wrog0003/ECE4191/CAD/Self_designed_parts/Wheels_Main.SLDPRT

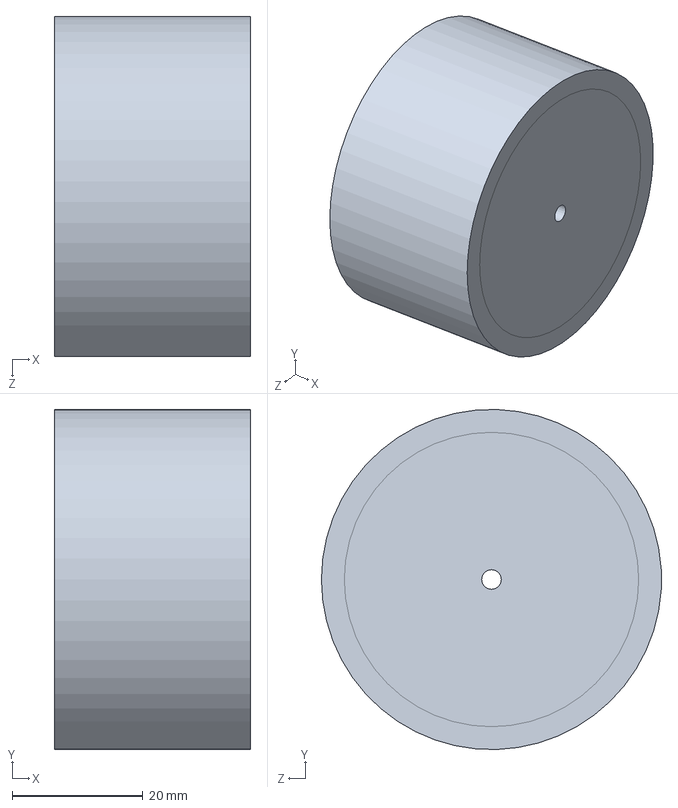
[picture p8: CAD file, 2024-09-03]
CAD/Self_designed_parts/Wheels_Main.SLDPRT
30.0 x 52.0 x 52.0 mm
