wrog0003/ECE4191/CAD/Self_designed_parts/Wheels_Secondary.SLDASM

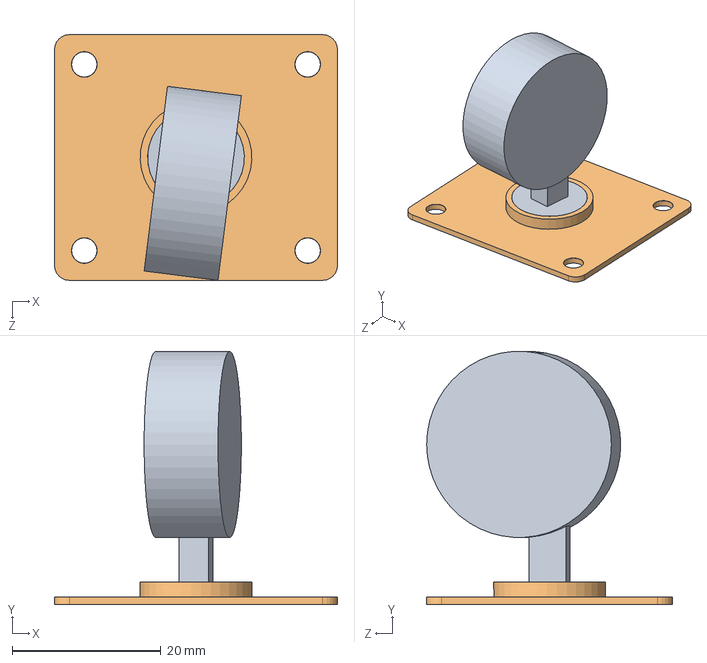
[picture p9: CAD file, 2024-09-03]
CAD/Self_designed_parts/Wheels_Secondary.SLDASM
38.0 x 34.0 x 33.0 mm
Wheels_Secondary_Bottom
Wheels_Secondary_Top
