wrog0003/ECE4191/CAD/Self_designed_parts/TestingAssembly.SLDASM

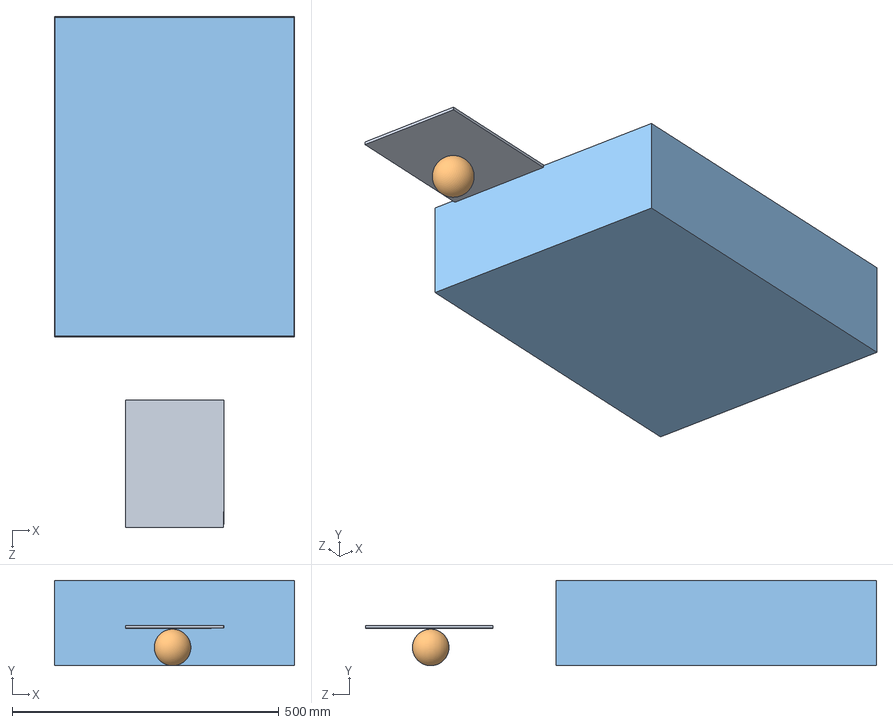
[picture p10: CAD file, 2024-08-25]
CAD/Self_designed_parts/TestingAssembly.SLDASM
450.0 x 160.0 x 957.0 mm
Baseplate
TennisBall(Max)
CollectionBox
