wrog0003/ECE4191/CAD/Self_designed_parts/BumperAssembly.SLDASM

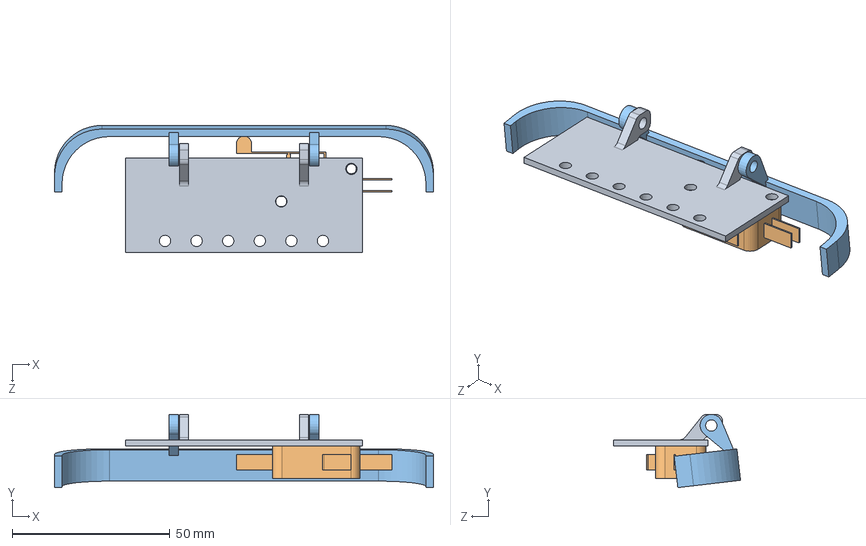
[picture p11: CAD file, 2024-08-25]
CAD/Self_designed_parts/BumperAssembly.SLDASM
120.0 x 23.2 x 40.3 mm
BumperBase
V-156-125 Switch
Bumper
