wrog0003/ECE4191/CAD/Self_designed_parts/CameraAndMount.SLDASM

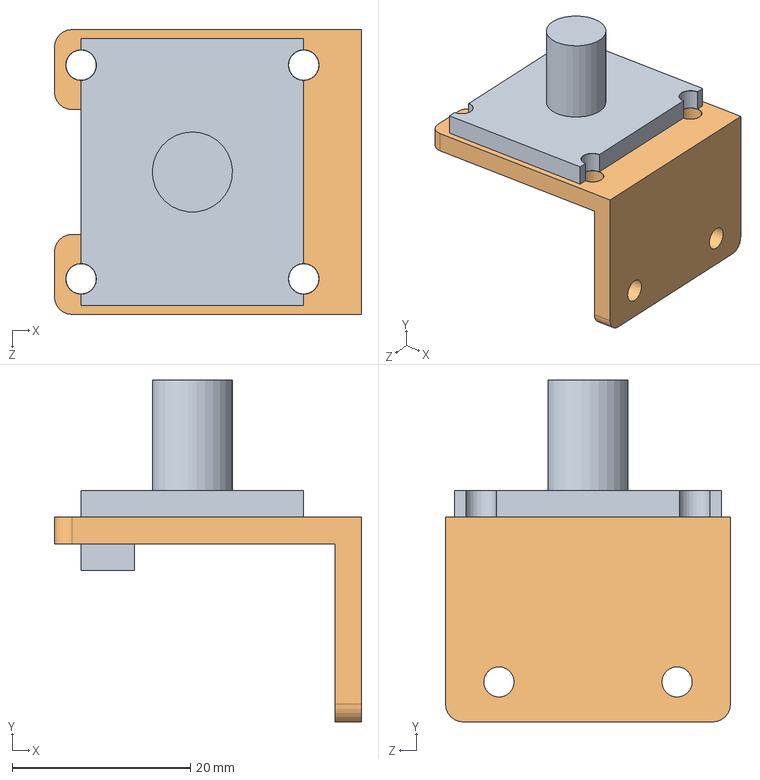
[picture p12: CAD file, 2024-08-25]
CAD/Self_designed_parts/CameraAndMount.SLDASM
34.5 x 38.4 x 32.0 mm
CameraBase
CameraMount
