wrog0003/ECE4191/CAD/Self_designed_parts/ClawAssembly.SLDASM

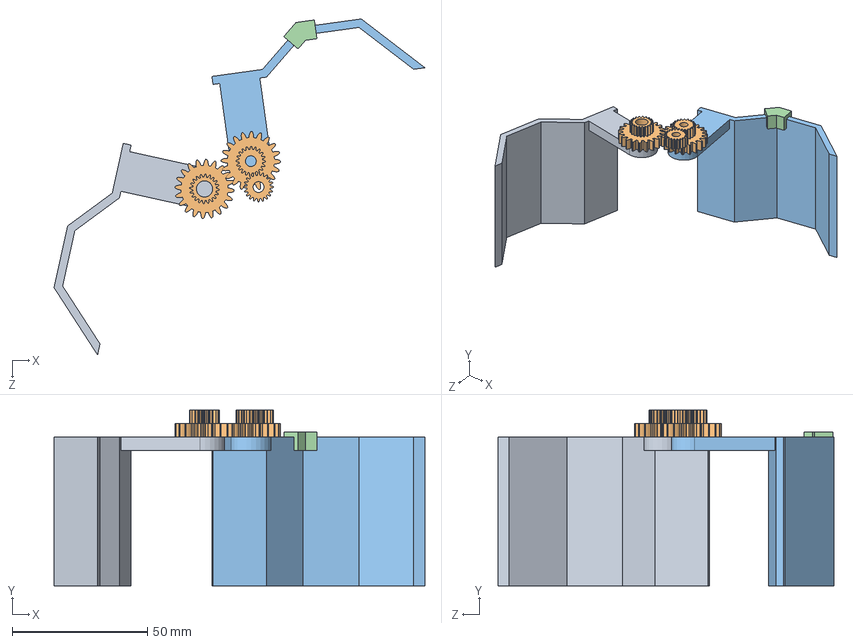
[picture p13: CAD file, 2024-08-25]
CAD/Self_designed_parts/ClawAssembly.SLDASM
137.2 x 65.0 x 124.3 mm
ClawRight
spur gear_am x 6
ClawLeft
Part1^ClawLeftAssembly
