wrog0003/ECE4191/CAD/CameraMount/CameraMountClamp.SLDPRT

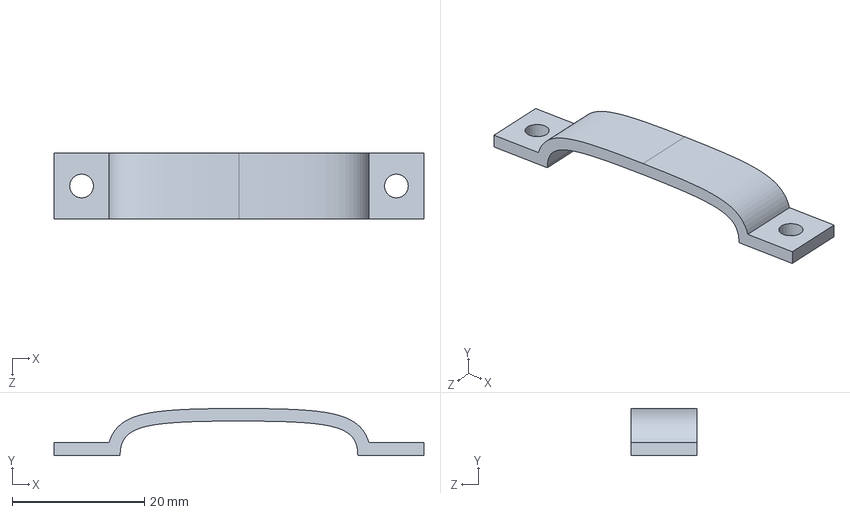
[picture p14: CAD file, 2024-10-14]
CAD/CameraMount/CameraMountClamp.SLDPRT
55.9 x 7.10 x 10.0 mm
