wrog0003/ECE4191/CAD/Ready to Make/3D Printing/Track_Gear.STL

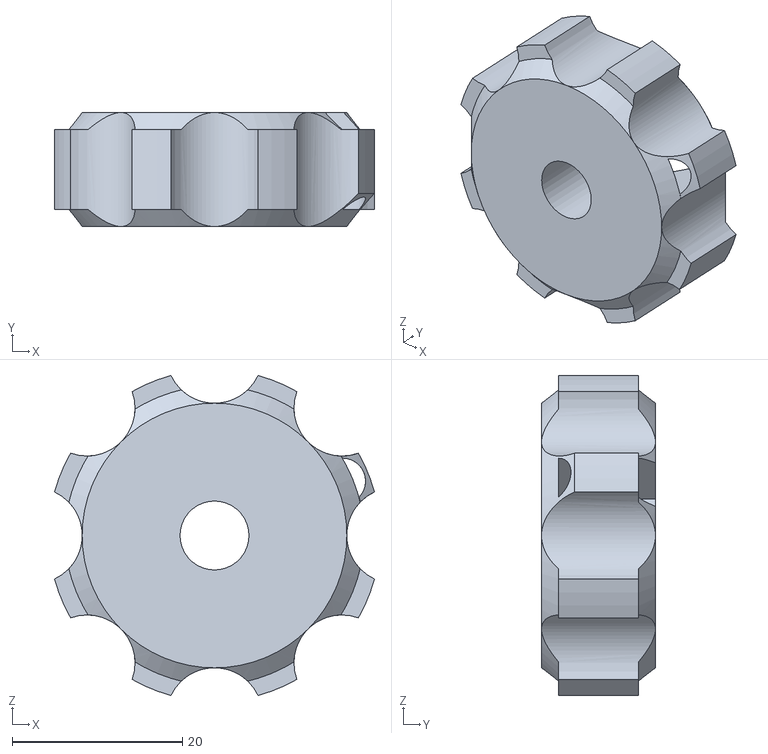
[picture p15: CAD file, 2024-09-18]
CAD/Ready to Make/3D Printing/Track_Gear.STL
37.6 x 13.4 x 37.6
