wrog0003/ECE4191/CAD/Ready to Make/Laser Cutting/PusherFlap.DXF

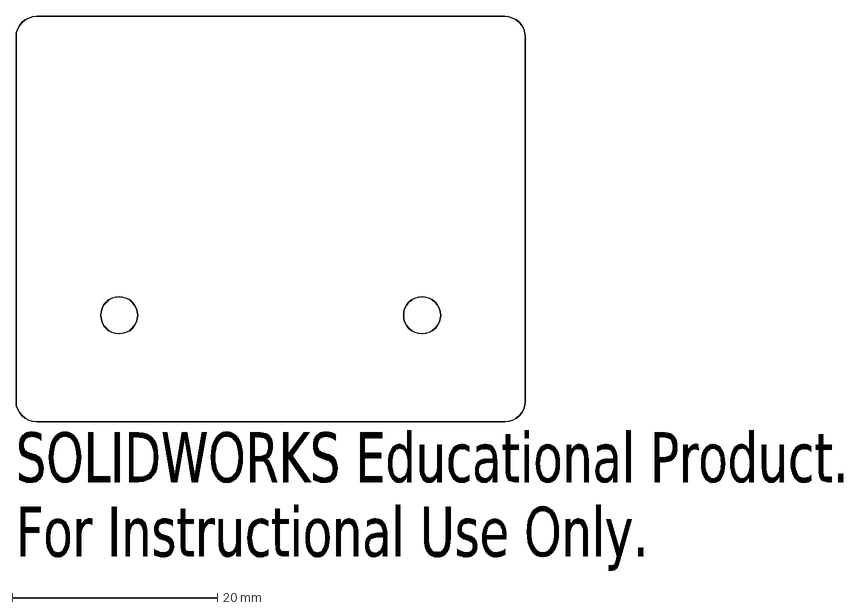
[picture p16: CAD file, 2024-09-16]
CAD/Ready to Make/Laser Cutting/PusherFlap.DXF
SOLIDWORKS Educational Product.
For Instructional Use Only.
