wrog0003/ECE4191/CAD/Self_designed_parts/Adaptors/GearMount_new.SLDPRT

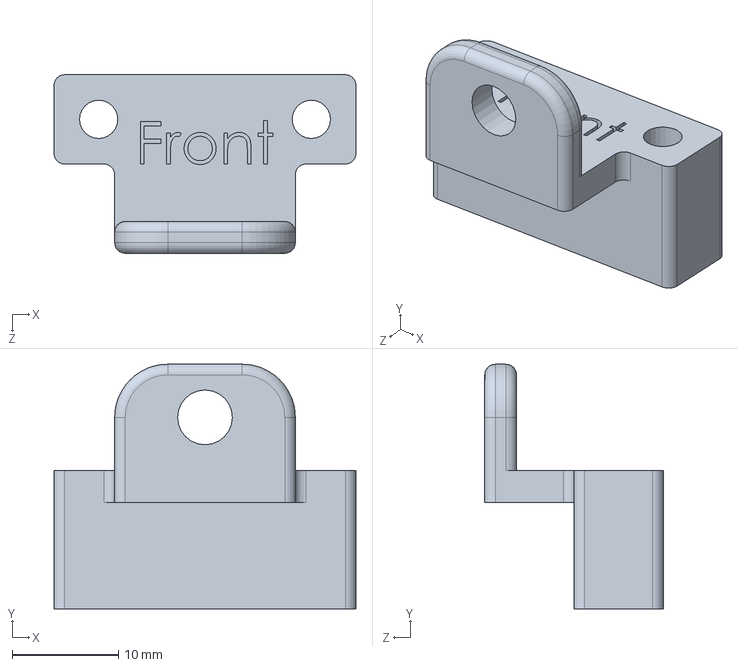
[picture p17: CAD file, 2024-10-04]
CAD/Self_designed_parts/Adaptors/GearMount_new.SLDPRT
28.4 x 23.0 x 16.8 mm
