wrog0003/ECE4191/CAD/Self_designed_parts/CameraMountSection/Battery.SLDPRT

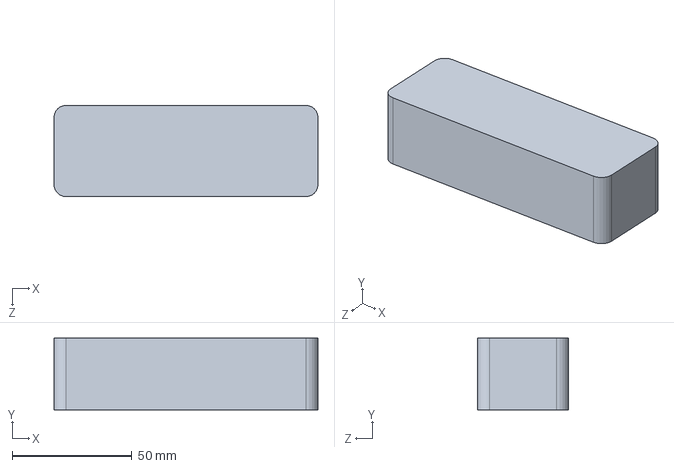
[picture p18: CAD file, 2024-10-14]
CAD/Self_designed_parts/CameraMountSection/Battery.SLDPRT
110.0 x 30.0 x 38.0 mm
