wrog0003/ECE4191/CAD/Self_designed_parts/FunnelMount/FunnelAdaptor.SLDPRT

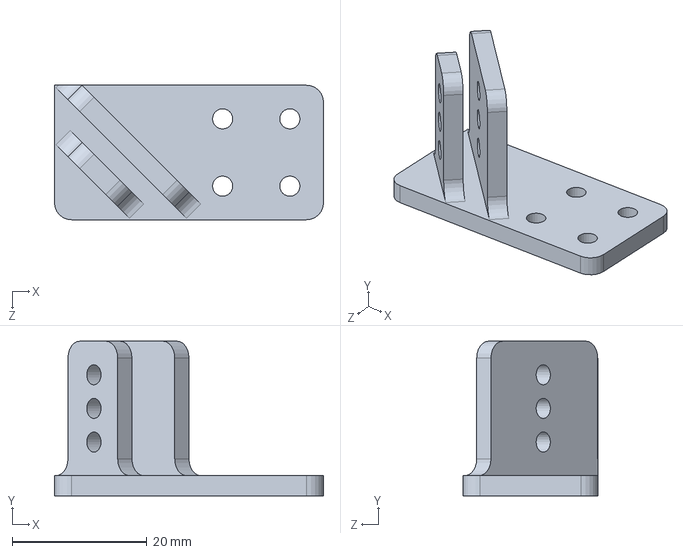
[picture p19: CAD file, 2024-10-14]
CAD/Self_designed_parts/FunnelMount/FunnelAdaptor.SLDPRT
40.0 x 23.0 x 20.0 mm
