wrog0003/ECE4191/CAD/Self_designed_parts/HailMary/HM_HUBCAP.SLDPRT

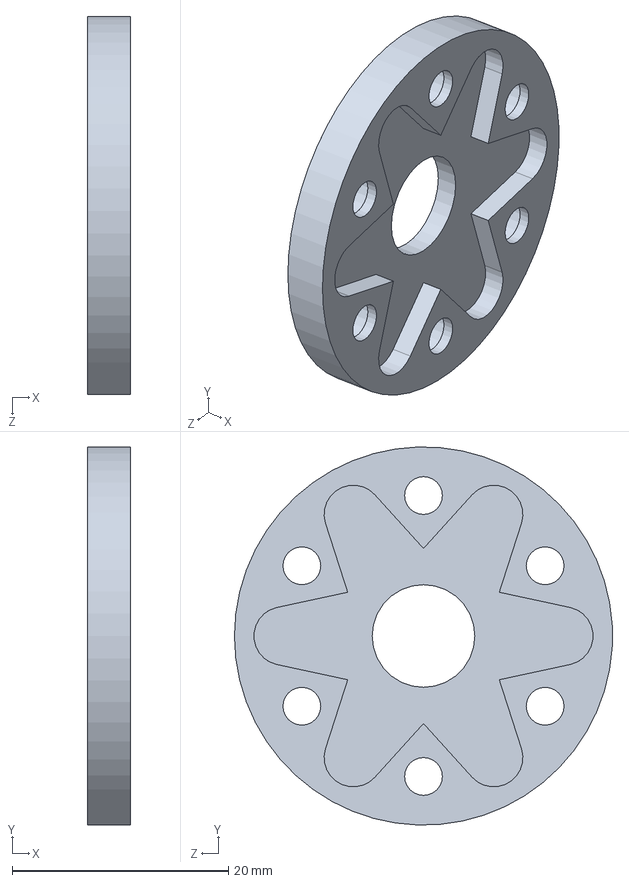
[picture p20: CAD file, 2024-10-16]
CAD/Self_designed_parts/HailMary/HM_HUBCAP.SLDPRT
4.00 x 35.0 x 35.0 mm
