wrog0003/ECE4191/CAD/Self_designed_parts/SupportBracket.SLDPRT

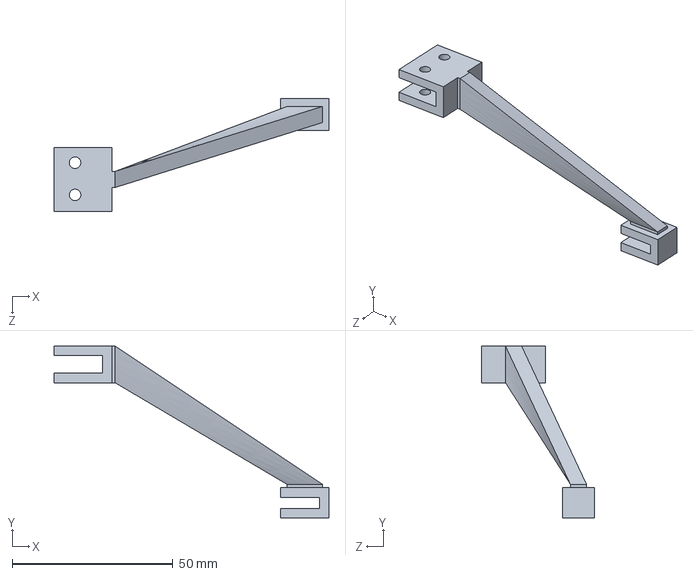
[picture p21: CAD file, 2024-10-14]
CAD/Self_designed_parts/SupportBracket.SLDPRT
85.5 x 53.4 x 35.2 mm
