wrog0003/ECE4191/CAD/CameraMount/CameraMountBase.SLDPRT

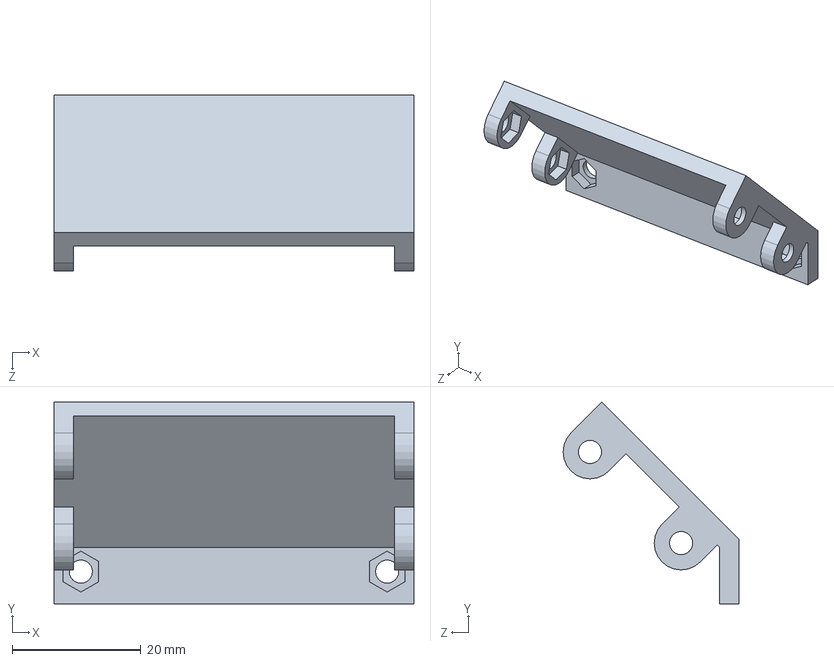
[picture p22: CAD file, 2024-10-14]
CAD/CameraMount/CameraMountBase.SLDPRT
55.9 x 31.3 x 27.3 mm
