wrog0003/ECE4191/CAD/Given_parts/MG995/MG995.SLDPRT

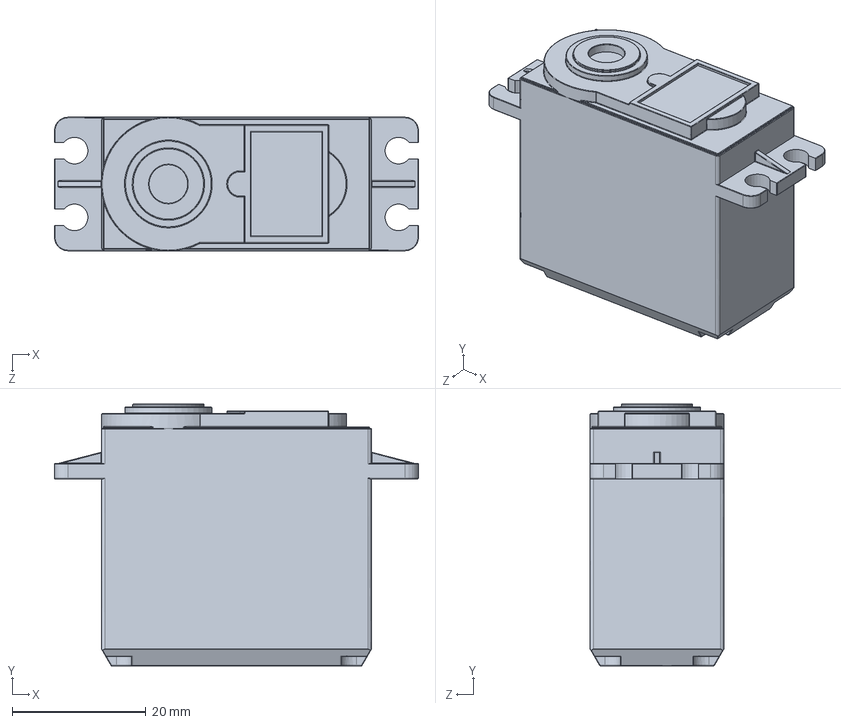
[picture p23: CAD file, 2024-10-05]
CAD/Given_parts/MG995/MG995.SLDPRT
54.5 x 39.2 x 20.0 mm
