wrog0003/ECE4191/CAD/Given_parts/Microswitch.SLDPRT

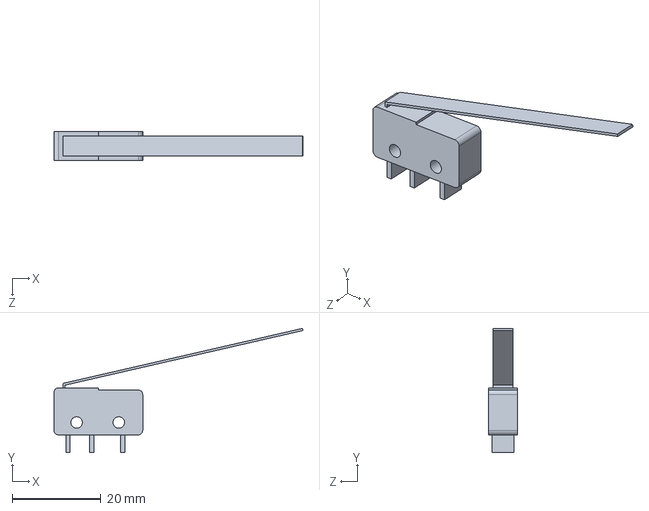
[picture p24: CAD file, 2024-10-04]
CAD/Given_parts/Microswitch.SLDPRT
56.1 x 28.0 x 6.50 mm
