wrog0003/ECE4191/CAD/Ready to Make/3D Printing/SG90C Gear Cap.STL

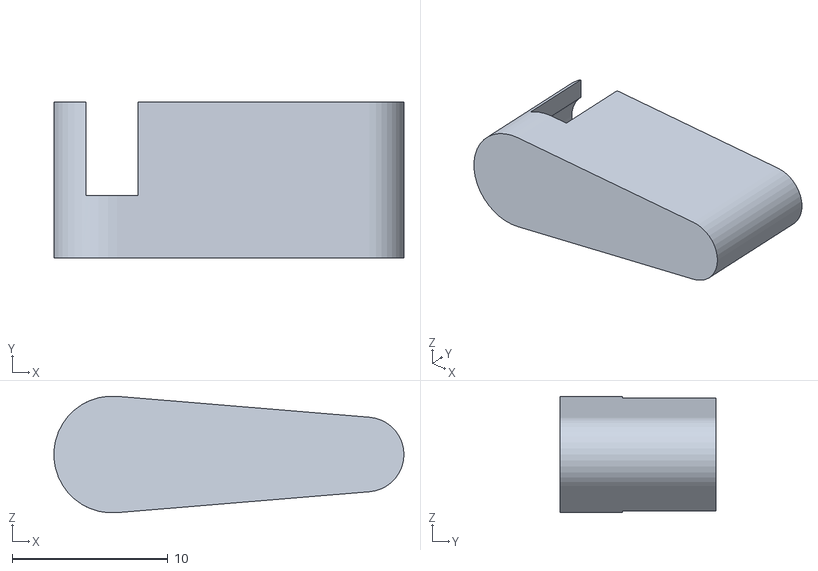
[picture p25: CAD file, 2024-09-18]
CAD/Ready to Make/3D Printing/SG90C Gear Cap.STL
22.5 x 10.0 x 7.48
