wrog0003/ECE4191/CAD/Ready to Make/Laser Cutting/RampChute.DXF

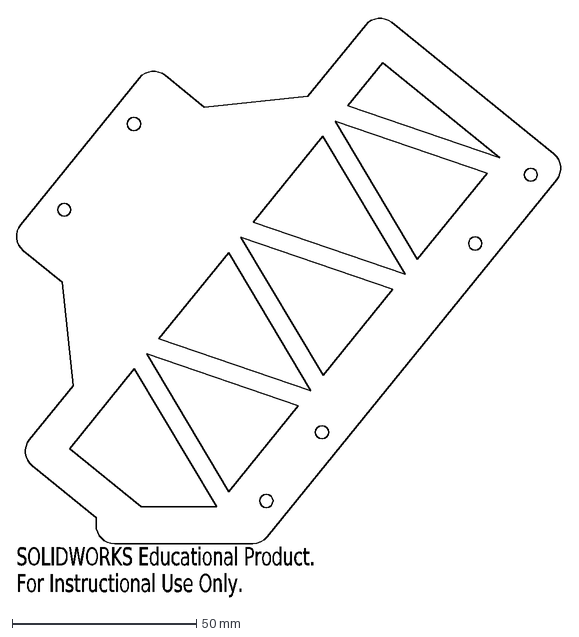
[picture p26: CAD file, 2024-09-16]
CAD/Ready to Make/Laser Cutting/RampChute.DXF
SOLIDWORKS Educational Product.
For Instructional Use Only.
