wrog0003/ECE4191/CAD/Self_designed_parts/Adaptors/GearMountRaiser.SLDPRT

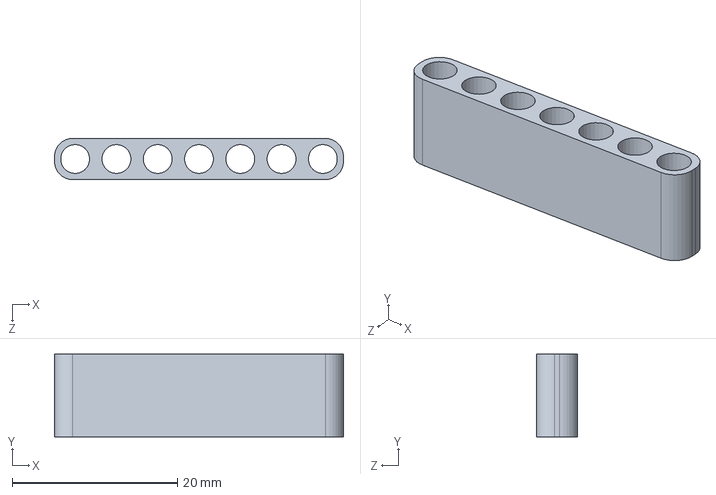
[picture p27: CAD file, 2024-10-02]
CAD/Self_designed_parts/Adaptors/GearMountRaiser.SLDPRT
35.0 x 10.0 x 5.00 mm
