wrog0003/ECE4191/CAD/Self_designed_parts/CameraMountSection/NewServoMountSpacer.SLDPRT

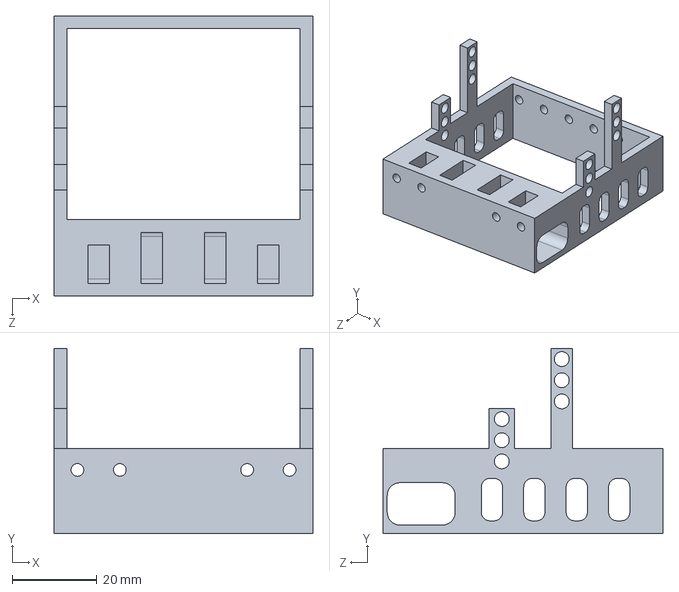
[picture p28: CAD file, 2024-10-14]
CAD/Self_designed_parts/CameraMountSection/NewServoMountSpacer.SLDPRT
61.0 x 43.6 x 66.0 mm
