wrog0003/ECE4191/CAD/Self_designed_parts/FunnelMount/FunnelPlate.SLDPRT

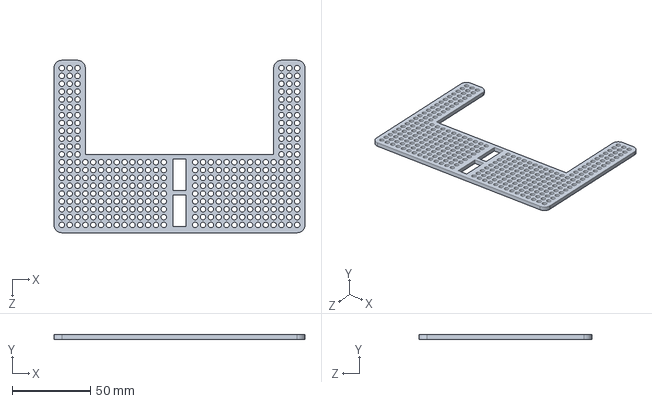
[picture p29: CAD file, 2024-10-14]
CAD/Self_designed_parts/FunnelMount/FunnelPlate.SLDPRT
160.0 x 3.00 x 110.0 mm
