wrog0003/ECE4191/CAD/Self_designed_parts/MotorMount_Helper.SLDPRT

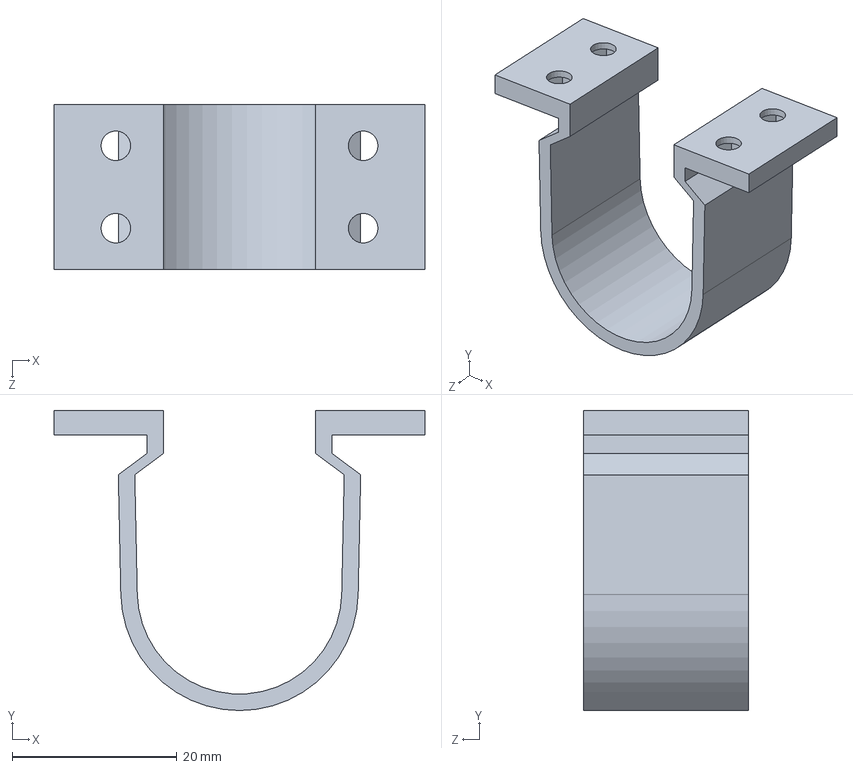
[picture p30: CAD file, 2024-10-14]
CAD/Self_designed_parts/MotorMount_Helper.SLDPRT
45.0 x 36.4 x 20.0 mm
