wrog0003/ECE4191/CAD/CameraMount/CameraLifter.SLDPRT

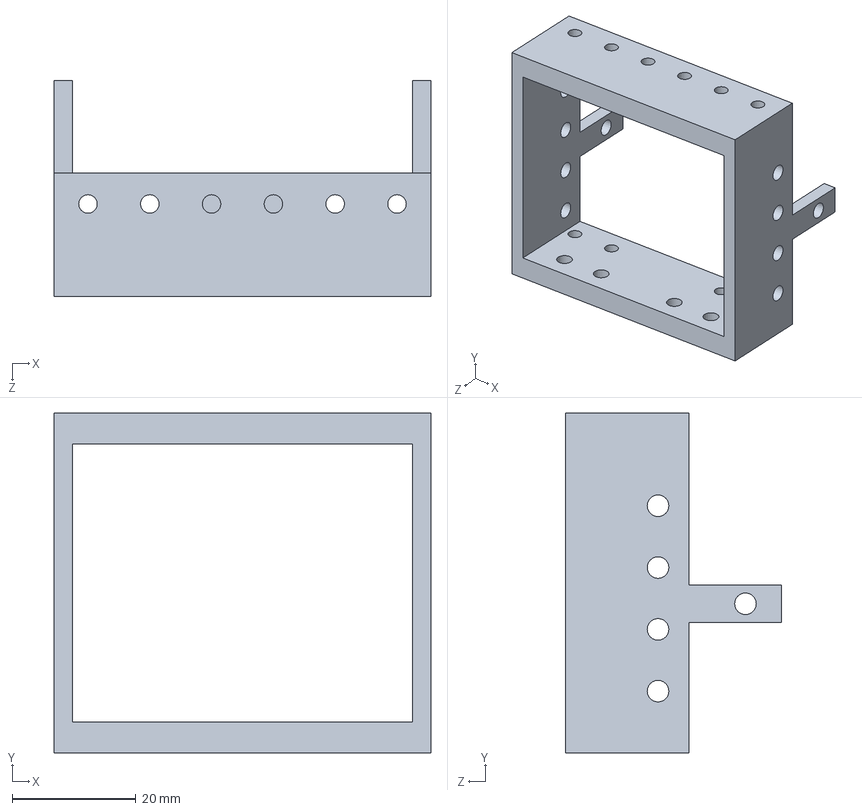
[picture p31: CAD file, 2024-09-30]
CAD/CameraMount/CameraLifter.SLDPRT
61.0 x 55.0 x 35.0 mm
