wrog0003/ECE4191/CAD/Given_parts/Servo_MG995_Star_horn.SLDPRT

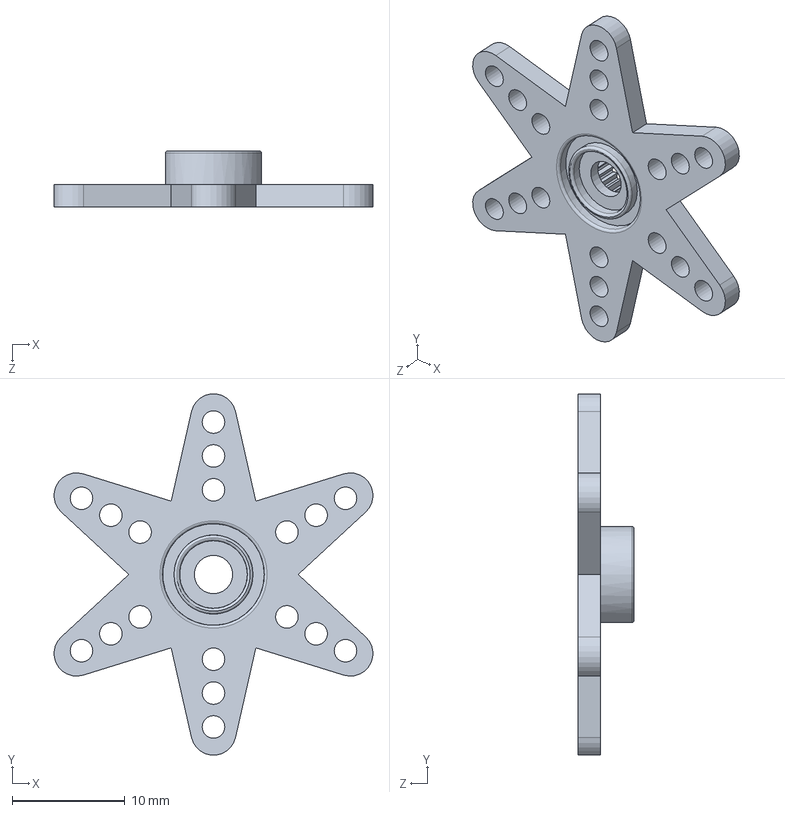
[picture p32: CAD file, 2024-09-30]
CAD/Given_parts/Servo_MG995_Star_horn.SLDPRT
28.2 x 32.0 x 5.00 mm
