wrog0003/ECE4191/CAD/Ready to Make/Laser Cutting/Baseplate.DXF

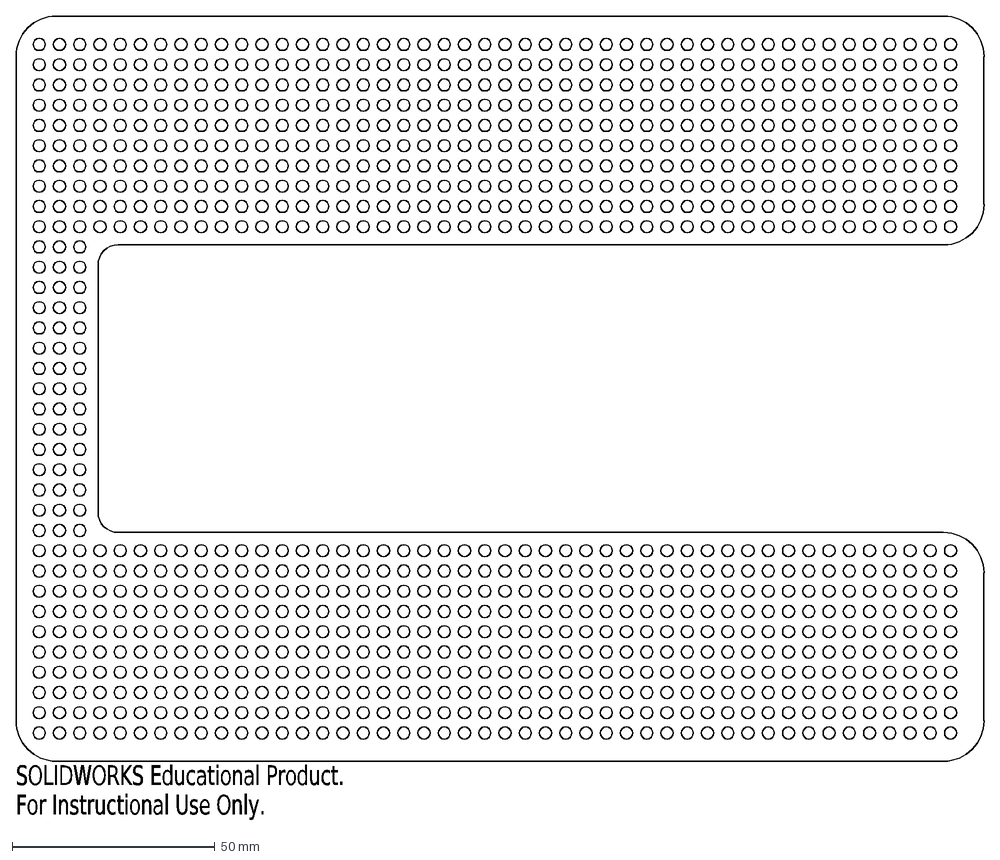
[picture p33: CAD file, 2024-09-16]
CAD/Ready to Make/Laser Cutting/Baseplate.DXF
SOLIDWORKS Educational Product.
For Instructional Use Only.
