wrog0003/ECE4191/CAD/Self_designed_parts/Adaptors/PCBHolder.SLDPRT

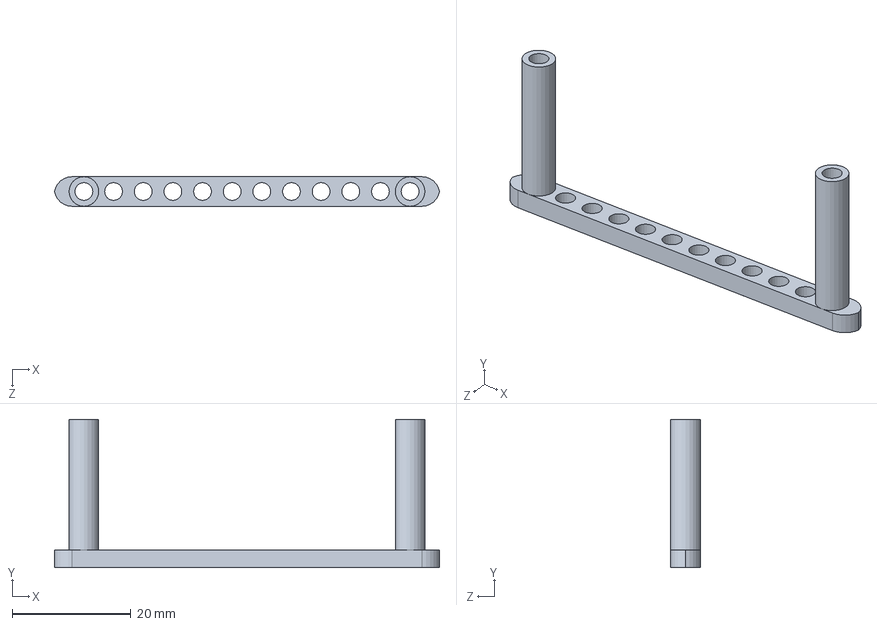
[picture p34: CAD file, 2024-09-27]
CAD/Self_designed_parts/Adaptors/PCBHolder.SLDPRT
64.9 x 25.0 x 5.00 mm
