wrog0003/ECE4191/CAD/Self_designed_parts/BallChute.SLDPRT

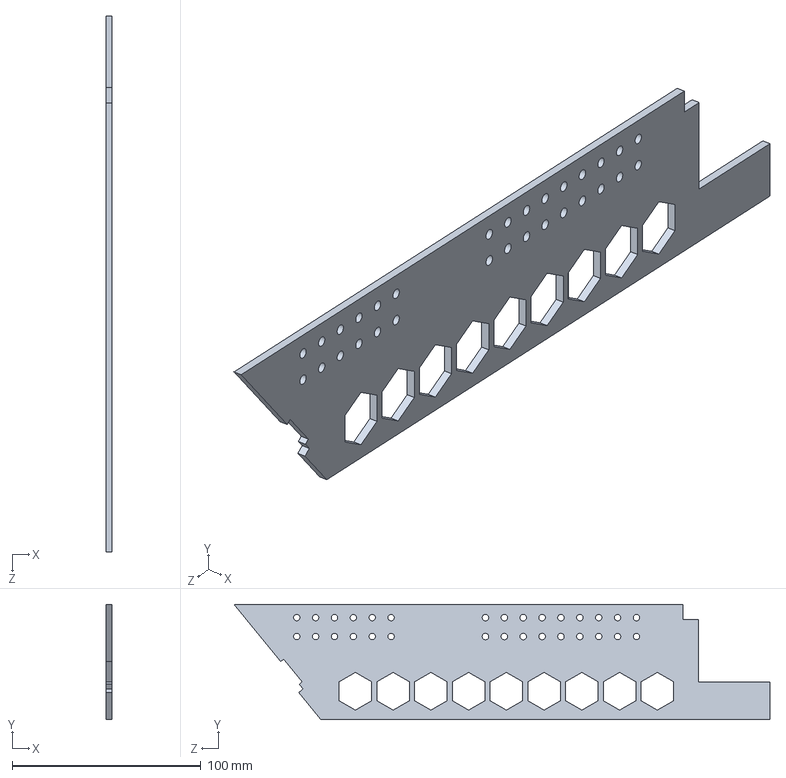
[picture p35: CAD file, 2024-10-14]
CAD/Self_designed_parts/BallChute.SLDPRT
3.00 x 61.0 x 284.0 mm
