wrog0003/ECE4191/CAD/Self_designed_parts/HailMary/HM_LOWERRAMP.SLDPRT

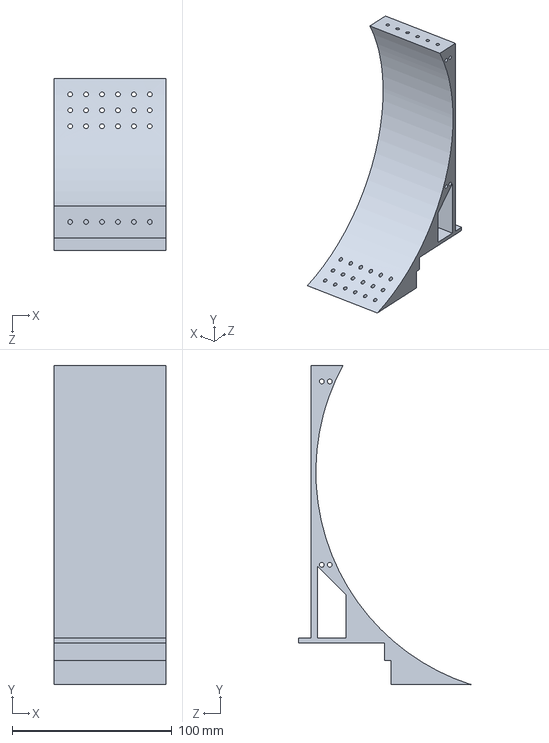
[picture p36: CAD file, 2024-10-16]
CAD/Self_designed_parts/HailMary/HM_LOWERRAMP.SLDPRT
70.0 x 200.0 x 108.0 mm
