wrog0003/ECE4191/CAD/CameraMount/CM_Vertical.SLDPRT

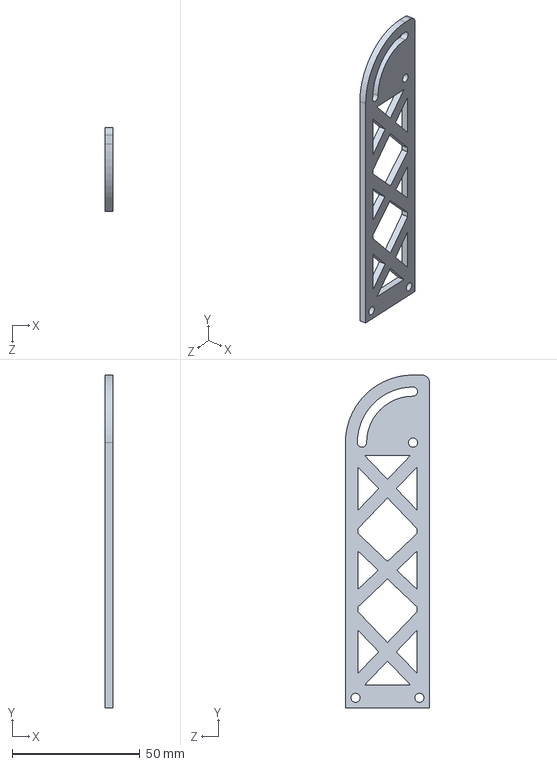
[picture p37: CAD file, 2024-09-16]
CAD/CameraMount/CM_Vertical.SLDPRT
3.00 x 130.5 x 33.0 mm
