wrog0003/ECE4191/CAD/Given_parts/MG995/Shaft.SLDPRT

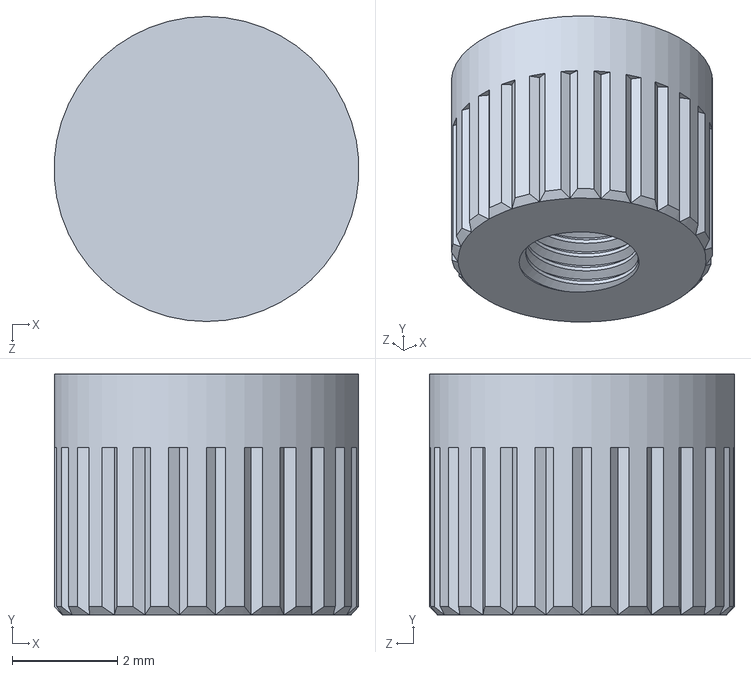
[picture p38: CAD file, 2024-09-30]
CAD/Given_parts/MG995/Shaft.SLDPRT
5.79 x 4.58 x 5.80 mm
