wrog0003/ECE4191/CAD/Given_parts/Raspberry_Pi_4_B.SLDPRT

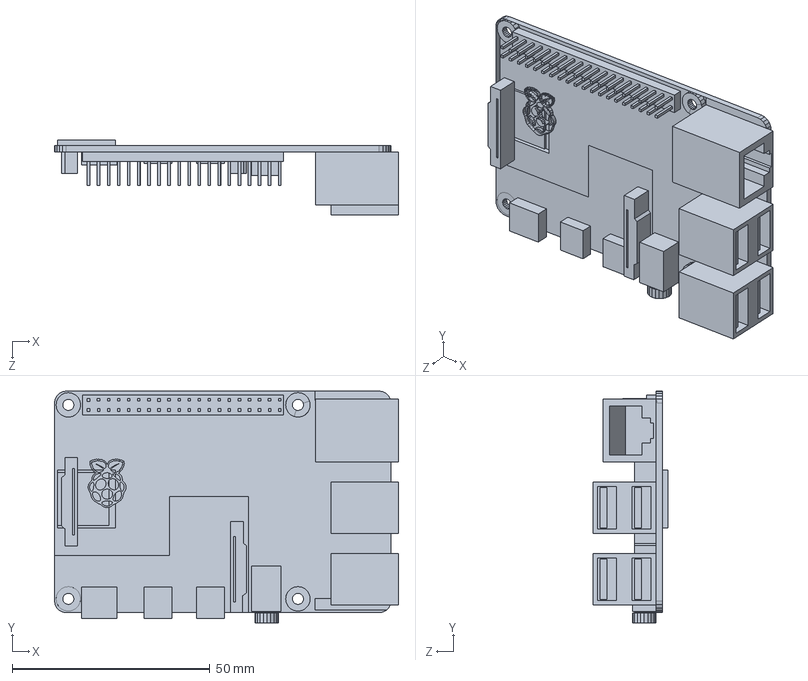
[picture p39: CAD file, 2024-09-18]
CAD/Given_parts/Raspberry_Pi_4_B.SLDPRT
86.9 x 58.6 x 19.0 mm
