wrog0003/ECE4191/CAD/Ready to Make/Laser Cutting/FrontReinforcement.DXF

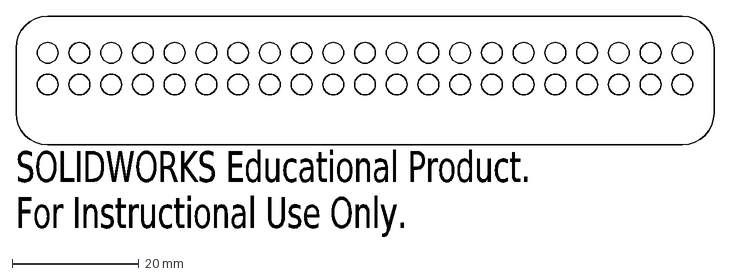
[picture p40: CAD file, 2024-09-16]
CAD/Ready to Make/Laser Cutting/FrontReinforcement.DXF
SOLIDWORKS Educational Product.
For Instructional Use Only.
