wrog0003/ECE4191/CAD/Self_designed_parts/Adaptors/MotorDriverRaiser.SLDPRT

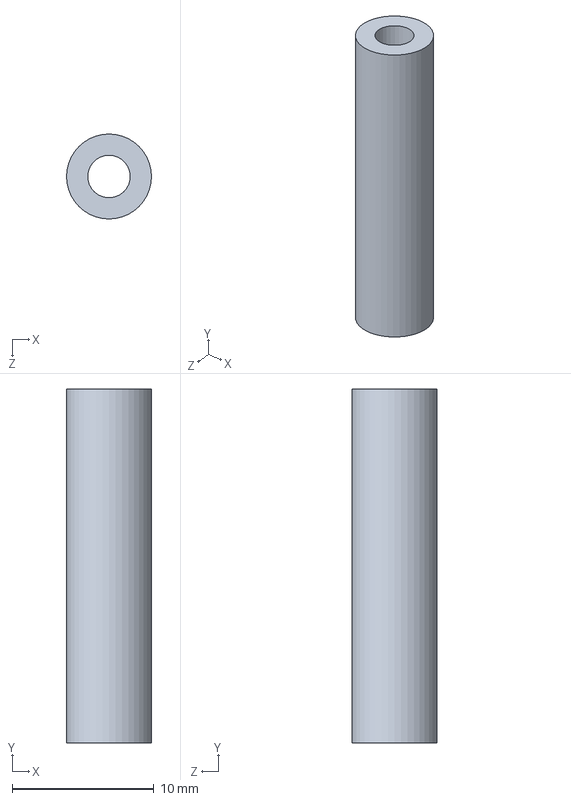
[picture p41: CAD file, 2024-09-26]
CAD/Self_designed_parts/Adaptors/MotorDriverRaiser.SLDPRT
6.00 x 25.0 x 6.00 mm
