wrog0003/ECE4191/CAD/Self_designed_parts/CameraMountSection/WireHousing.SLDPRT

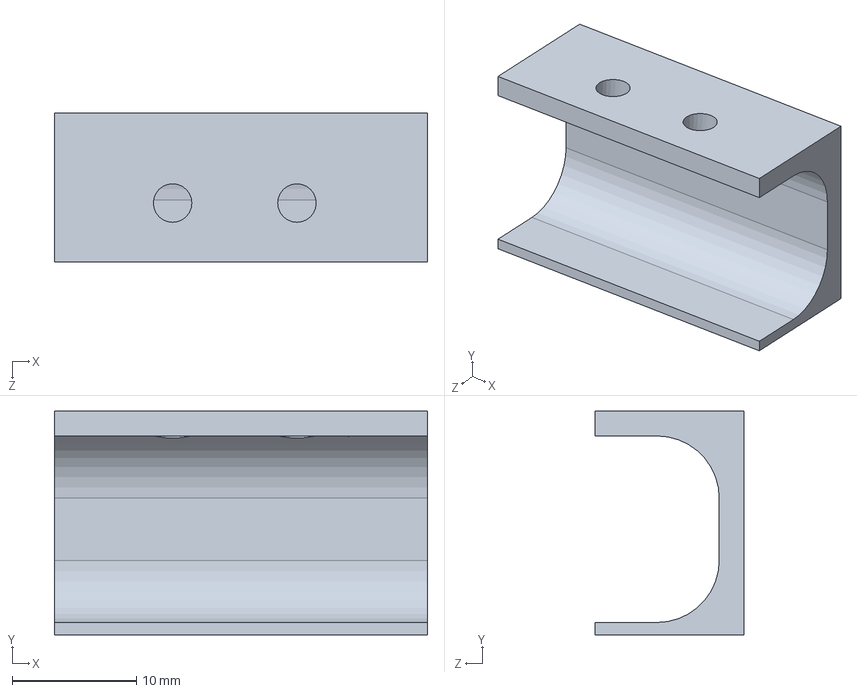
[picture p42: CAD file, 2024-09-19]
CAD/Self_designed_parts/CameraMountSection/WireHousing.SLDPRT
30.0 x 18.0 x 12.0 mm
