wrog0003/ECE4191/CAD/Self_designed_parts/FunnelMount/ButtonHolder.SLDPRT

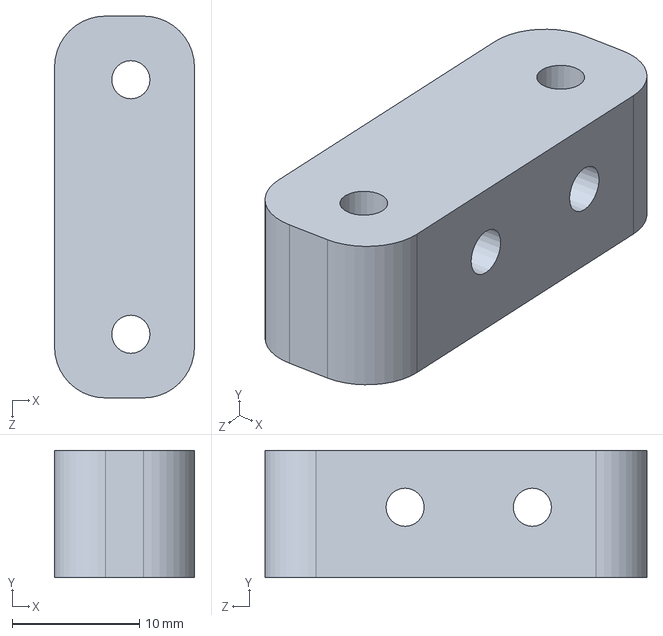
[picture p43: CAD file, 2024-10-14]
CAD/Self_designed_parts/FunnelMount/ButtonHolder.SLDPRT
11.0 x 10.0 x 30.0 mm
