wrog0003/ECE4191/CAD/Self_designed_parts/RearMountBracket_Right.SLDPRT

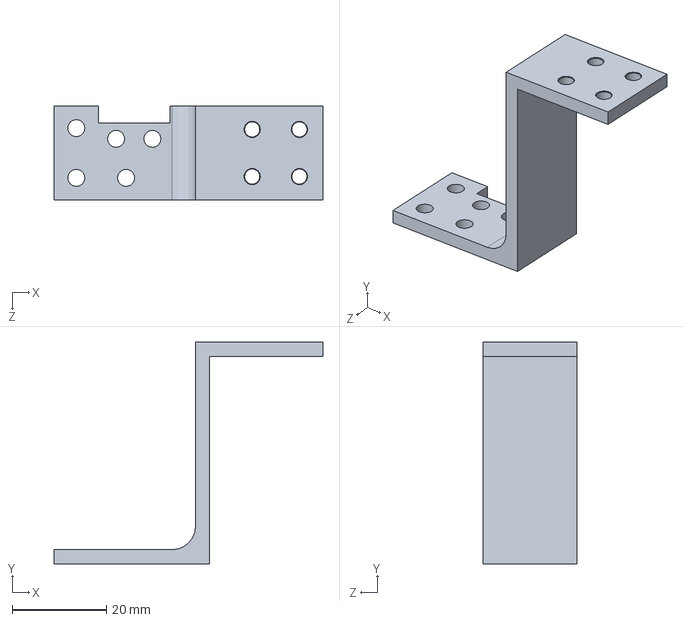
[picture p44: CAD file, 2024-10-14]
CAD/Self_designed_parts/RearMountBracket_Right.SLDPRT
57.0 x 47.0 x 20.0 mm
