wrog0003/ECE4191/CAD/CameraMount/CM_Mount.SLDPRT

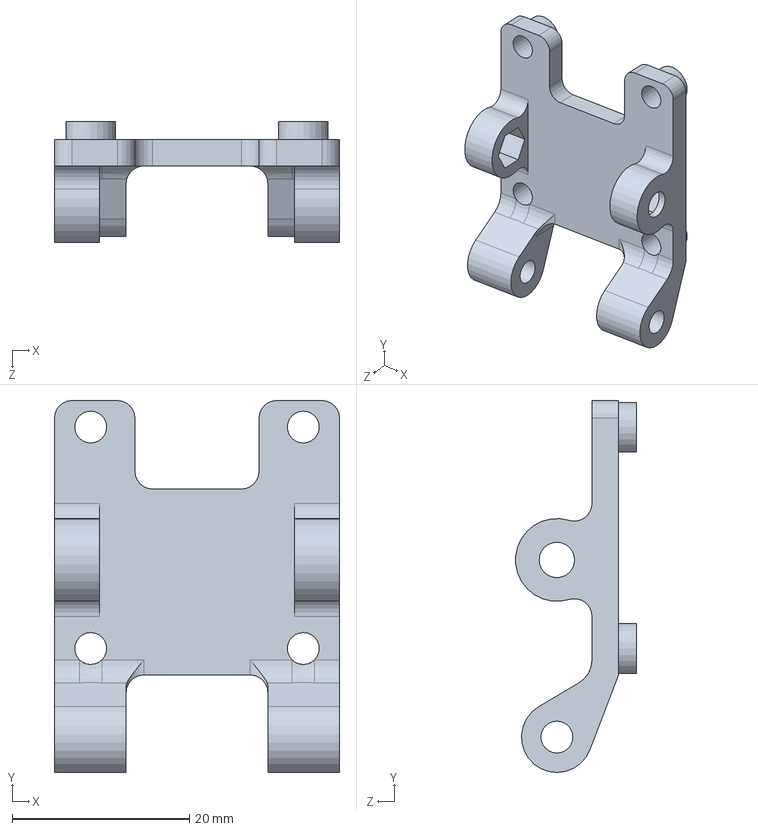
[picture p45: CAD file, 2024-09-16]
CAD/CameraMount/CM_Mount.SLDPRT
32.2 x 42.0 x 13.6 mm
