wrog0003/ECE4191/CAD/Given_parts/MG90S horn.STEP

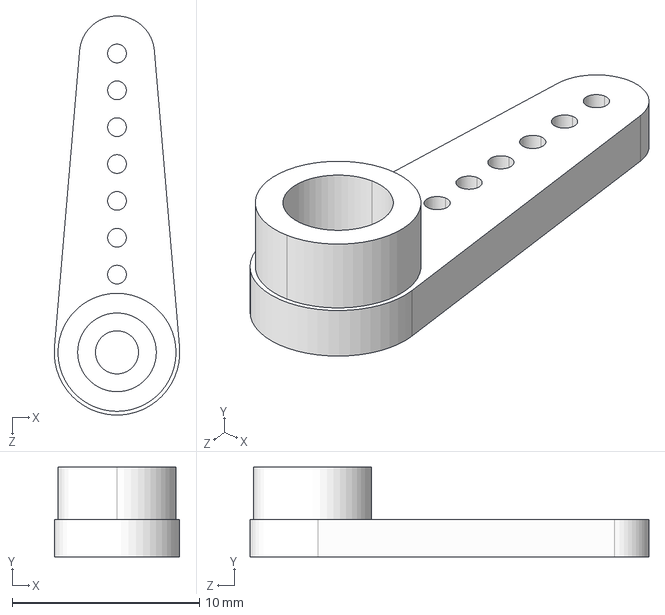
[picture p46: CAD file, 2024-09-16]
CAD/Given_parts/MG90S horn.STEP
6.70 x 4.80 x 21.3 mm
