wrog0003/ECE4191/CAD/Ready to Make/Laser Cutting/ServoMount.DXF

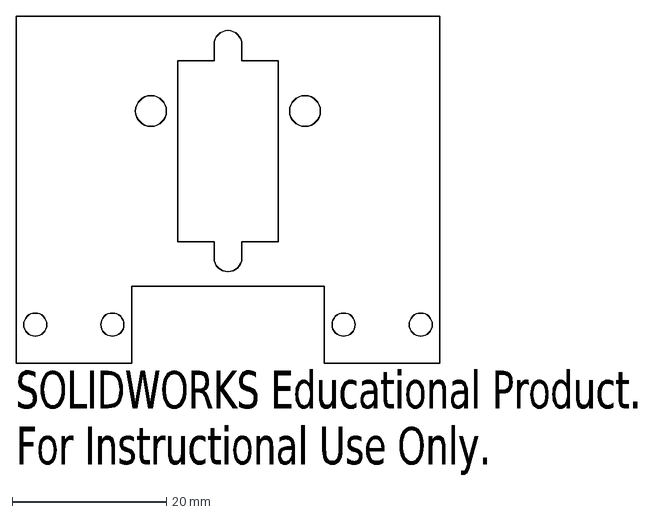
[picture p47: CAD file, 2024-09-03]
CAD/Ready to Make/Laser Cutting/ServoMount.DXF
SOLIDWORKS Educational Product.
For Instructional Use Only.
