wrog0003/ECE4191/CAD/Self_designed_parts/Adaptors/RampChuteBracket.STL

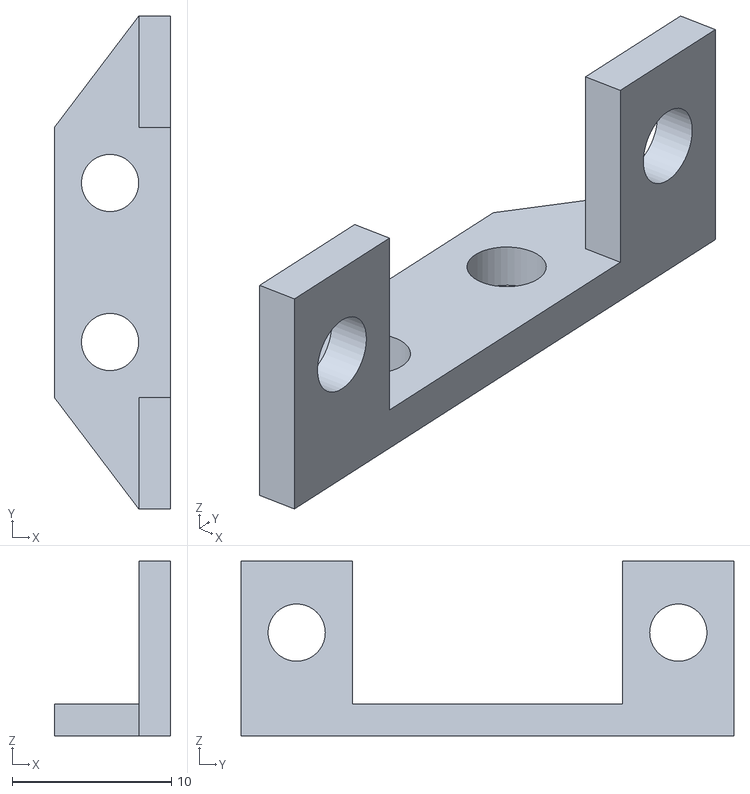
[picture p48: CAD file, 2024-09-18]
CAD/Self_designed_parts/Adaptors/RampChuteBracket.STL
7.30 x 31.0 x 11.0
