wrog0003/ECE4191/CAD/Self_designed_parts/Baseplate.SLDPRT

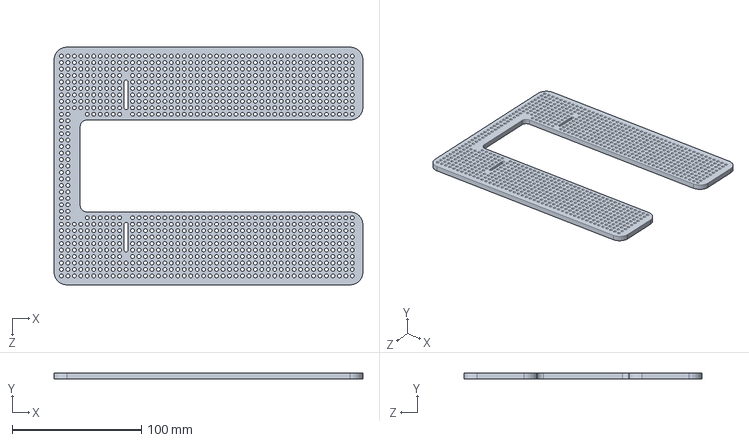
[picture p49: CAD file, 2024-10-14]
CAD/Self_designed_parts/Baseplate.SLDPRT
239.0 x 5.00 x 184.0 mm
