wrog0003/ECE4191/CAD/Self_designed_parts/FunnelMount/Funnel.SLDPRT

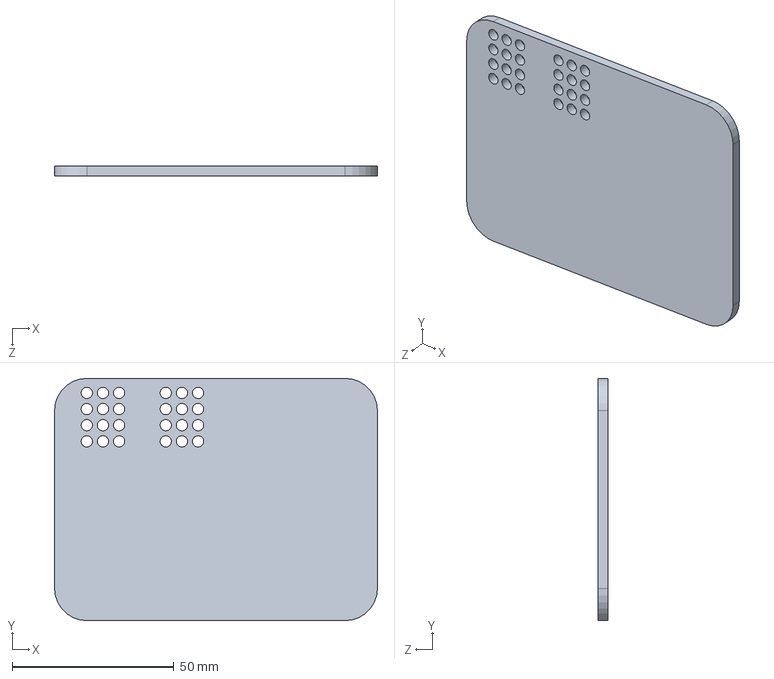
[picture p50: CAD file, 2024-10-14]
CAD/Self_designed_parts/FunnelMount/Funnel.SLDPRT
100.0 x 75.0 x 3.00 mm
