wrog0003/ECE4191/CAD/Self_designed_parts/HailMary/HM_SidePateRIGHT.SLDPRT

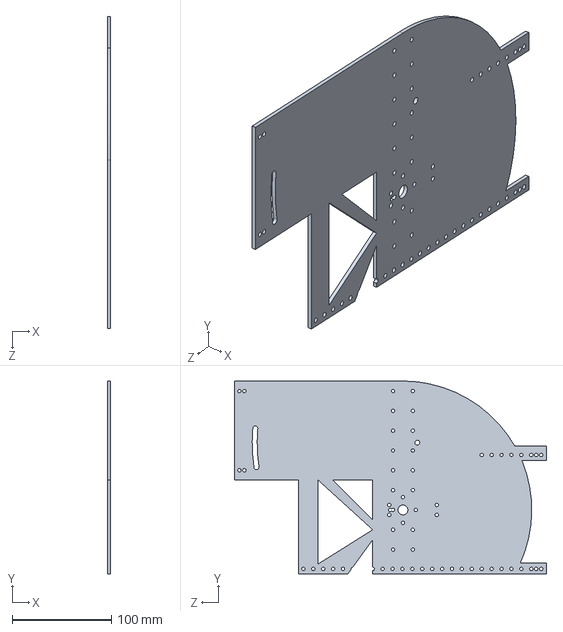
[picture p51: CAD file, 2024-10-14]
CAD/Self_designed_parts/HailMary/HM_SidePateRIGHT.SLDPRT
3.00 x 194.5 x 314.9 mm
