wrog0003/ECE4191/CAD/CameraMount/CM_Base.SLDPRT

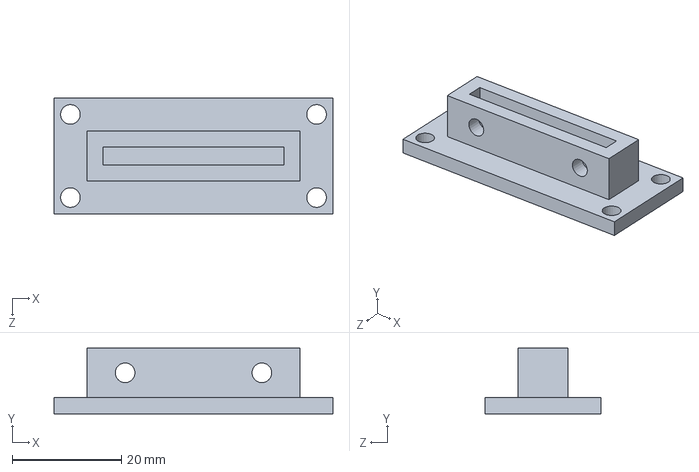
[picture p52: CAD file, 2024-09-16]
CAD/CameraMount/CM_Base.SLDPRT
51.0 x 12.0 x 21.2 mm
