wrog0003/ECE4191/CAD/Given_parts/Logitech c270.SLDPRT

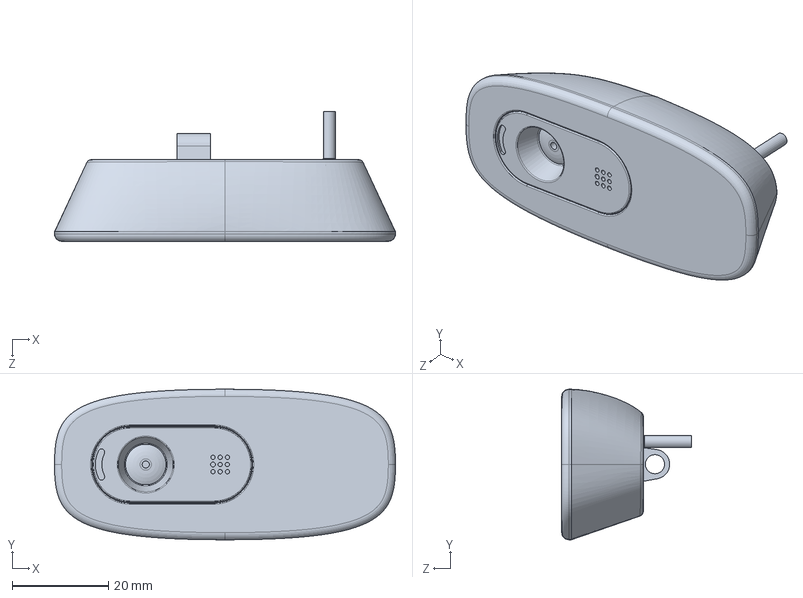
[picture p53: CAD file, 2024-09-16]
CAD/Given_parts/Logitech c270.SLDPRT
71.0 x 31.4 x 27.0 mm
