wrog0003/ECE4191/CAD/Ready to Make/Laser Cutting/RampWheelBracket.DXF

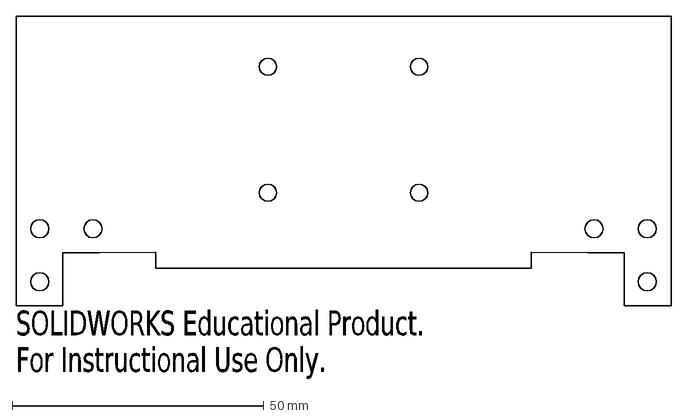
[picture p54: CAD file, 2024-09-03]
CAD/Ready to Make/Laser Cutting/RampWheelBracket.DXF
SOLIDWORKS Educational Product.
For Instructional Use Only.
