wrog0003/ECE4191/CAD/Self_designed_parts/Adaptors/100mm2shaftCap.SLDPRT

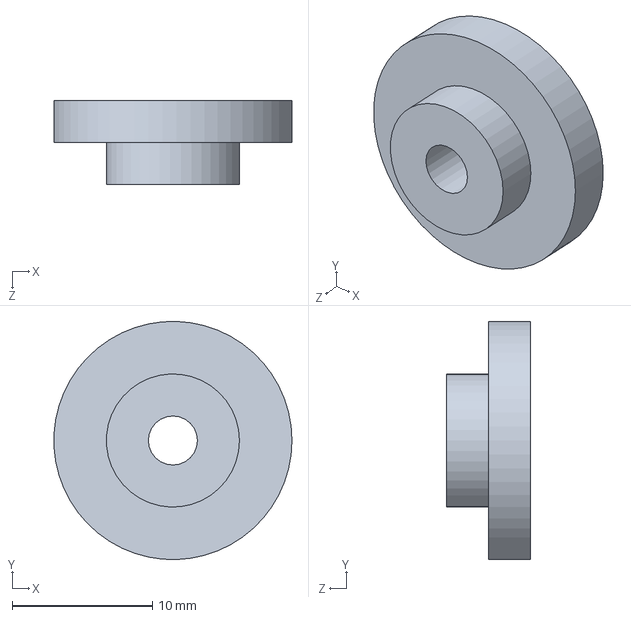
[picture p55: CAD file, 2024-09-16]
CAD/Self_designed_parts/Adaptors/100mm2shaftCap.SLDPRT
17.0 x 17.0 x 6.00 mm
