wrog0003/ECE4191/CAD/Self_designed_parts/CameraMountSection/LipoHolder.SLDPRT

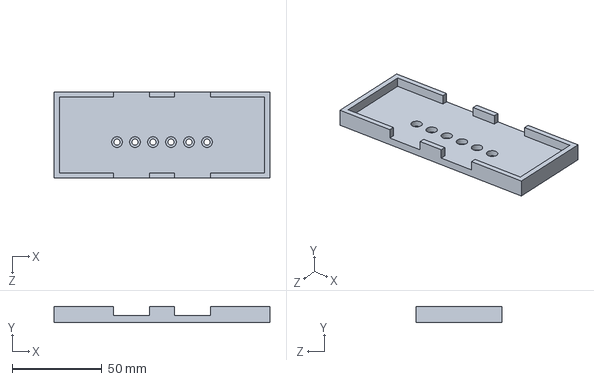
[picture p56: CAD file, 2024-09-18]
CAD/Self_designed_parts/CameraMountSection/LipoHolder.SLDPRT
120.0 x 9.00 x 48.0 mm
