wrog0003/ECE4191/CAD/Self_designed_parts/FunnelMount/FunnelAdaptorFlip.SLDPRT

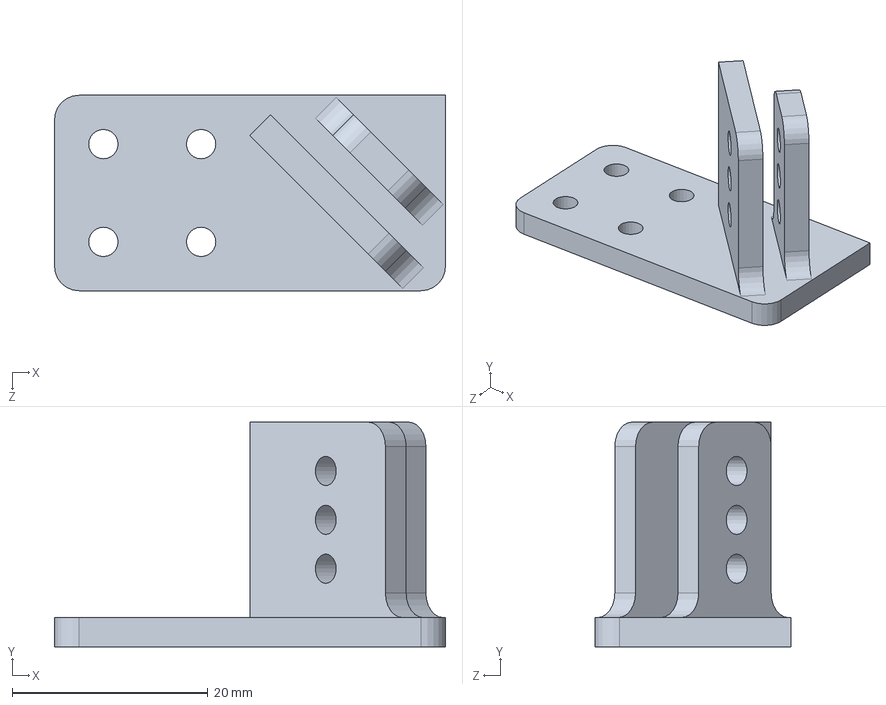
[picture p57: CAD file, 2024-10-02]
CAD/Self_designed_parts/FunnelMount/FunnelAdaptorFlip.SLDPRT
40.0 x 23.0 x 20.0 mm
