wrog0003/ECE4191/CAD/Self_designed_parts/HailMary/HM_HUBCENTRE.SLDPRT

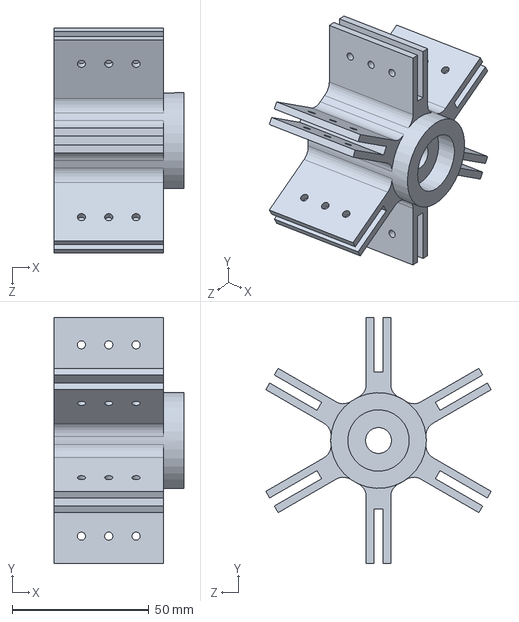
[picture p58: CAD file, 2024-10-14]
CAD/Self_designed_parts/HailMary/HM_HUBCENTRE.SLDPRT
47.5 x 90.0 x 82.4 mm
