wrog0003/ECE4191/CAD/Self_designed_parts/MotorMountSpacer.SLDPRT

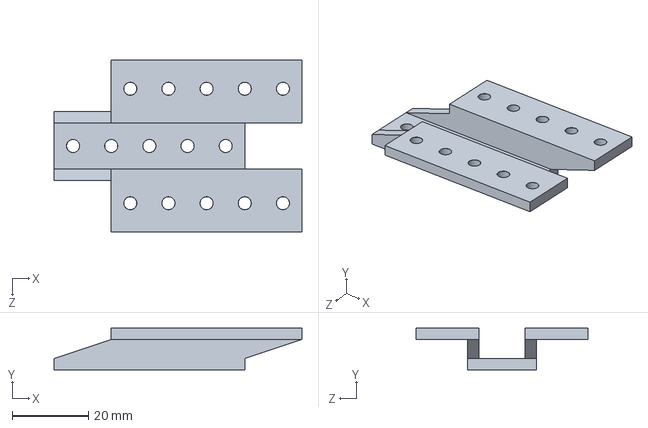
[picture p59: CAD file, 2024-10-14]
CAD/Self_designed_parts/MotorMountSpacer.SLDPRT
65.0 x 11.0 x 45.0 mm
