wrog0003/ECE4191/CAD/Given_parts/Logitech c270b.SLDPRT

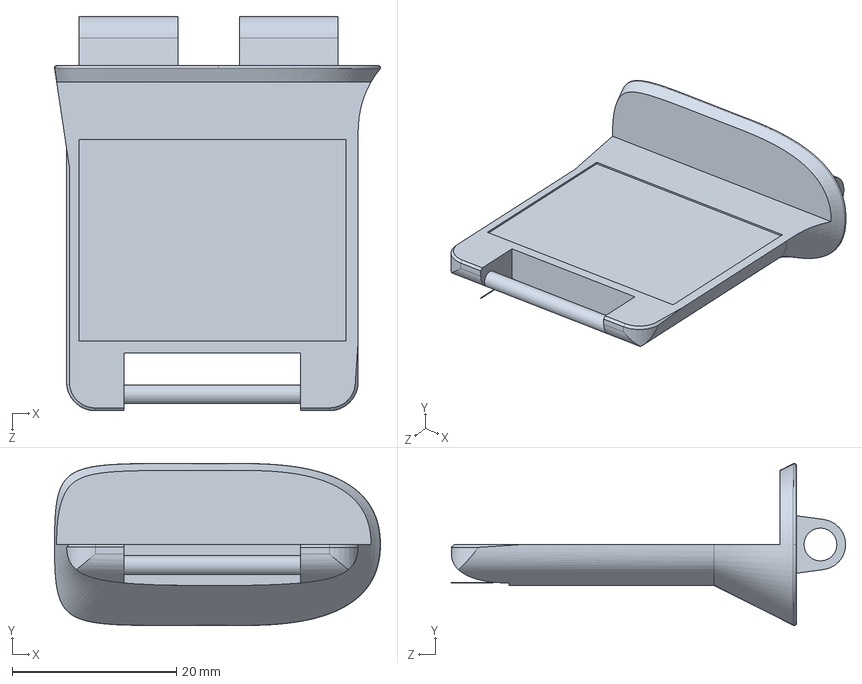
[picture p60: CAD file, 2024-09-16]
CAD/Given_parts/Logitech c270b.SLDPRT
39.7 x 19.7 x 48.0 mm
