wrog0003/ECE4191/CAD/Ready to Make/Laser Cutting/Ramp.DXF

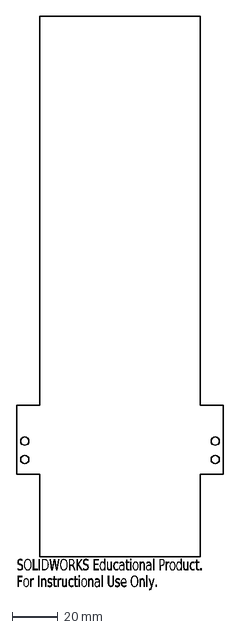
[picture p61: CAD file, 2024-09-03]
CAD/Ready to Make/Laser Cutting/Ramp.DXF
SOLIDWORKS Educational Product.
For Instructional Use Only.
