wrog0003/ECE4191/CAD/Self_designed_parts/Adaptors/100mm2shaft.SLDPRT

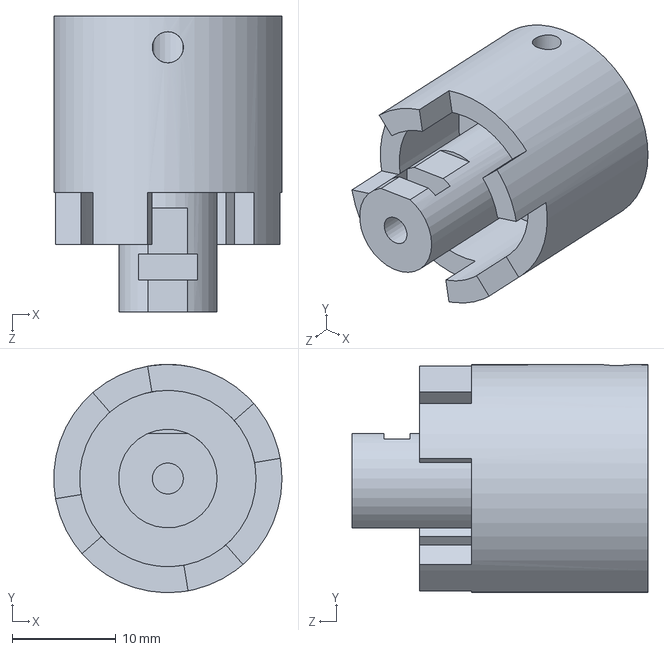
[picture p62: CAD file, 2024-09-16]
CAD/Self_designed_parts/Adaptors/100mm2shaft.SLDPRT
22.0 x 22.0 x 28.5 mm
