wrog0003/ECE4191/CAD/Given_parts/Logitech c270c.SLDPRT

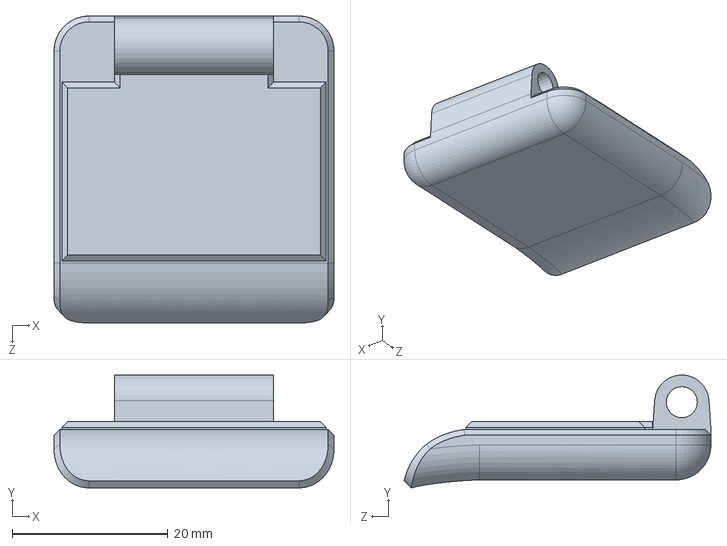
[picture p63: CAD file, 2024-09-16]
CAD/Given_parts/Logitech c270c.SLDPRT
36.0 x 14.5 x 39.5 mm
