wrog0003/ECE4191/CAD/Self_designed_parts/Adaptors/FrontReinforcement.SLDPRT

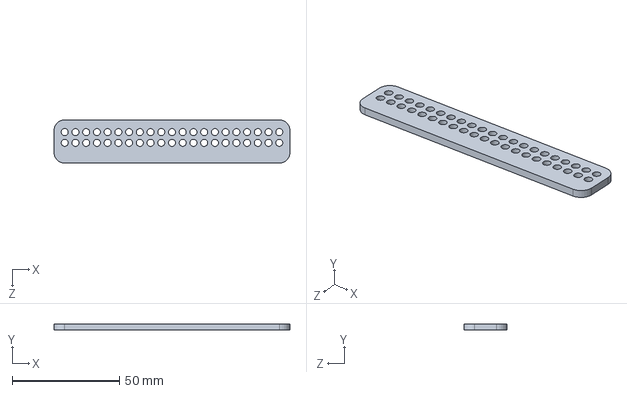
[picture p64: CAD file, 2024-09-16]
CAD/Self_designed_parts/Adaptors/FrontReinforcement.SLDPRT
110.0 x 3.00 x 20.2 mm
