wrog0003/ECE4191/CAD/Self_designed_parts/HailMary/HM_UPPERRAMPHOLDER.SLDPRT

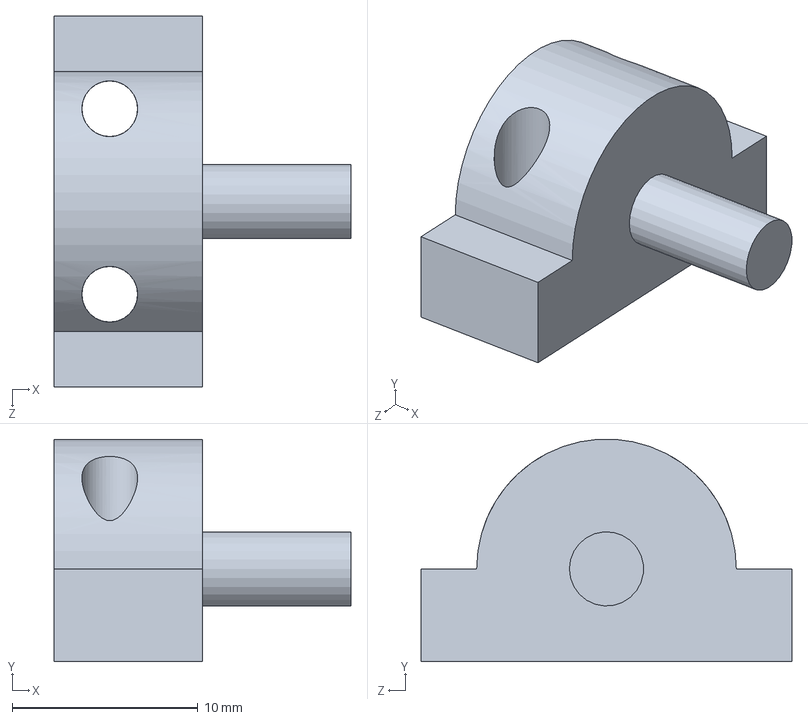
[picture p65: CAD file, 2024-10-14]
CAD/Self_designed_parts/HailMary/HM_UPPERRAMPHOLDER.SLDPRT
16.0 x 12.0 x 20.0 mm
