wrog0003/ECE4191/CAD/Self_designed_parts/L_Bracket_Chute.SLDPRT

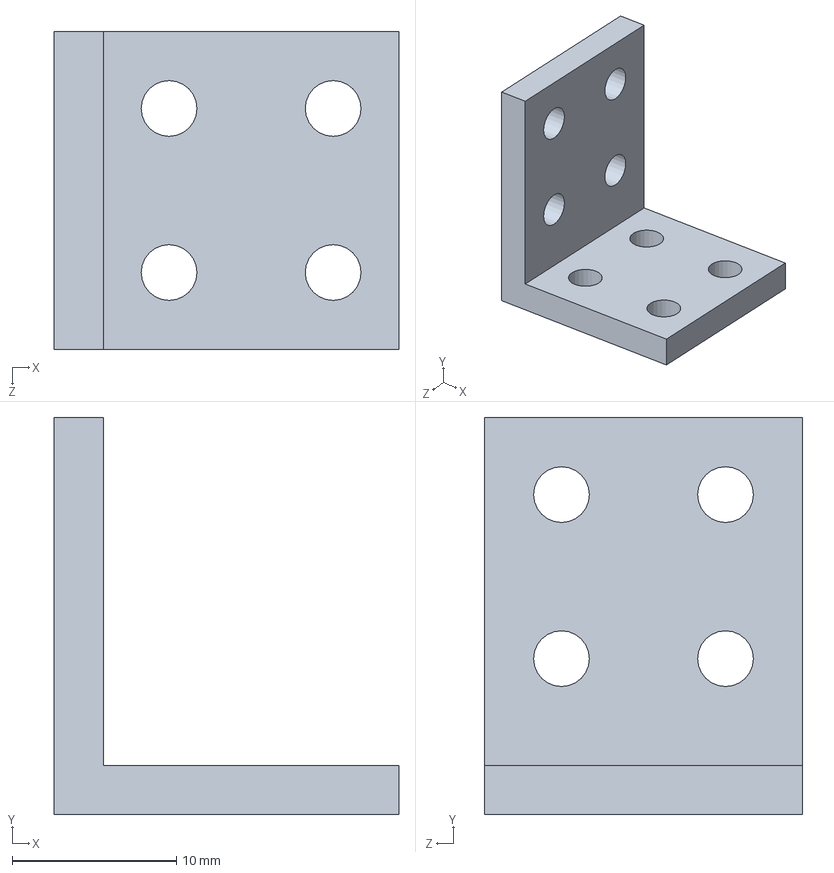
[picture p66: CAD file, 2024-10-14]
CAD/Self_designed_parts/L_Bracket_Chute.SLDPRT
21.0 x 24.2 x 19.4 mm
