wrog0003/ECE4191/CAD/Given_parts/Pin camera Mtg Plastic Logi c270.SLDPRT

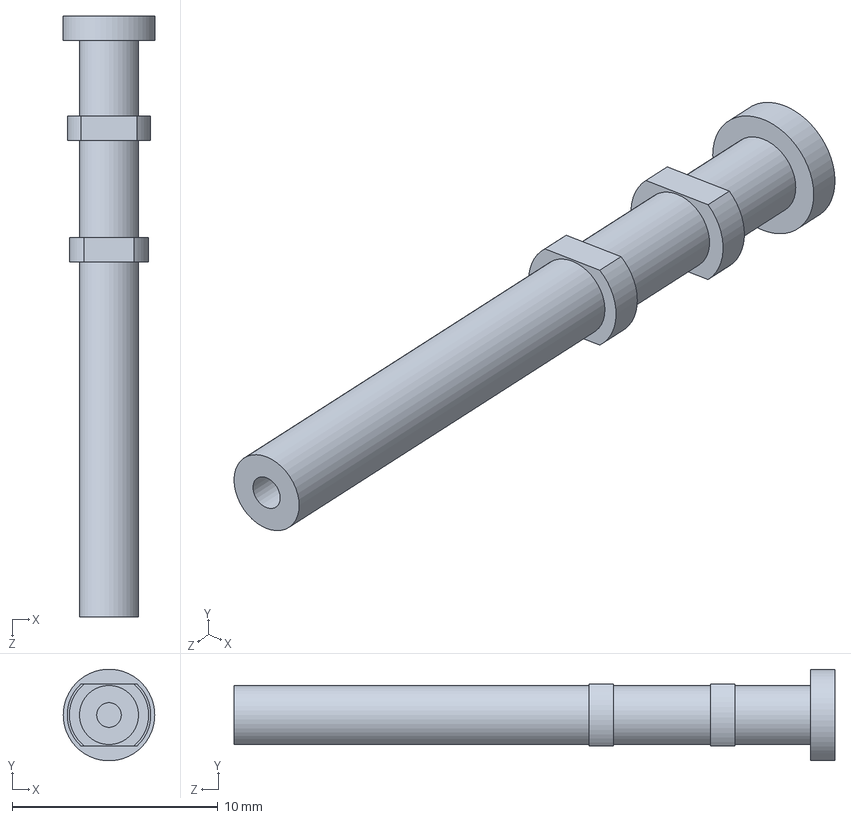
[picture p67: CAD file, 2024-09-16]
CAD/Given_parts/Pin camera Mtg Plastic Logi c270.SLDPRT
4.45 x 4.44 x 29.2 mm
