wrog0003/ECE4191/CAD/Self_designed_parts/HailMary/HM_RAMPADJUSTER.SLDPRT

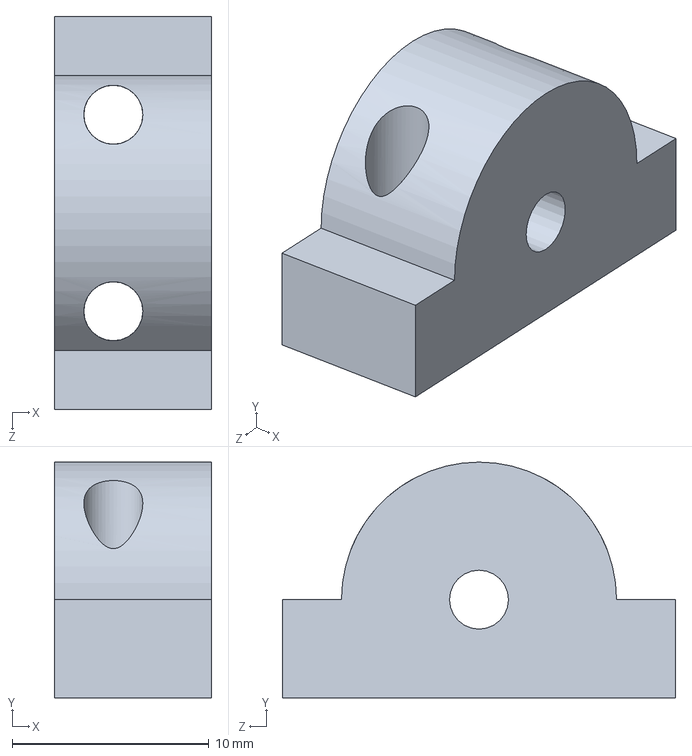
[picture p68: CAD file, 2024-10-14]
CAD/Self_designed_parts/HailMary/HM_RAMPADJUSTER.SLDPRT
8.00 x 12.0 x 20.0 mm
