wrog0003/ECE4191/CAD/Self_designed_parts/RampWheelBracket.SLDPRT

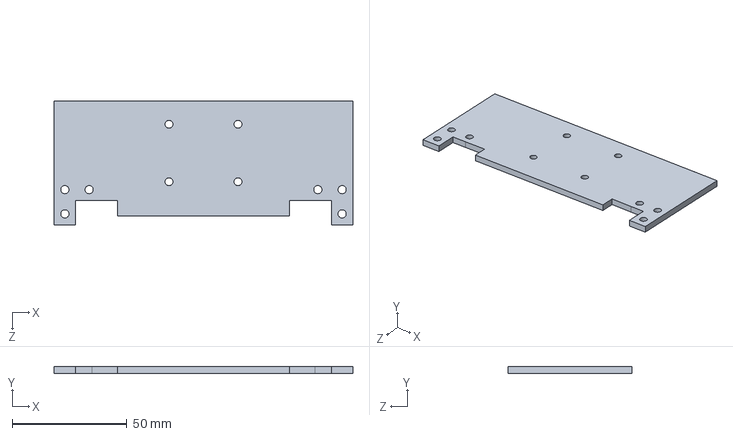
[picture p69: CAD file, 2024-10-14]
CAD/Self_designed_parts/RampWheelBracket.SLDPRT
130.0 x 3.00 x 53.7 mm
