wrog0003/ECE4191/CAD/Self_designed_parts/HailMary/HM_HUBCLAW.SLDPRT

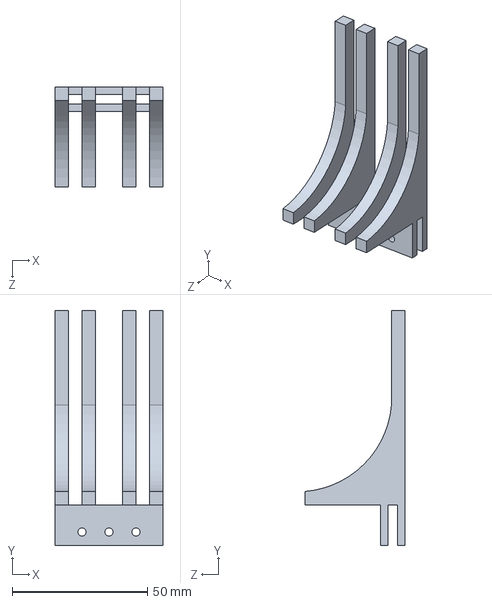
[picture p70: CAD file, 2024-10-14]
CAD/Self_designed_parts/HailMary/HM_HUBCLAW.SLDPRT
40.0 x 87.0 x 37.0 mm
