wrog0003/ECE4191/CAD/Given_parts/Baseplate.SLDPRT

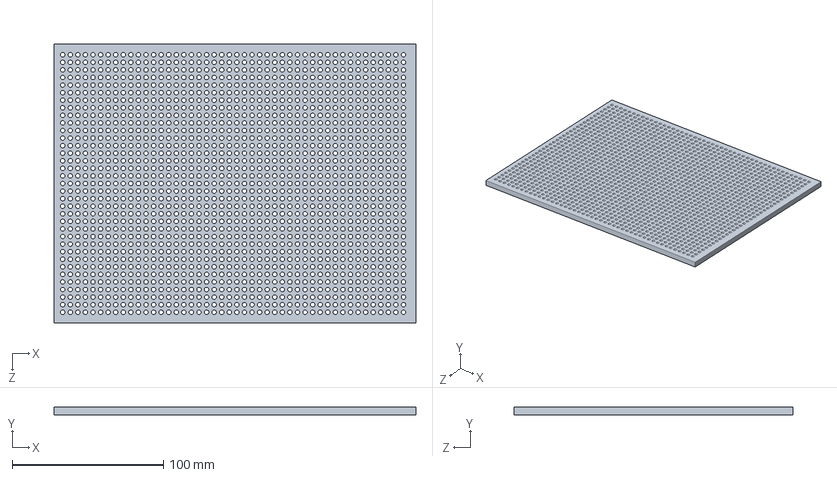
[picture p71: CAD file, 2024-08-01]
CAD/Given_parts/Baseplate.SLDPRT
239.0 x 5.00 x 184.0 mm
