wrog0003/ECE4191/CAD/Self_designed_parts/HailMary/HM_ROLLPLATE.SLDPRT

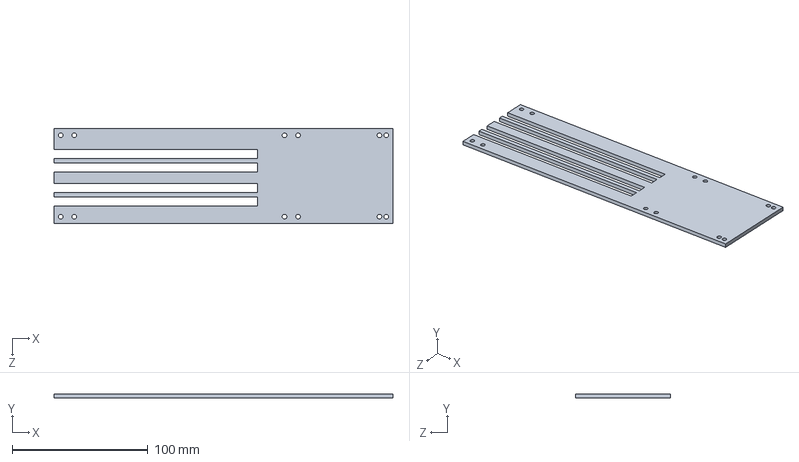
[picture p72: CAD file, 2024-10-14]
CAD/Self_designed_parts/HailMary/HM_ROLLPLATE.SLDPRT
250.0 x 3.00 x 70.0 mm
