wrog0003/ECE4191/CAD/Self_designed_parts/TrackPincher.SLDPRT

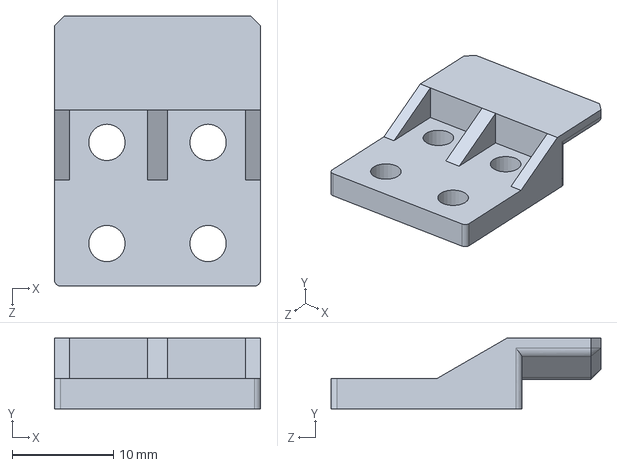
[picture p73: CAD file, 2024-10-07]
CAD/Self_designed_parts/TrackPincher.SLDPRT
20.4 x 7.00 x 26.7 mm
