wrog0003/ECE4191/CAD/Self_designed_parts/Track_Gear_NEW.SLDPRT

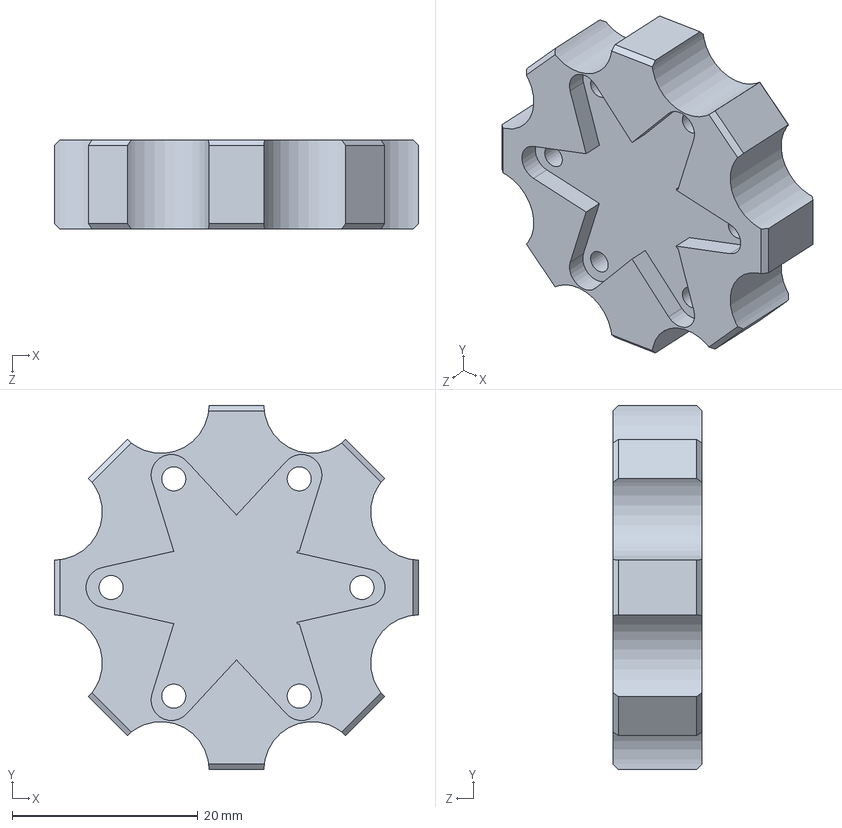
[picture p74: CAD file, 2024-10-07]
CAD/Self_designed_parts/Track_Gear_NEW.SLDPRT
39.2 x 39.2 x 9.60 mm
