wrog0003/ECE4191/CAD/Given_parts/Wheels_Secondary_Bottom.SLDPRT

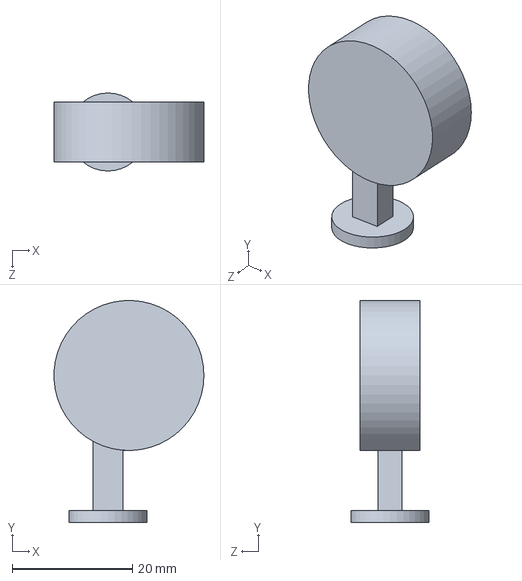
[picture p75: CAD file, 2024-08-01]
CAD/Given_parts/Wheels_Secondary_Bottom.SLDPRT
25.0 x 37.0 x 13.0 mm
