wrog0003/ECE4191/CAD/Self_designed_parts/HailMary/HM_HUBPLATE.SLDPRT

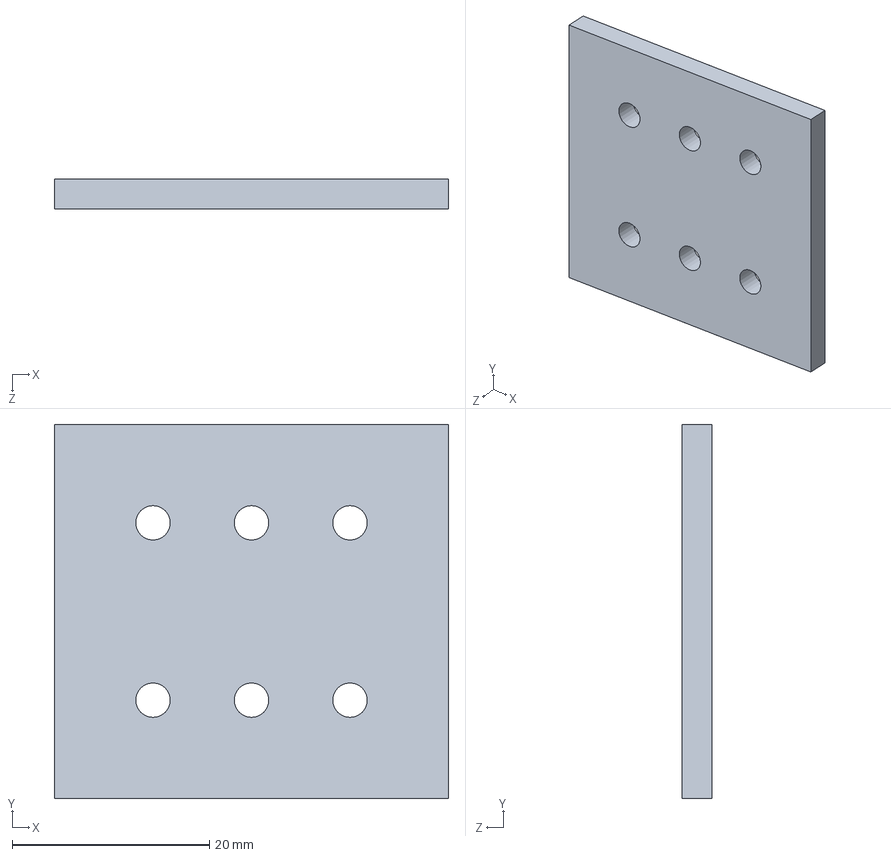
[picture p76: CAD file, 2024-10-14]
CAD/Self_designed_parts/HailMary/HM_HUBPLATE.SLDPRT
40.0 x 38.0 x 3.00 mm
