wrog0003/ECE4191/CAD/Given_parts/Wheels_Secondary_Top.SLDPRT

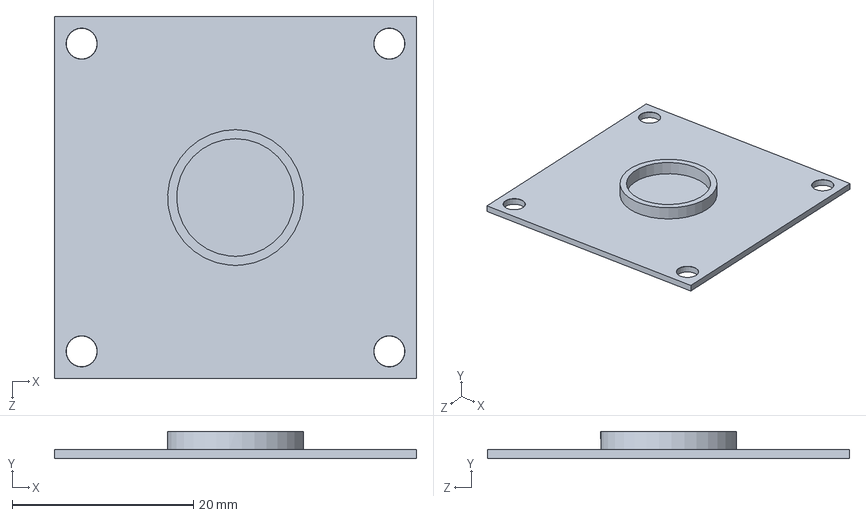
[picture p77: CAD file, 2024-08-01]
CAD/Given_parts/Wheels_Secondary_Top.SLDPRT
40.0 x 3.00 x 40.0 mm
