wrog0003/ECE4191/CAD/Self_designed_parts/HailMary/HM_HUBEND.SLDPRT

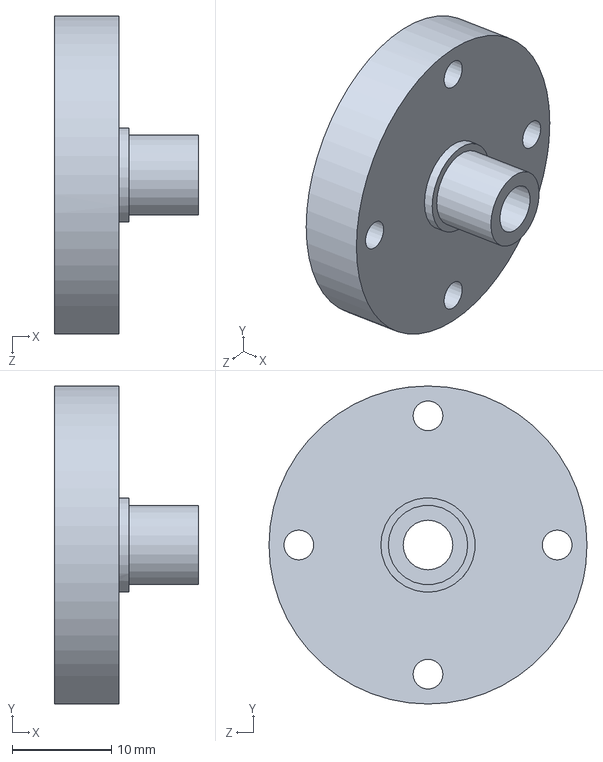
[picture p78: CAD file, 2024-10-14]
CAD/Self_designed_parts/HailMary/HM_HUBEND.SLDPRT
14.5 x 32.0 x 32.0 mm
