wrog0003/ECE4191/CAD/Self_designed_parts/RampFix.SLDPRT

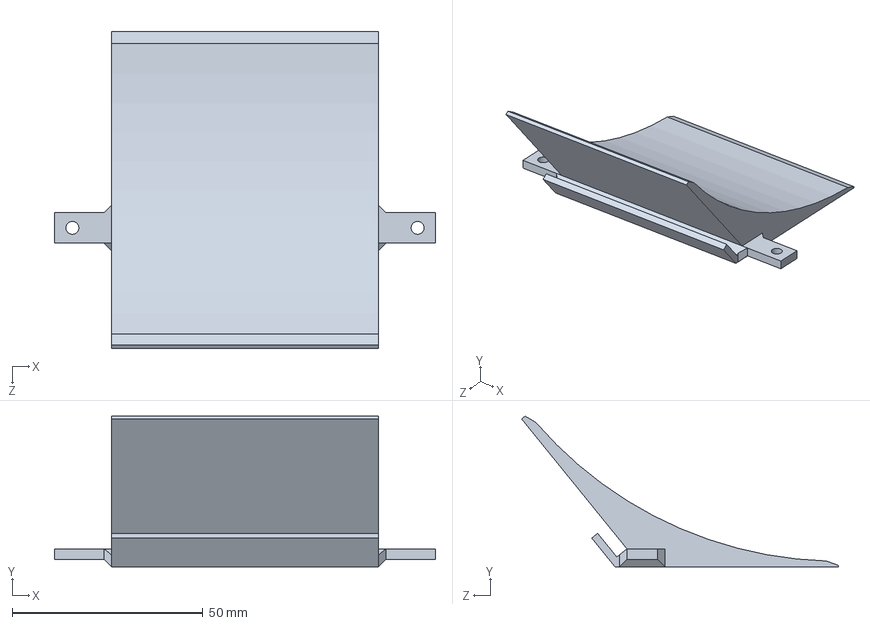
[picture p79: CAD file, 2024-10-07]
CAD/Self_designed_parts/RampFix.SLDPRT
100.0 x 39.6 x 83.1 mm
