wrog0003/ECE4191/CAD/Given_parts/RaspberryPiZeroW.SLDPRT

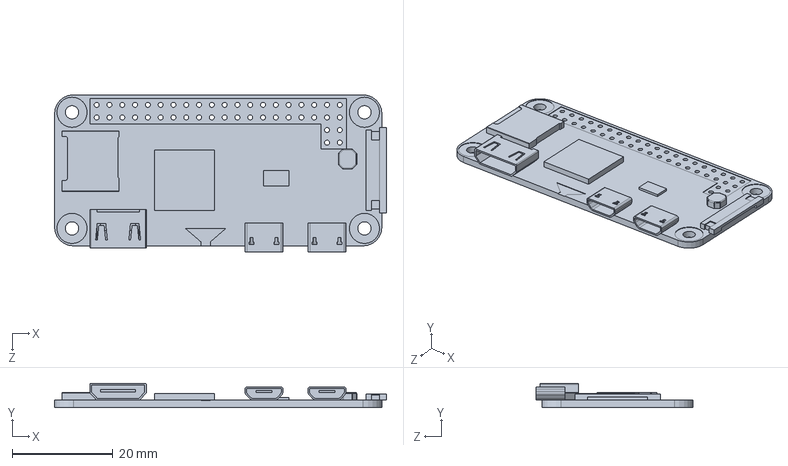
[picture p80: CAD file, 2024-07-25]
CAD/Given_parts/RaspberryPiZeroW.SLDPRT
65.9 x 4.80 x 31.2 mm
