wrog0003/ECE4191/CAD/Self_designed_parts/HailMary/HM_HUDSERVOMOUNT.SLDPRT

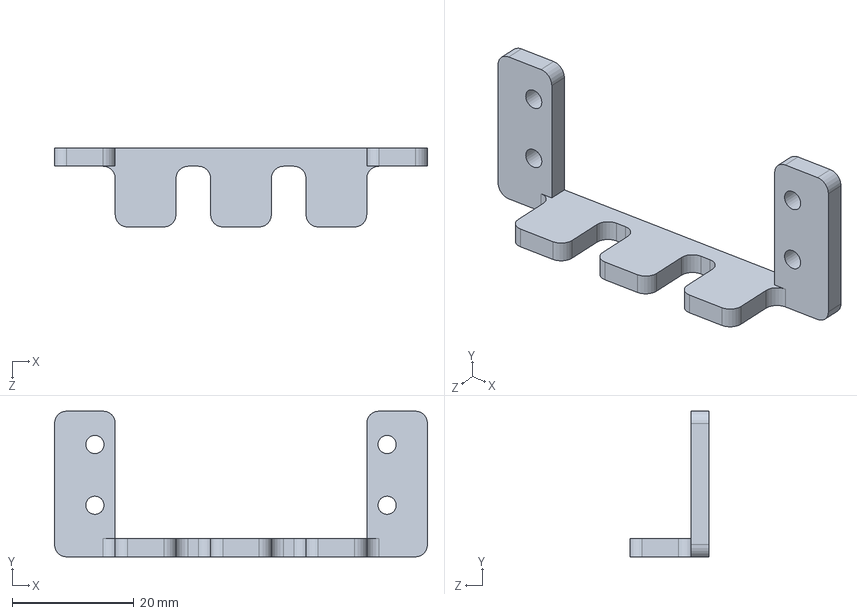
[picture p81: CAD file, 2024-10-14]
CAD/Self_designed_parts/HailMary/HM_HUDSERVOMOUNT.SLDPRT
61.4 x 24.0 x 13.0 mm
