wrog0003/ECE4191/CAD/Self_designed_parts/RampTrackChuck.SLDPRT

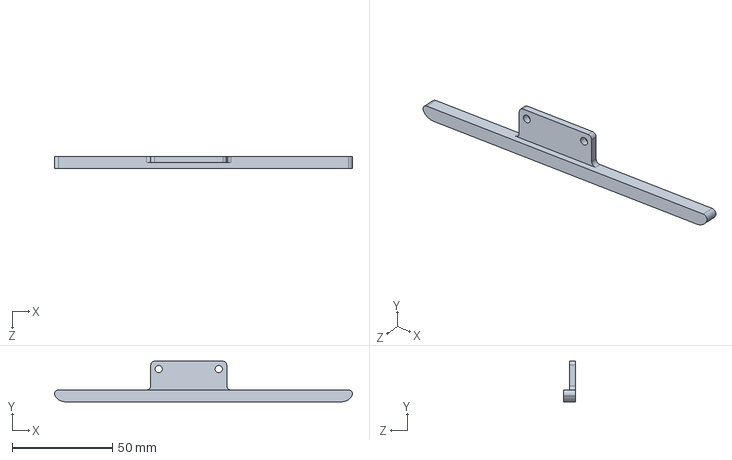
[picture p83: CAD file, 2024-10-07]
CAD/Self_designed_parts/RampTrackChuck.SLDPRT
148.9 x 20.4 x 6.00 mm
