wrog0003/ECE4191/CAD/Self_designed_parts/RampChuteSpacer.SLDPRT

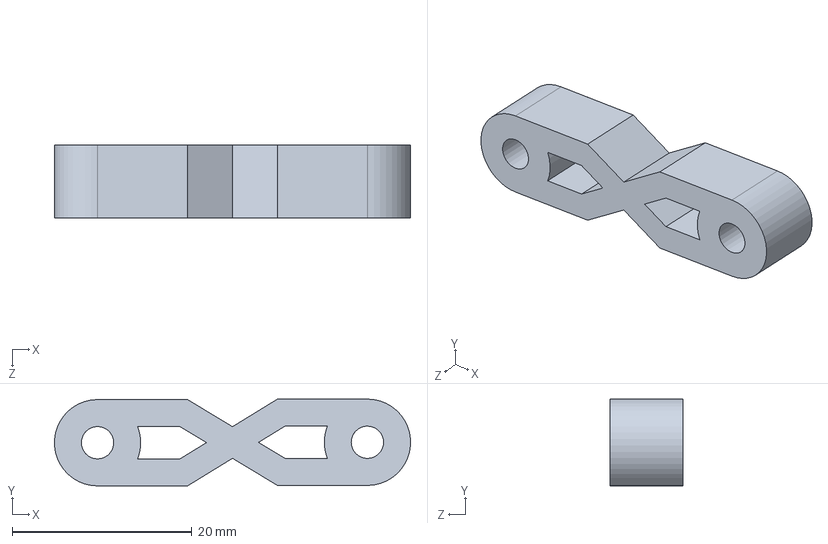
[picture p84: CAD file, 2024-10-07]
CAD/Self_designed_parts/RampChuteSpacer.SLDPRT
39.6 x 9.65 x 8.07 mm
