wrog0003/ECE4191/CAD/Self_designed_parts/HailMary/HM_RAMPEXTENTION.SLDPRT

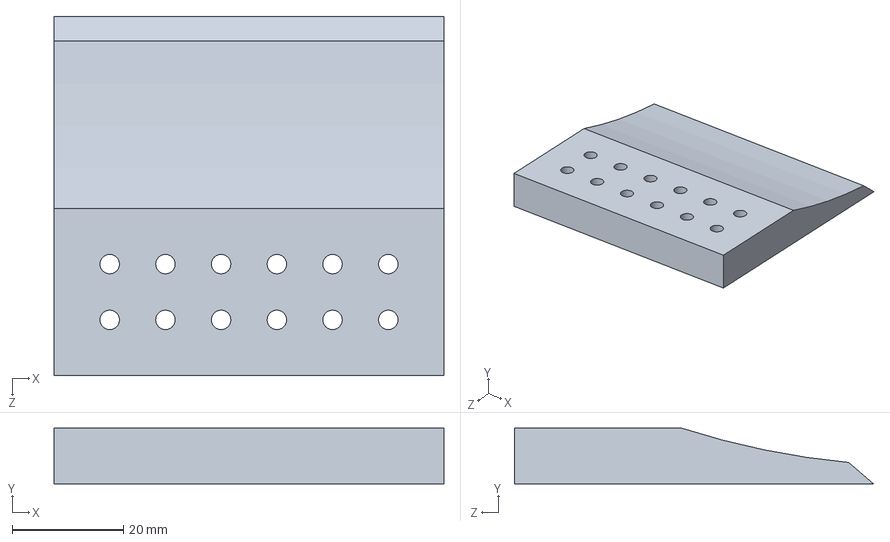
[picture p85: CAD file, 2024-10-08]
CAD/Self_designed_parts/HailMary/HM_RAMPEXTENTION.SLDPRT
70.0 x 10.0 x 64.4 mm
