wrog0003/ECE4191/CAD/Self_designed_parts/HailMary/HM_PLATEMOUNTER.SLDPRT

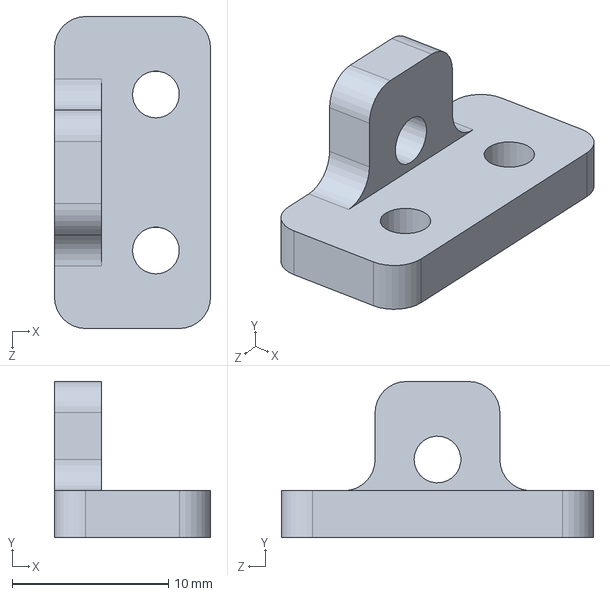
[picture p86: CAD file, 2024-10-06]
CAD/Self_designed_parts/HailMary/HM_PLATEMOUNTER.SLDPRT
10.0 x 10.0 x 20.0 mm
