wrog0003/ECE4191/CAD/Self_designed_parts/MG995 Mount.SLDPRT

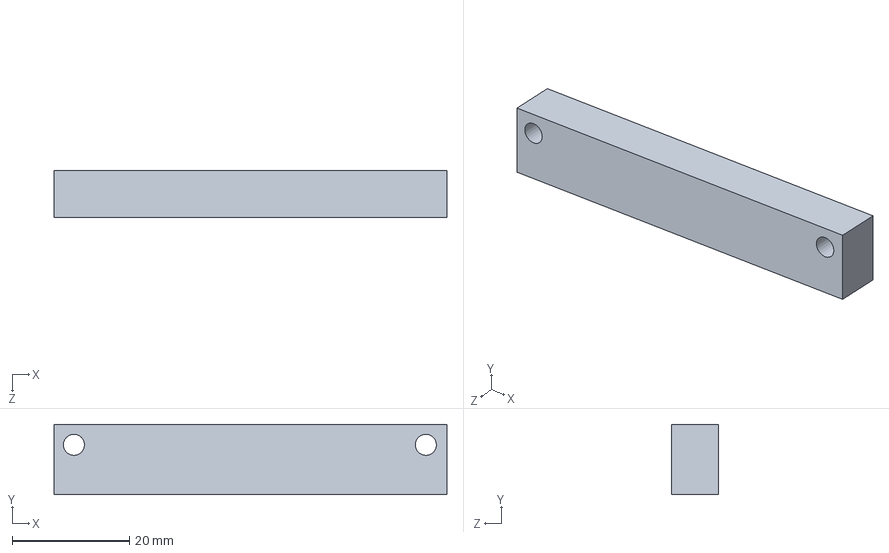
[picture p87: CAD file, 2024-10-07]
CAD/Self_designed_parts/MG995 Mount.SLDPRT
67.0 x 12.0 x 8.00 mm
