wrog0003/ECE4191/CAD/Self_designed_parts/Axle.SLDPRT

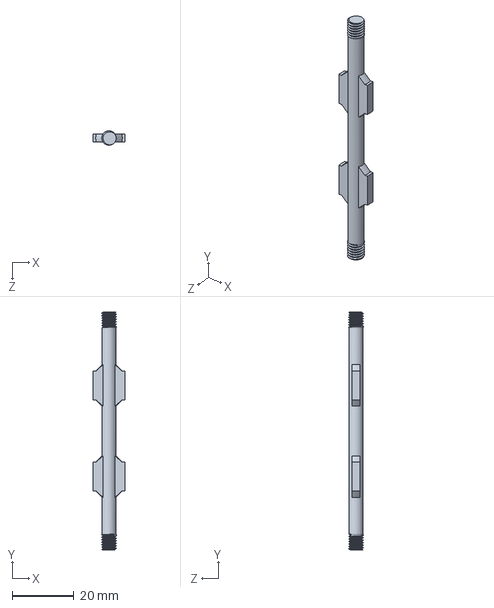
[picture p88: CAD file, 2024-10-07]
CAD/Self_designed_parts/Axle.SLDPRT
10.2 x 76.8 x 4.70 mm
