wrog0003/ECE4191/CAD/Self_designed_parts/HailMary/HM_SidePate_LEFTBACK.DXF

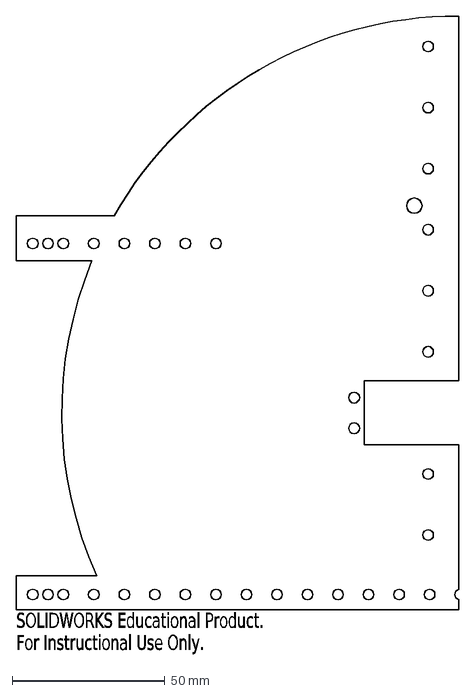
[picture p89: CAD file, 2024-10-06]
CAD/Self_designed_parts/HailMary/HM_SidePate_LEFTBACK.DXF
SOLIDWORKS Educational Product.
For Instructional Use Only.
