wrog0003/ECE4191/CAD/Self_designed_parts/HorizontalGearSpacer.SLDPRT

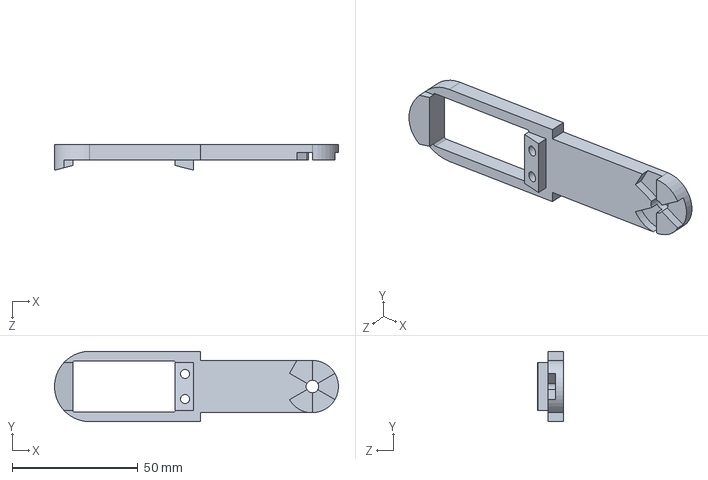
[picture p91: CAD file, 2024-10-07]
CAD/Self_designed_parts/HorizontalGearSpacer.SLDPRT
113.0 x 28.0 x 10.1 mm
