wrog0003/ECE4191/CAD/Self_designed_parts/HailMary/HM_SidePateRIGHTBACK.DXF

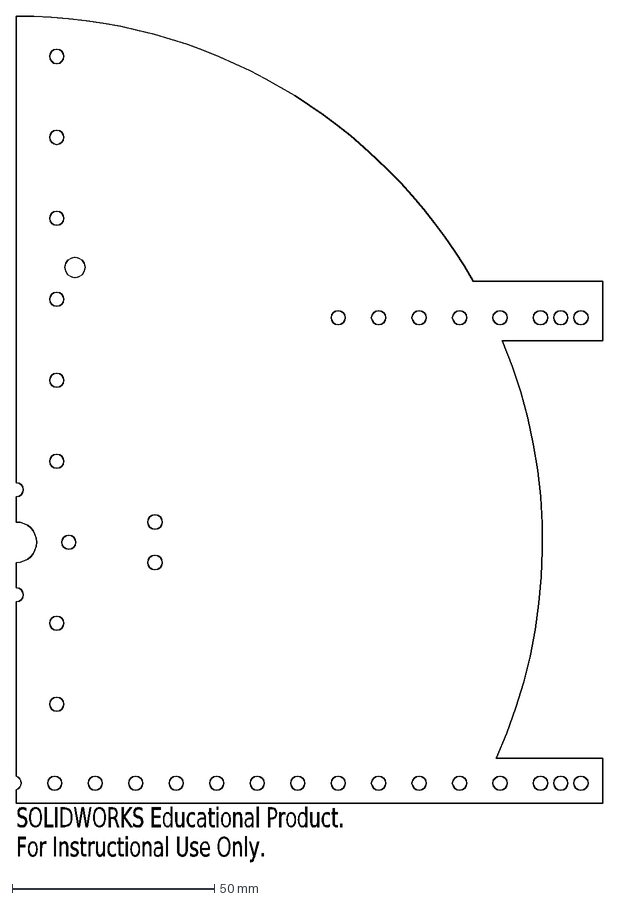
[picture p92: CAD file, 2024-10-06]
CAD/Self_designed_parts/HailMary/HM_SidePateRIGHTBACK.DXF
SOLIDWORKS Educational Product.
For Instructional Use Only.
