wrog0003/ECE4191/CAD/Self_designed_parts/MG995 Clamp.SLDPRT

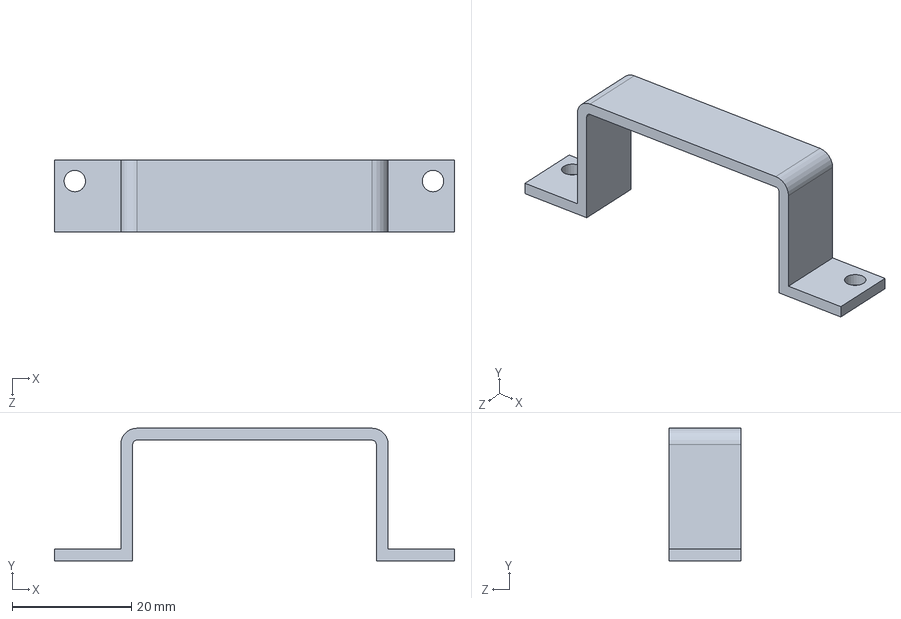
[picture p93: CAD file, 2024-10-07]
CAD/Self_designed_parts/MG995 Clamp.SLDPRT
67.0 x 22.2 x 12.0 mm
