wrog0003/ECE4191/CAD/Self_designed_parts/TensionGear.SLDPRT

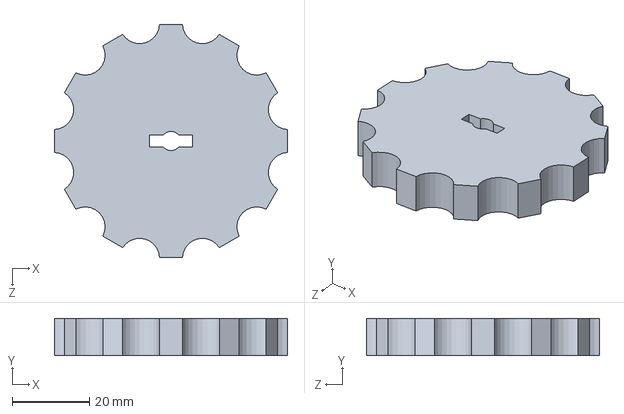
[picture p95: CAD file, 2024-10-07]
CAD/Self_designed_parts/TensionGear.SLDPRT
60.2 x 9.60 x 60.2 mm
