wrog0003/ECE4191/CAD/Self_designed_parts/HailMary/HM_CONNECTOR.SLDPRT

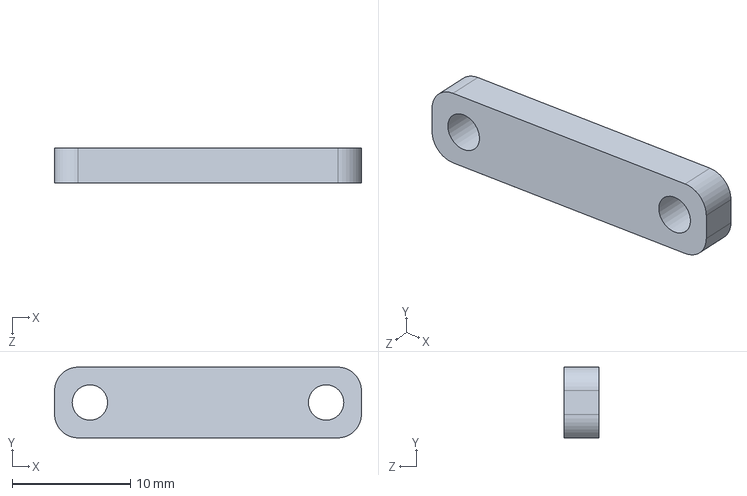
[picture p96: CAD file, 2024-10-06]
CAD/Self_designed_parts/HailMary/HM_CONNECTOR.SLDPRT
26.0 x 6.00 x 3.00 mm
