wrog0003/ECE4191/CAD/Self_designed_parts/Track_Gear_NEW_[Servo].SLDPRT

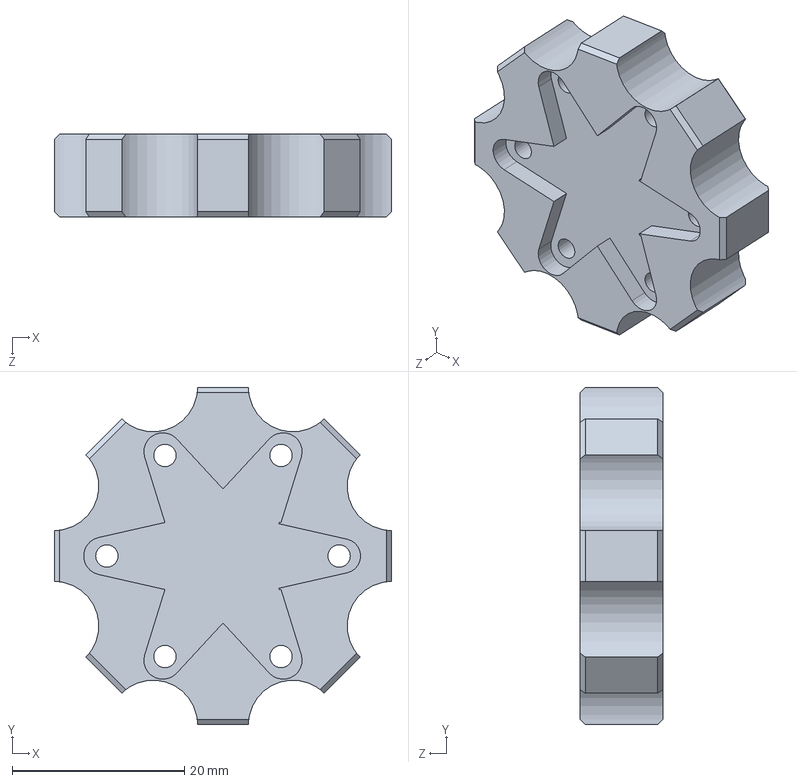
[picture p97: CAD file, 2024-10-06]
CAD/Self_designed_parts/Track_Gear_NEW_[Servo].SLDPRT
39.2 x 39.2 x 9.60 mm
