wrog0003/ECE4191/CAD/Self_designed_parts/GearMountSpacer.SLDPRT

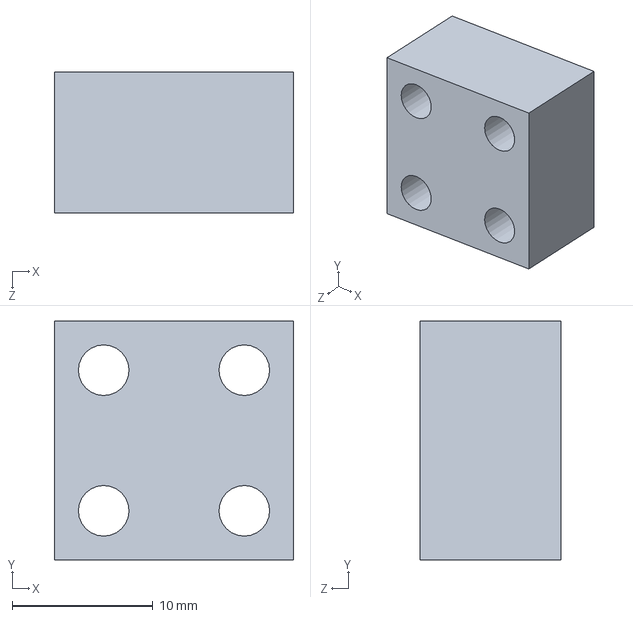
[picture p98: CAD file, 2024-10-04]
CAD/Self_designed_parts/GearMountSpacer.SLDPRT
17.0 x 17.0 x 10.0 mm
