wrog0003/ECE4191/CAD/Self_designed_parts/HailMary/HM_HUB.SLDPRT

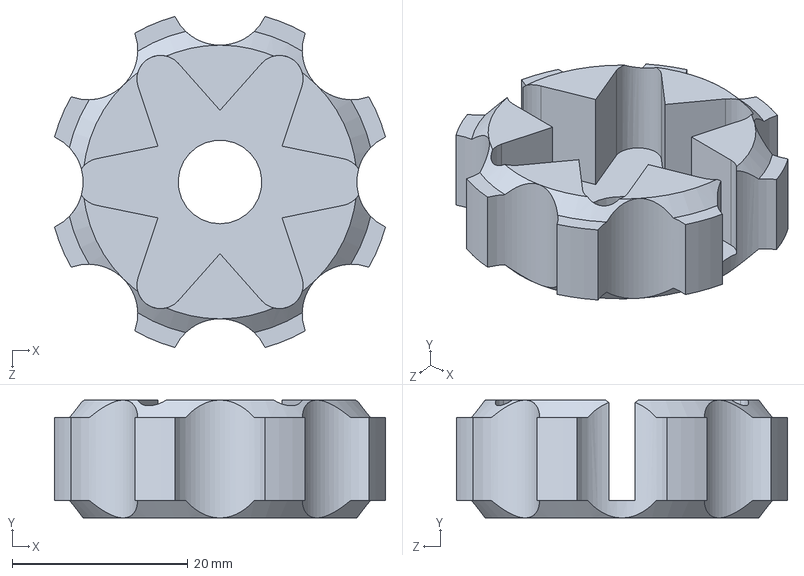
[picture p99: CAD file, 2024-10-05]
CAD/Self_designed_parts/HailMary/HM_HUB.SLDPRT
37.6 x 13.4 x 37.6 mm
