wrog0003/ECE4191/CAD/Self_designed_parts/RampChute.SLDPRT

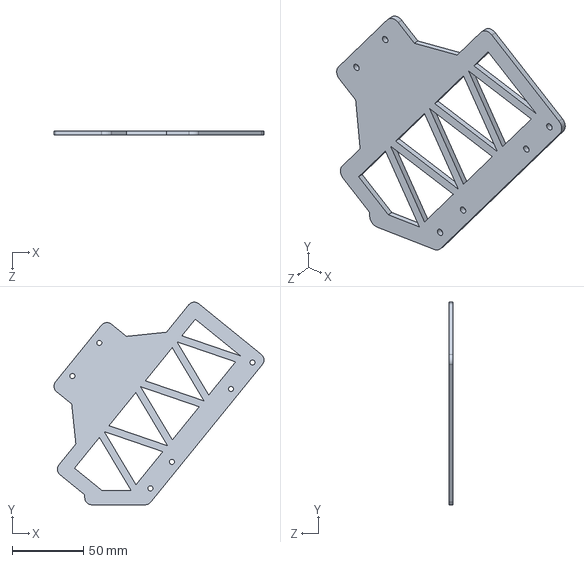
[picture p100: CAD file, 2024-10-04]
CAD/Self_designed_parts/RampChute.SLDPRT
147.7 x 142.6 x 3.00 mm
