wrog0003/ECE4191/CAD/Self_designed_parts/RampChuteBracket.SLDPRT

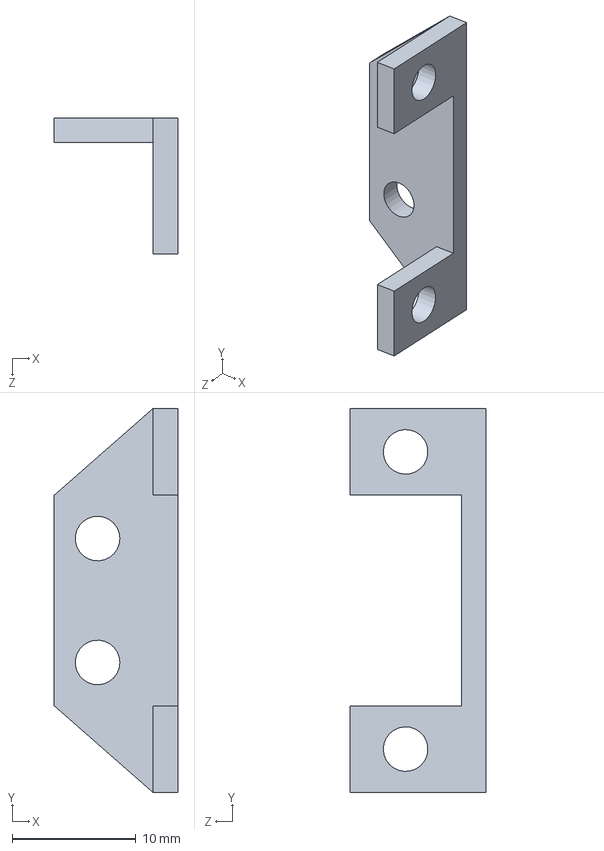
[picture p101: CAD file, 2024-10-04]
CAD/Self_designed_parts/RampChuteBracket.SLDPRT
9.97 x 31.0 x 11.0 mm
