wrog0003/ECE4191/CAD/Self_designed_parts/Track_Gear.SLDPRT

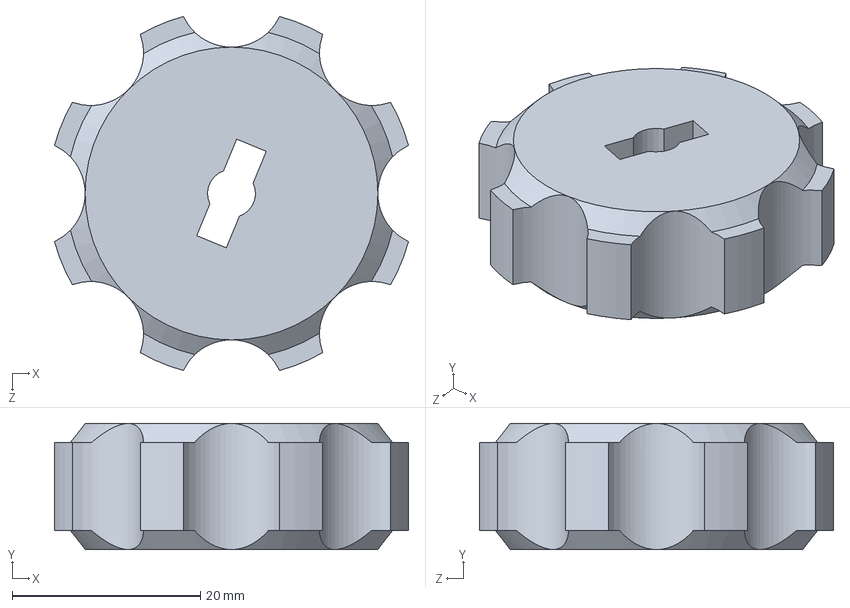
[picture p102: CAD file, 2024-10-04]
CAD/Self_designed_parts/Track_Gear.SLDPRT
37.6 x 13.4 x 37.6 mm
