wrog0003/ECE4191/CAD/Self_designed_parts/DiagonalGearSpacer.SLDPRT

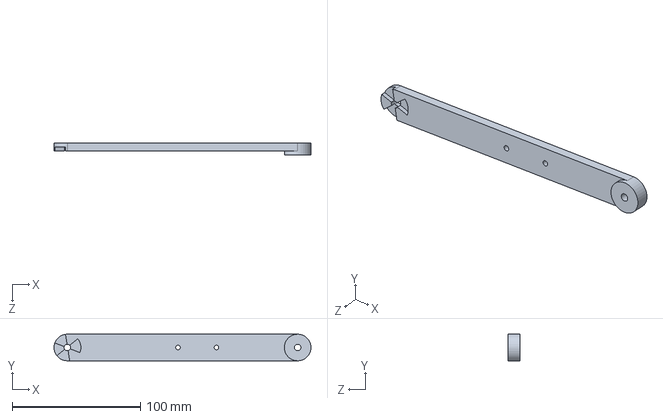
[picture p103: CAD file, 2024-10-04]
CAD/Self_designed_parts/DiagonalGearSpacer.SLDPRT
200.5 x 20.8 x 9.00 mm
