wrog0003/ECE4191/CAD/Self_designed_parts/RampFix_Bracket.SLDPRT

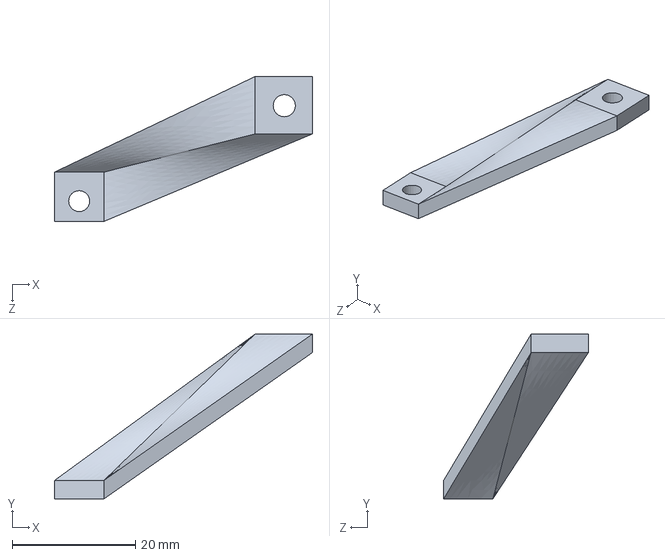
[picture p104: CAD file, 2024-10-04]
CAD/Self_designed_parts/RampFix_Bracket.SLDPRT
41.8 x 26.8 x 23.5 mm
