wrog0003/ECE4191/CAD/Self_designed_parts/GearMount_Servo.SLDPRT

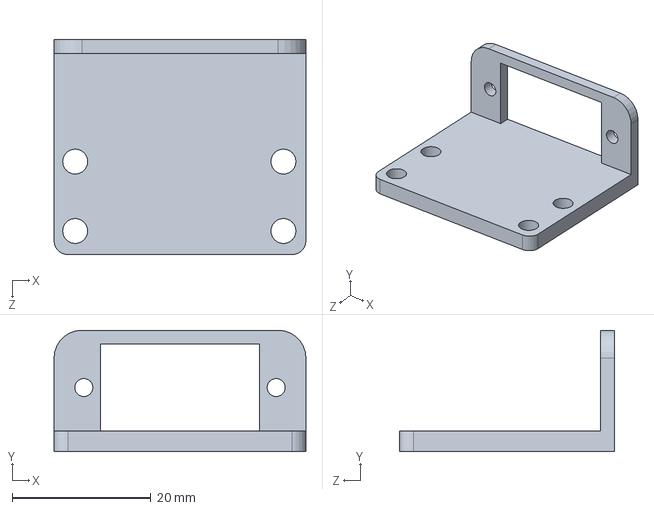
[picture p105: CAD file, 2024-10-03]
CAD/Self_designed_parts/GearMount_Servo.SLDPRT
36.3 x 17.5 x 31.0 mm
