wrog0003/ECE4191/CAD/Self_designed_parts/GearMount_ServoSpacer.SLDPRT

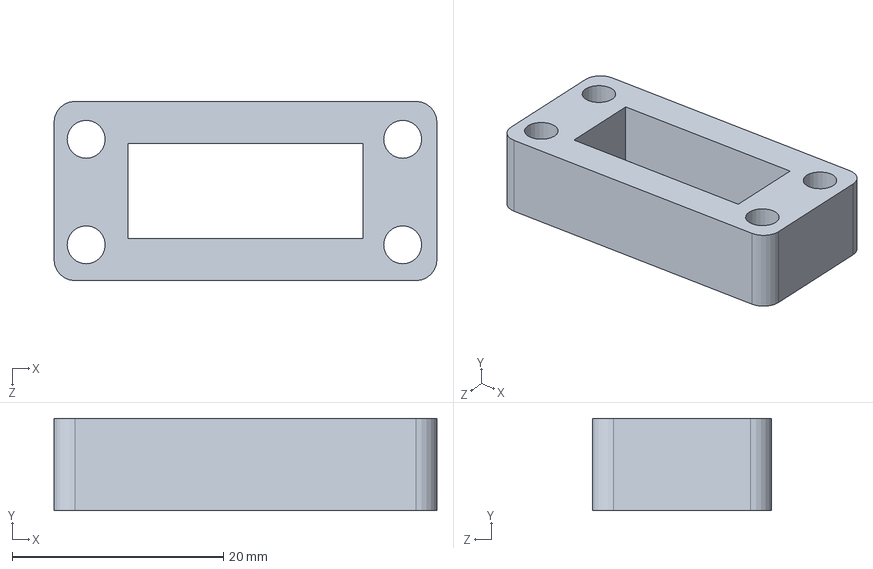
[picture p106: CAD file, 2024-10-03]
CAD/Self_designed_parts/GearMount_ServoSpacer.SLDPRT
36.3 x 8.75 x 17.0 mm
