wrog0003/ECE4191/CAD/Self_designed_parts/Track_TensionArm1.SLDPRT

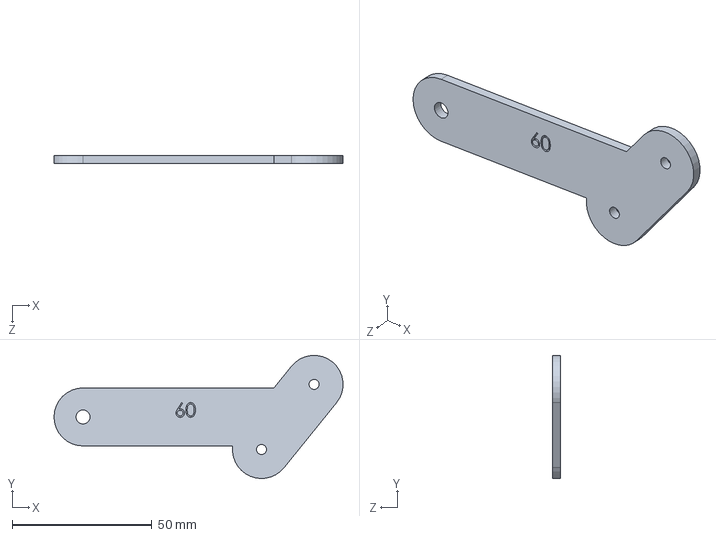
[picture p107: CAD file, 2024-10-03]
CAD/Self_designed_parts/Track_TensionArm1.SLDPRT
103.6 x 44.1 x 3.00 mm
