wrog0003/ECE4191/CAD/Self_designed_parts/SG90C Gear Cap.SLDPRT

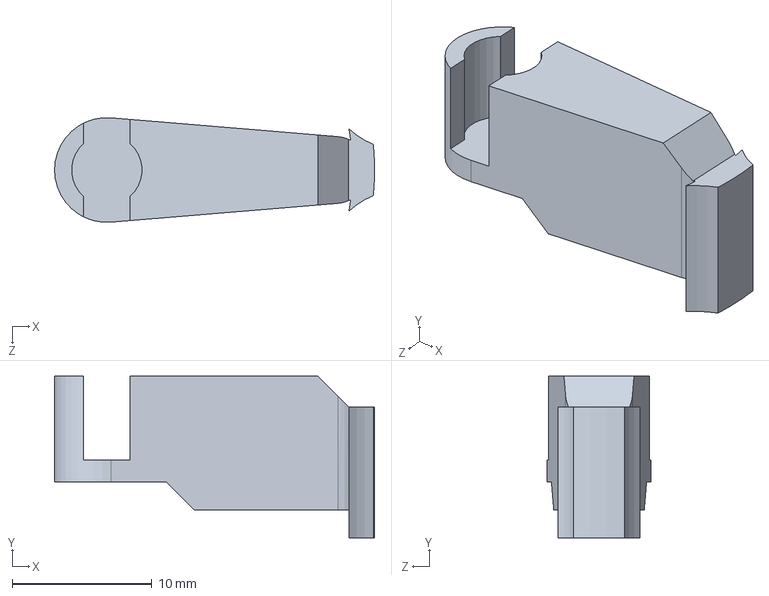
[picture p108: CAD file, 2024-09-30]
CAD/Self_designed_parts/SG90C Gear Cap.SLDPRT
22.9 x 11.6 x 7.47 mm
