wrog0003/ECE4191/CAD/Self_designed_parts/MG995 Gear Cap.SLDPRT

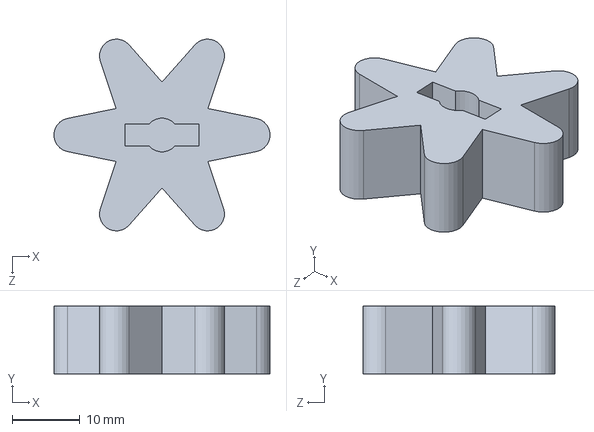
[picture p109: CAD file, 2024-09-30]
CAD/Self_designed_parts/MG995 Gear Cap.SLDPRT
32.0 x 10.0 x 28.4 mm
