wrog0003/ECE4191/CAD/Self_designed_parts/Ramp.SLDPRT

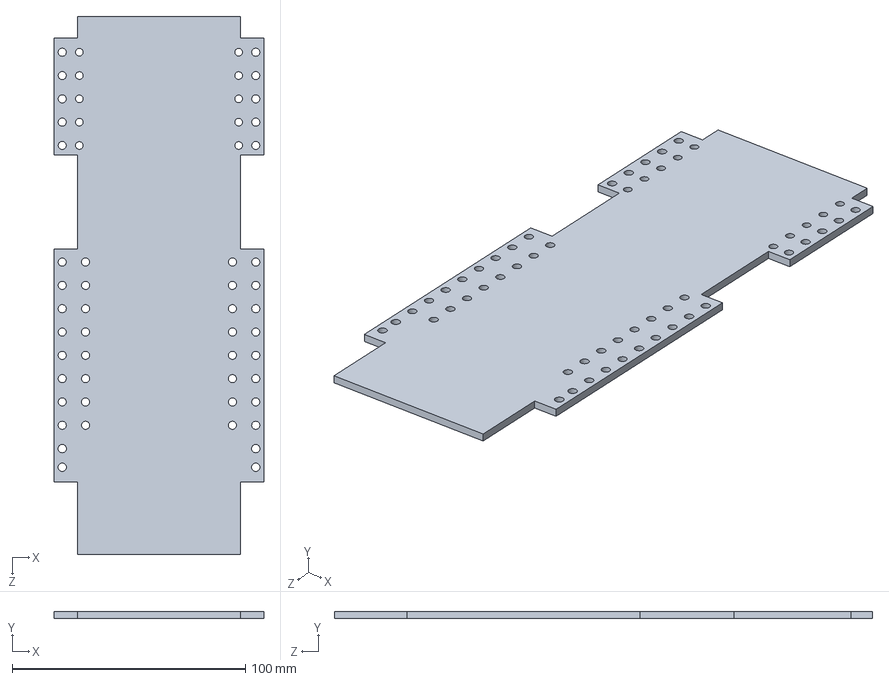
[picture p110: CAD file, 2024-09-30]
CAD/Self_designed_parts/Ramp.SLDPRT
90.0 x 3.00 x 230.7 mm
