wrog0003/ECE4191/CAD/Self_designed_parts/Track_Gear_Servo_Cap.SLDPRT

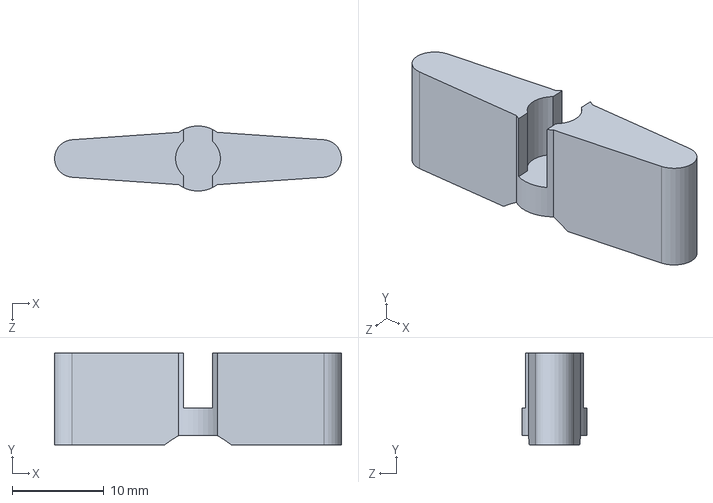
[picture p111: CAD file, 2024-09-18]
CAD/Self_designed_parts/Track_Gear_Servo_Cap.SLDPRT
31.3 x 10.0 x 7.10 mm
