wrog0003/ECE4191/CAD/Self_designed_parts/DriveShaft_Cap.SLDPRT

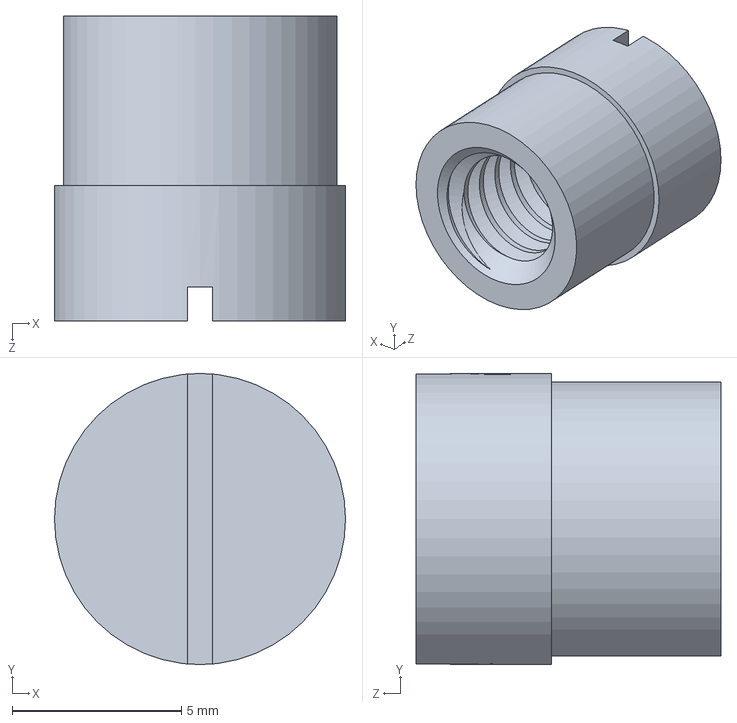
[picture p112: CAD file, 2024-09-18]
CAD/Self_designed_parts/DriveShaft_Cap.SLDPRT
8.60 x 8.60 x 9.00 mm
