wrog0003/ECE4191/CAD/Self_designed_parts/GearMount.SLDPRT

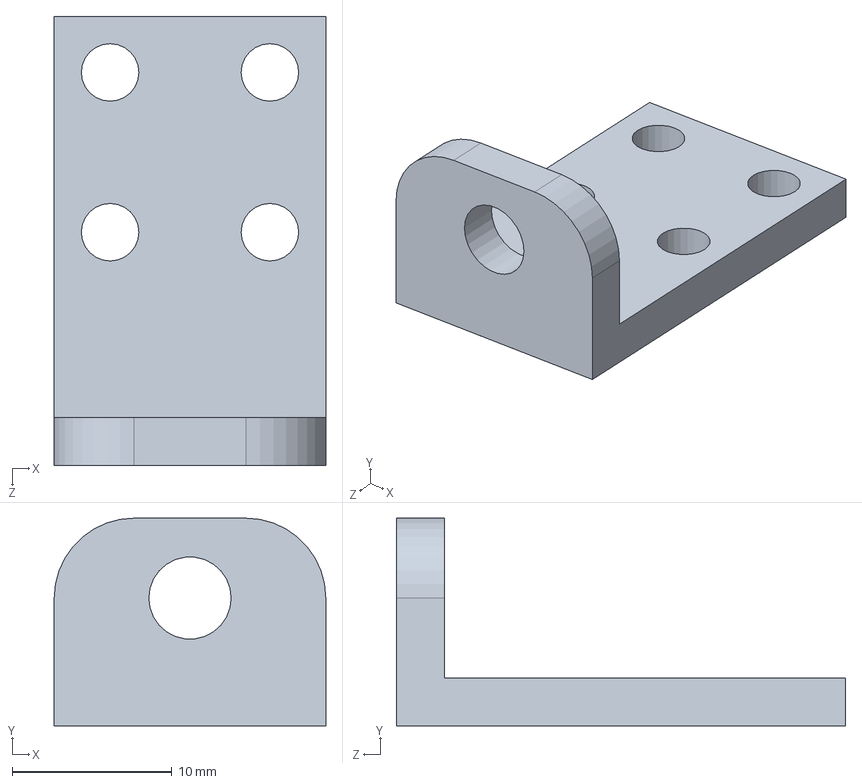
[picture p113: CAD file, 2024-09-18]
CAD/Self_designed_parts/GearMount.SLDPRT
17.0 x 13.0 x 28.1 mm
