wrog0003/ECE4191/CAD/Self_designed_parts/Test_Shaft_Slave.SLDPRT

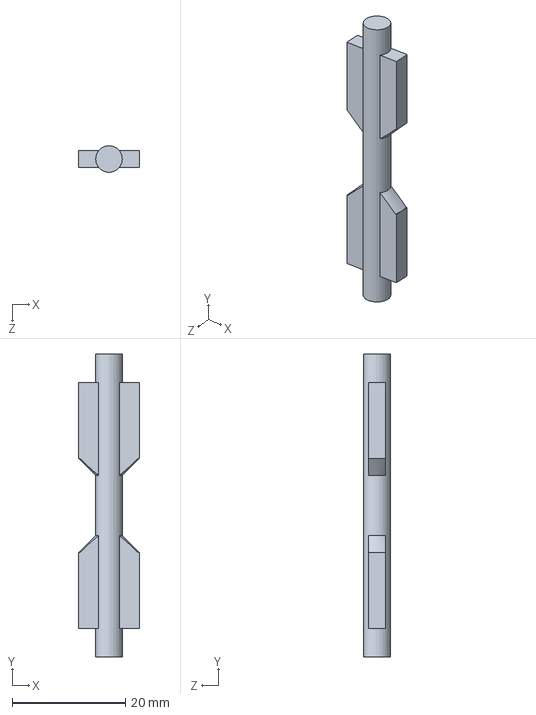
[picture p114: CAD file, 2024-09-16]
CAD/Self_designed_parts/Test_Shaft_Slave.SLDPRT
10.7 x 53.4 x 4.70 mm
