wrog0003/ECE4191/CAD/Self_designed_parts/Pusher_Flap.SLDPRT

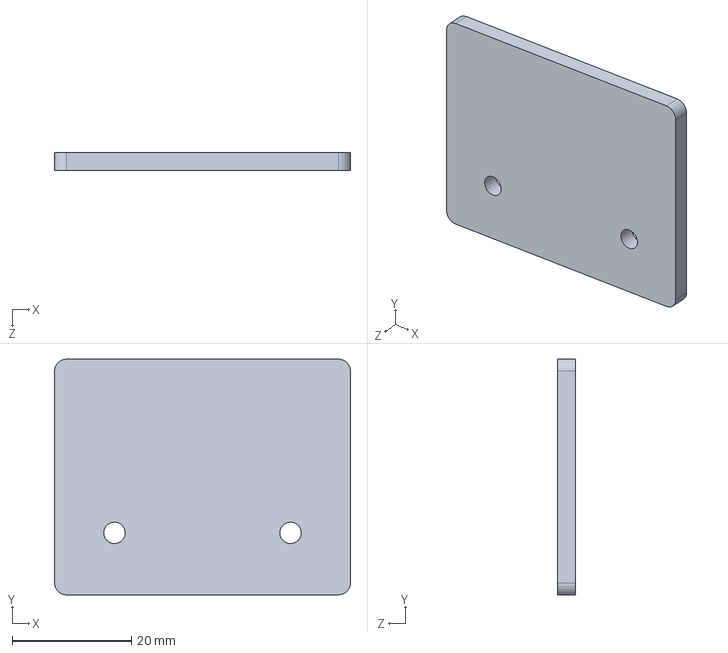
[picture p115: CAD file, 2024-09-16]
CAD/Self_designed_parts/Pusher_Flap.SLDPRT
49.6 x 39.5 x 3.00 mm
