wrog0003/ECE4191/CAD/Self_designed_parts/TestStand.SLDPRT

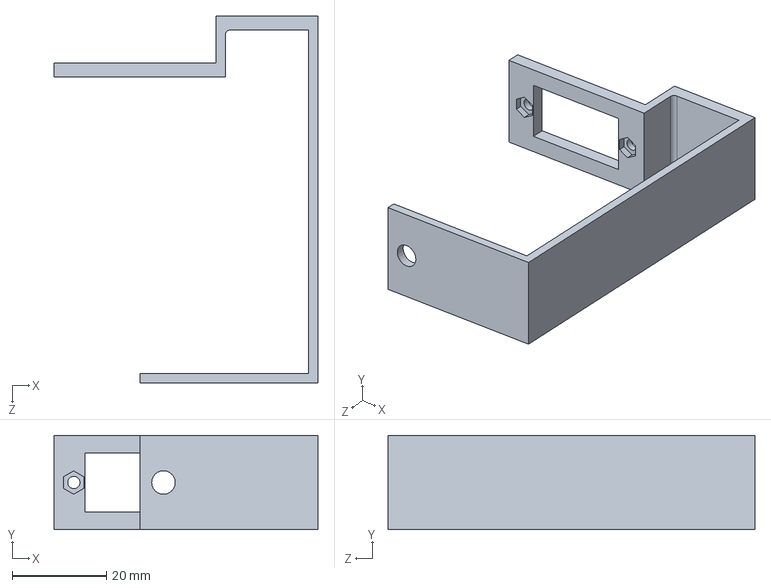
[picture p116: CAD file, 2024-09-16]
CAD/Self_designed_parts/TestStand.SLDPRT
56.1 x 20.0 x 78.0 mm
