wrog0003/ECE4191/CAD/Self_designed_parts/Pusher_Base_DualBase.SLDPRT

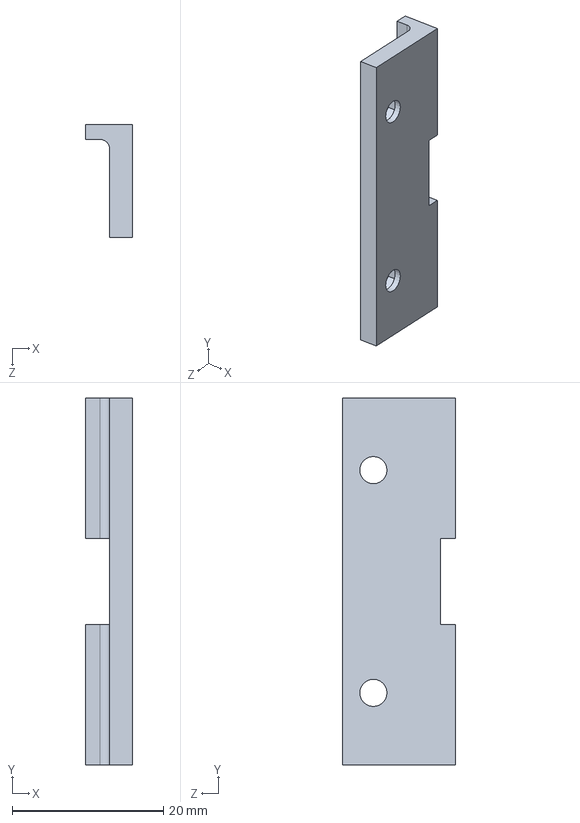
[picture p117: CAD file, 2024-09-16]
CAD/Self_designed_parts/Pusher_Base_DualBase.SLDPRT
6.17 x 48.6 x 15.0 mm
