wrog0003/ECE4191/CAD/Self_designed_parts/Pusher_Base_TriStand.SLDPRT

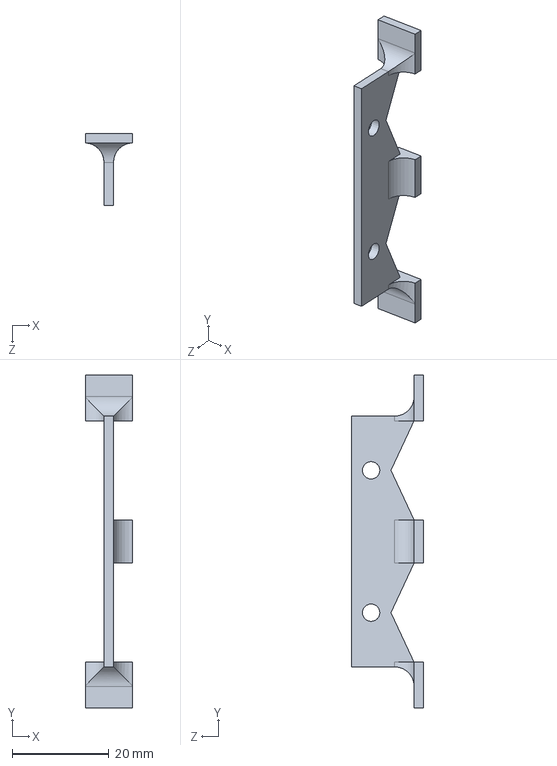
[picture p118: CAD file, 2024-09-16]
CAD/Self_designed_parts/Pusher_Base_TriStand.SLDPRT
9.73 x 69.0 x 15.0 mm
