wrog0003/ECE4191/CAD/Self_designed_parts/Wheel_100mm.SLDPRT

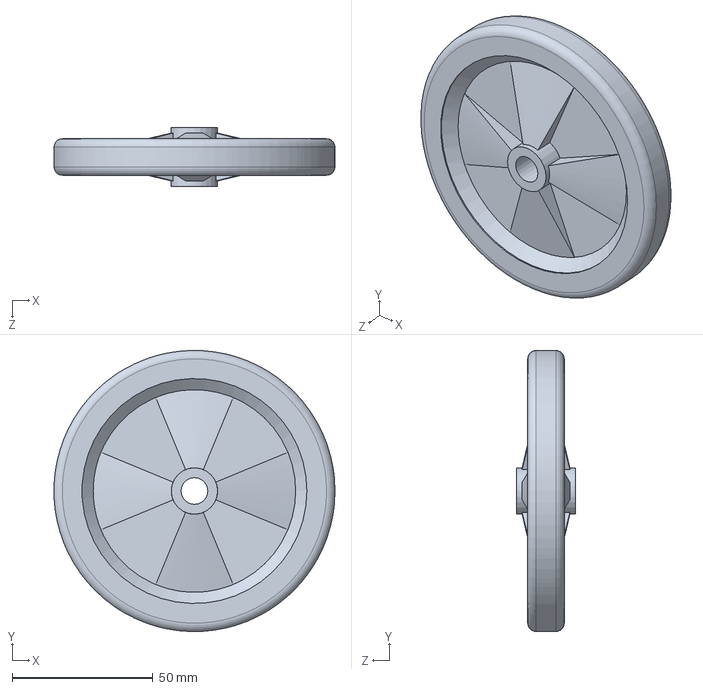
[picture p119: CAD file, 2024-09-16]
CAD/Self_designed_parts/Wheel_100mm.SLDPRT
100.0 x 100.0 x 21.0 mm
