wrog0003/ECE4191/CAD/Self_designed_parts/ServoMountSpacer.SLDPRT

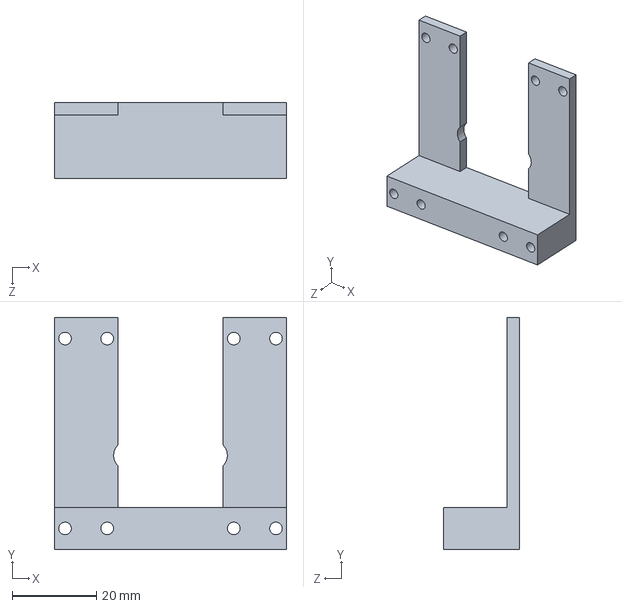
[picture p120: CAD file, 2024-09-16]
CAD/Self_designed_parts/ServoMountSpacer.SLDPRT
55.0 x 55.0 x 18.0 mm
