wrog0003/ECE4191/CAD/Self_designed_parts/AngledRampBracket_Left.SLDPRT

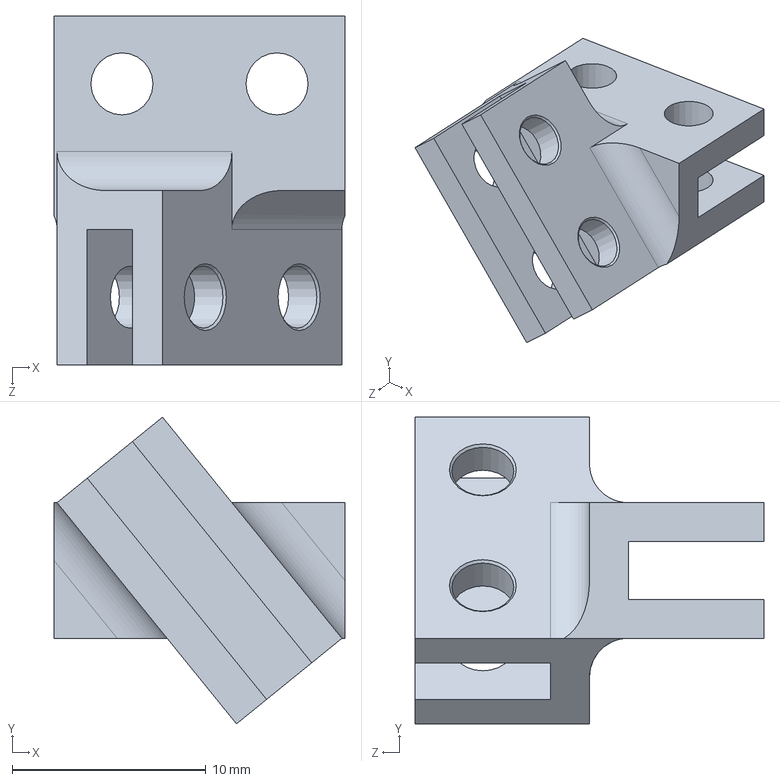
[picture p121: CAD file, 2024-09-16]
CAD/Self_designed_parts/AngledRampBracket_Left.SLDPRT
15.0 x 15.8 x 18.0 mm
