wrog0003/ECE4191/CAD/Self_designed_parts/Track_2.2_70mm_Pusher.SLDPRT

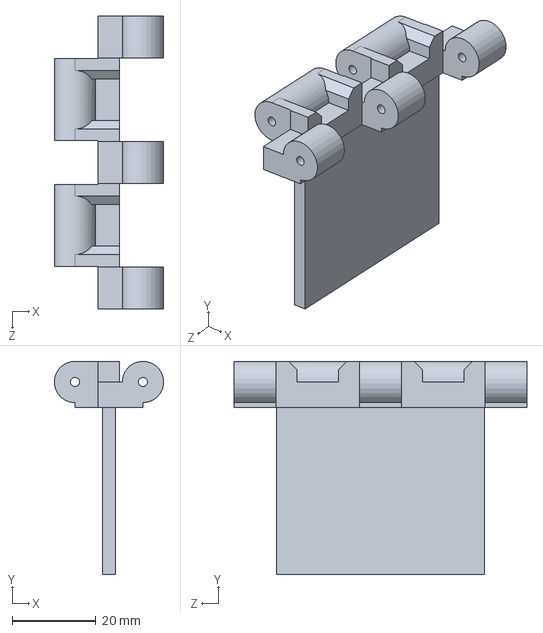
[picture p122: CAD file, 2024-09-16]
CAD/Self_designed_parts/Track_2.2_70mm_Pusher.SLDPRT
26.1 x 51.0 x 70.0 mm
