wrog0003/ECE4191/CAD/Self_designed_parts/Track_2.2_70mm.SLDPRT

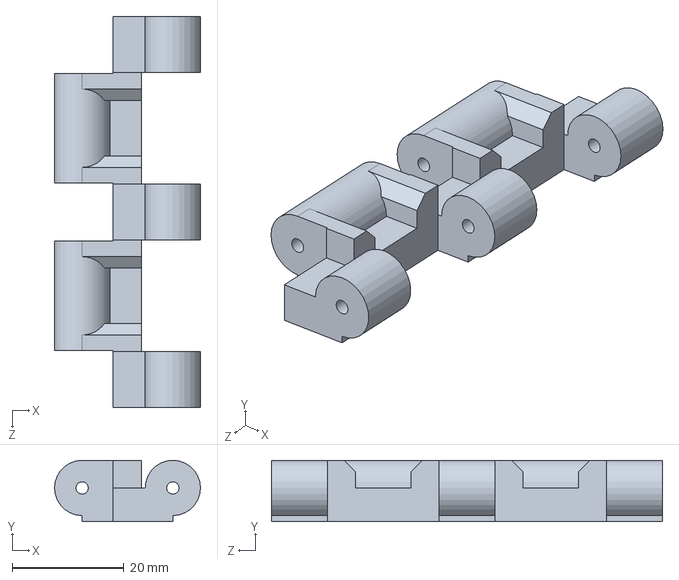
[picture p123: CAD file, 2024-09-04]
CAD/Self_designed_parts/Track_2.2_70mm.SLDPRT
26.1 x 11.0 x 70.0 mm
