wrog0003/ECE4191/CAD/Self_designed_parts/ClawRight.SLDPRT

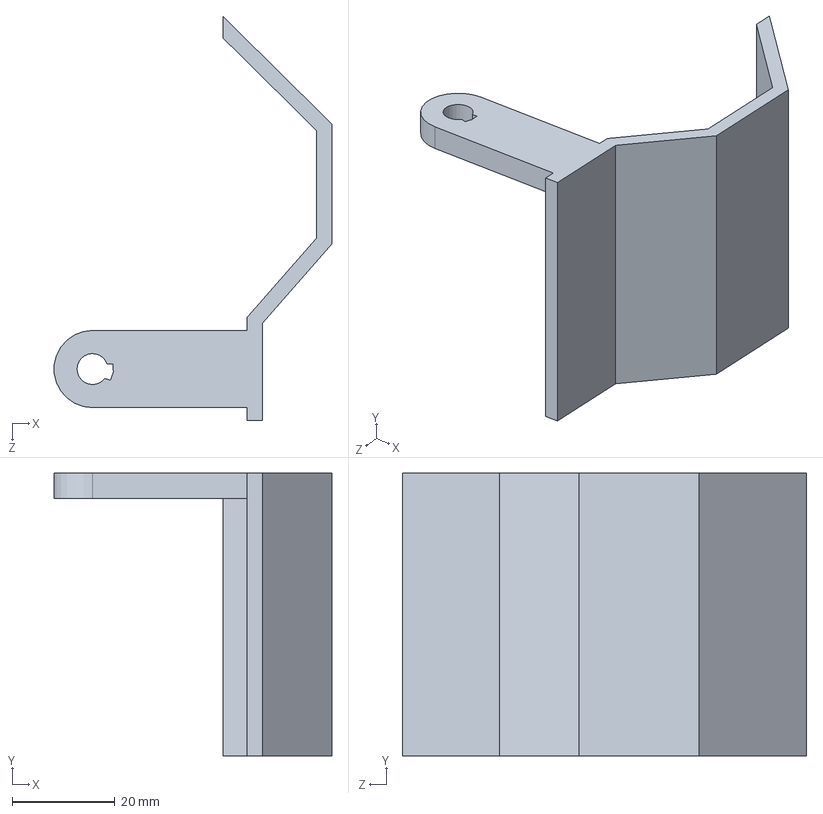
[picture p124: CAD file, 2024-09-04]
CAD/Self_designed_parts/ClawRight.SLDPRT
54.0 x 55.0 x 78.5 mm
