wrog0003/ECE4191/CAD/Self_designed_parts/ClawBracketRight.SLDPRT

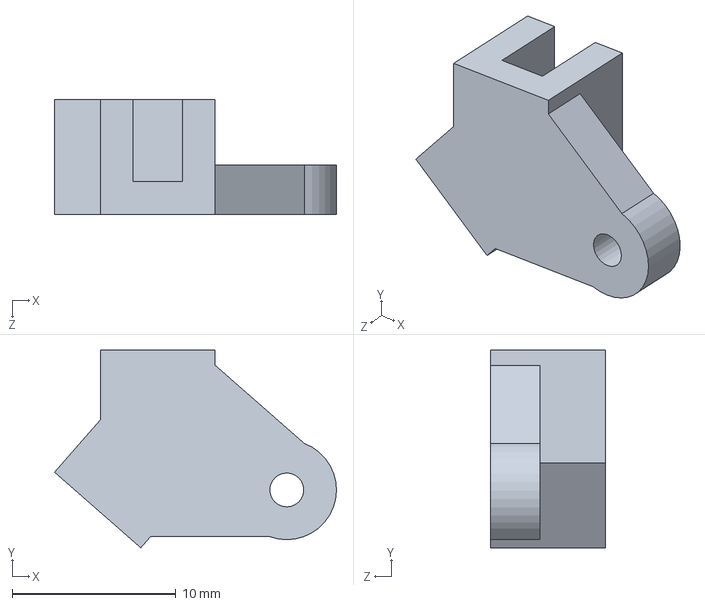
[picture p125: CAD file, 2024-09-04]
CAD/Self_designed_parts/ClawBracketRight.SLDPRT
17.2 x 12.1 x 7.00 mm
