wrog0003/ECE4191/CAD/Self_designed_parts/TennisBall(Max).SLDPRT

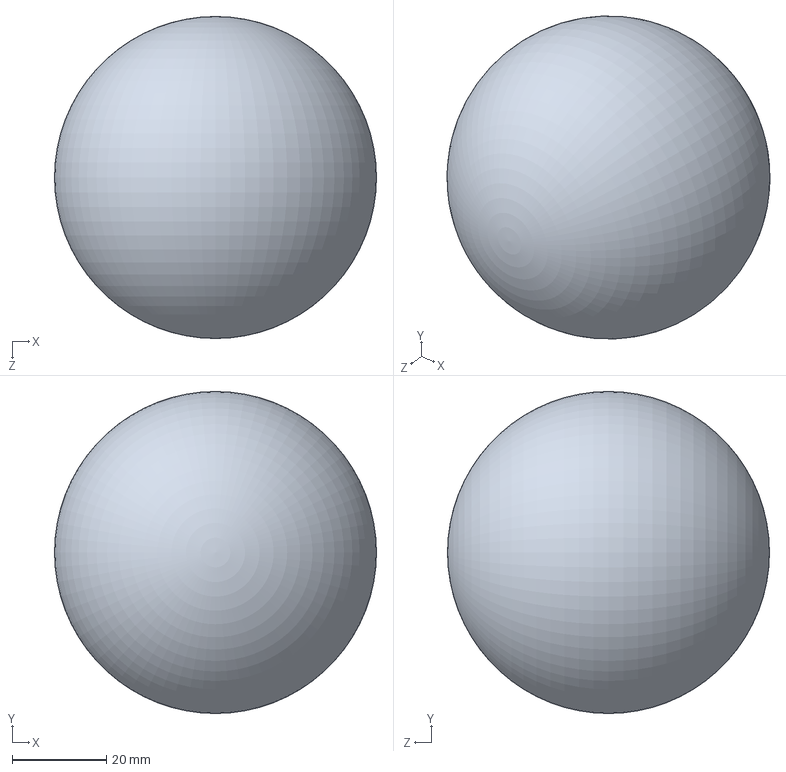
[picture p126: CAD file, 2024-09-04]
CAD/Self_designed_parts/TennisBall(Max).SLDPRT
68.5 x 68.5 x 68.5 mm
