wrog0003/ECE4191/CAD/Self_designed_parts/ClawLeftAssembly.SLDASM

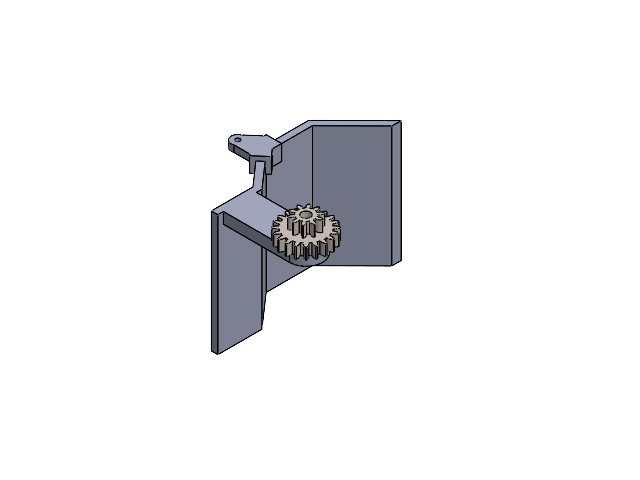
[picture p136: CAD file, 2024-10-03]
CAD/Self_designed_parts/ClawLeftAssembly.SLDASM
ClawLeft
spur gear_am x 2
ClawBracket
