wrog0003/ECE4191/CAD/Self_designed_parts/ClawRightAssembly.SLDASM

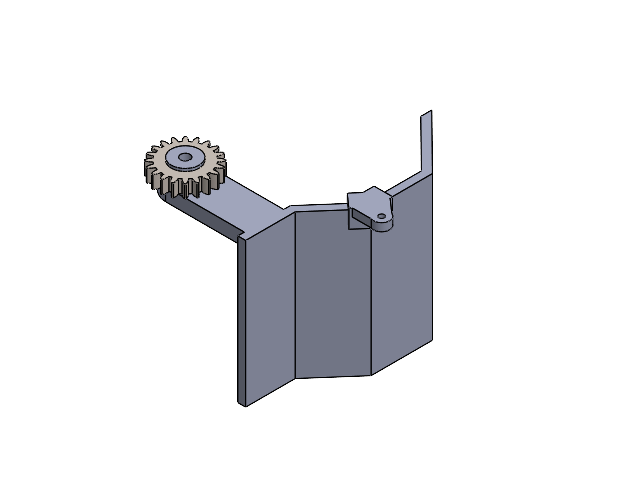
[picture p137: CAD file, 2024-10-03]
CAD/Self_designed_parts/ClawRightAssembly.SLDASM
ClawRight
spur gear_am
ClawBracketRight
ClawGearKey_Right
