wrog0003/ECE4191/CAD/Self_designed_parts/AlignmentAssembly_GearServo.SLDASM

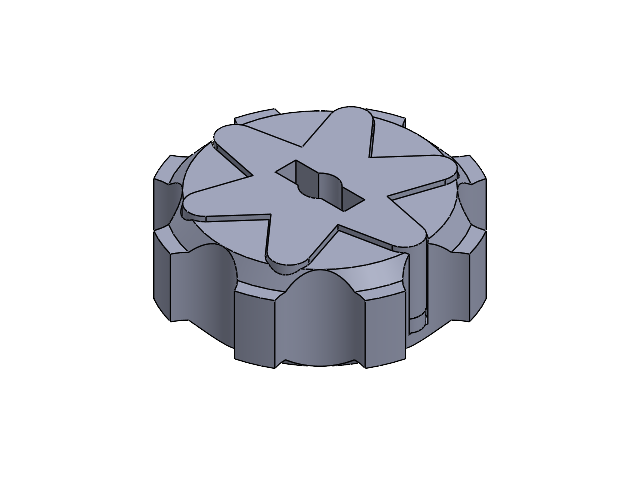
[picture p138: CAD file, 2024-09-30]
CAD/Self_designed_parts/AlignmentAssembly_GearServo.SLDASM
Track_Gear
Servo_MG995_Star_horn
MG995 Gear Cap
