wrog0003/ECE4191/CAD/Self_designed_parts/PusherAssembly.SLDASM

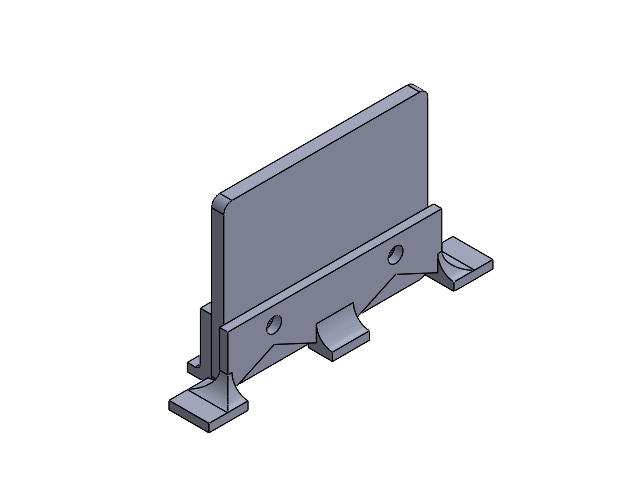
[picture p139: CAD file, 2024-09-16]
CAD/Self_designed_parts/PusherAssembly.SLDASM
Pusher_Base_TriStand
Pusher_Base_DualBase
Pusher_Flap
