wrog0003/ECE4191/CAD/Self_designed_parts/TrackTester_Slave.SLDASM

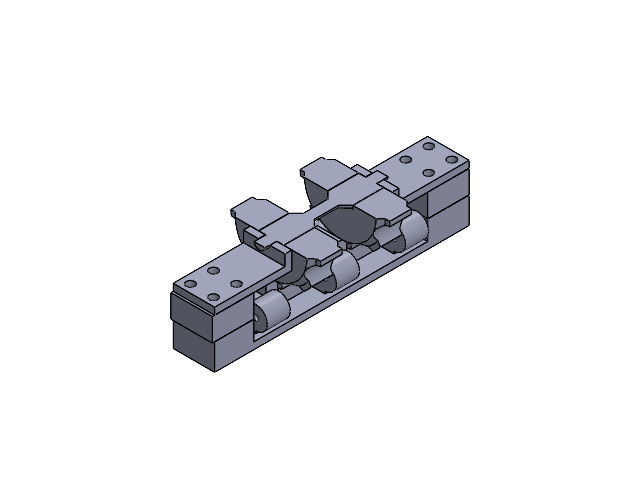
[picture p140: CAD file, 2024-09-16]
CAD/Self_designed_parts/TrackTester_Slave.SLDASM
Track_2.2_70mm
DriveGear_Key x 2
GearMount x 2
GearMountSpacer x 2
TestStand_Slave
Test_Shaft_Slave
