wrog0003/ECE4191/Motor_code/encoders.py

from gpiozero import Motor
from encoderClass import SimpleEncoder
import math
import time

# Constants
WHEEL_DIAMETER = 0.054  # Wheel diameter in meters
WHEEL_BASE = 0.22      # Distance between wheels in meters
COUNTS_PER_REV = 48  # Full quadrature counts per revolution
DIST_PER_COUNT = (math.pi * WHEEL_DIAMETER) / COUNTS_PER_REV

# GPIO pins for encoders
LEFT_ENCODER_A_PIN = 17
LEFT_ENCODER_B_PIN = 27
RIGHT_ENCODER_A_PIN = 18
RIGHT_ENCODER_B_PIN = 22

# Position and orientation
x = 0.0
y = 0.0
theta = 0.0

last_left_count = 0
last_right_count = 0

# Set up the motors
left_motor = Motor(forward=13, backward=19)
right_motor = Motor(forward=5, backward=6)

# Set up the motors (ASSUMING motor controller is wired to these GPIO pins)
left_encoder = SimpleEncoder(LEFT_ENCODER_A_PIN, LEFT_ENCODER_B_PIN)
right_encoder = SimpleEncoder(RIGHT_ENCODER_A_PIN, RIGHT_ENCODER_B_PIN)

def update_position():
    global x, y, theta, last_left_count, last_right_count

    # Get the current counts from the encoders
    left_count, left_direction = left_encoder.get_values()
    right_count, right_direction = right_encoder.get_values()

    # Calculating thhe distance moved by each wheel
    # by getting the difference between the current and previoous count
    # multiplied it by the distance per count
    delta_left = (left_count - last_left_count) * DIST_PER_COUNT
    delta_right = (right_count - last_right_count) * DIST_PER_COUNT

    # Storing previous count for the next cycle
    last_left_count = left_count
    last_right_count = right_count

    # Calculating change in distance and angle
    # Distance is the average of the movement to the right and left
    # Angle is the difference of the movement to the right and left divided by the wheel base
    delta_distance = (delta_left + delta_right) / 2.0
    delta_theta = (delta_right - delta_left) / WHEEL_BASE

    # Update position using trigonometric identity
    theta += delta_theta
    x += delta_distance * math.cos(theta)
    y += delta_distance * math.sin(theta)

def return_to_start(distance, theta):
    # Rotate by theta (modify so the range is from -pi to pi)
    # Move forward by distance
    pass

# Loop to update the position periodically
try:
    while True:
        update_position()
        print(f"Position: (x={x:.2f}, y={y:.2f}, theta={theta:.2f})")
        time.sleep(0.1)

finally:
    left_motor.stop()
    right_motor.stop()
    left_encoder.end()
    right_encoder.end()
