wrog0003/ECE4191/SysC_BallCollection.py

from gpiozero import Button, Servo # for detecting colltion of balls
import RPi.GPIO as GPIO # for use of motors


import GLOBALSM1 # for which pins to use 

from time import sleep # to enable delaying


class SysC_BallCollection:
    '''This system deals with detecting the ball count and moving the conveyer'''
    MAXBALLS = 4 
    LOADTIME = 0.09
    UNLOADTIME = 4
    STOPVALUE = 0.199
    '''The maximum number of balls that the system can hold before it should return to the box'''
    def __init__(self, ConveyerPin: int= GLOBALSM1.servo1, ButtonPin:int = GLOBALSM1.button1) -> None:
        '''Sets up the variables and servo and button pins'''
        self.ballCount = 0
        '''Number of balls in system'''
        self.ballFlag = False
        '''Flag to show that a new ball has entered the system'''
        self.full = False
        '''Flag to indicate that the system is full'''

        #set up servo 
        # self.servo = Servo(ConveyerPin)
        # '''Servo pin that controls the conveyer'''
        # self.servo.mid()# = SysC_BallCollection.STOPVALUE
        GPIO.setup(ConveyerPin,GPIO.OUT)
        self.servo = GPIO.PWM(ConveyerPin, 500)
        self.servo.start(0)

        #set up the button to detect a ball
        self.BallButton = Button(ButtonPin, pull_up=True) # high = logic 1, low = logic 0 
        '''Button to detect balls entering the system'''
        self.BallButton.when_pressed = self.IncrementBall

    def IncrementBall(self,channel)->None:
        '''Callback function to increment the number of balls'''
        print('Ball Collected')
        self.ballCount+=1 
        self.ballFlag =True
    
    def GetBallCount(self)->int:
        '''returns the number of balls in the system'''
        return self.ballCount
    
    def _ResetBallCount(self)->None:
        '''Resets the number of balls in the system'''
        self.ballCount = 0 
    
    def addBallToSystem(self)->bool:
        '''Moves the conveyer enough to lock a ball into the system

        Outputs:    True if the number of balls is the maximum for the system'''
        
        self.servo.start(60) #run the conveyer
        sleep(SysC_BallCollection.LOADTIME/2) # run the conveyer for the correct amount of time 
        self.servo.stop() # stop the conveyer 
        sleep(0.5)
        self.servo.start(60) #run the conveyer
        sleep(SysC_BallCollection.LOADTIME/2) # run the conveyer for the correct amount of time 
        self.servo.stop() # stop the conveyer
        return self.ballCount >=SysC_BallCollection.MAXBALLS # check if the system is full
    
    def unloadBalls(self)->None:
        '''Unloads the system of balls and resets the ball count'''
        for i in range(7):
            self.addBallToSystem()
            sleep(0.5)
        # self.servo.start(60)
        # sleep(SysC_BallCollection.UNLOADTIME) # wait for a full period of the tracks 
        # self.servo.stop()
        self._ResetBallCount() # reset the ball count

    def __str__(self)->str:
        '''overrides the string representation of the class to define data'''
        return f'Ball collection with {self.ballCount} balls'

    def __del__(self)->None:
        '''Deletes the class instance and releases the pins'''
        self.BallButton.close() # release the pin
        self.servo.stop()
        GPIO.cleanup()


if __name__ == "__main__":
    GPIO.setmode(GPIO.BCM) # set pin types 
    robot = SysC_BallCollection(12)
    #robot.unloadBalls()
    robot.addBallToSystem()
    
    
    del robot
