wrog0003/ECE4191/Motor_code/encoderClassTest.py

from gpiozero import Button 
import RPi.GPIO as GPIO
import time
from math import pi, atan2, sqrt, cos, sin

#DEFINE
ANTICLOCKWISE = False
CLOCKWISE = True 

# Set up a simple encoder class to track miltiple encoders on single system
class SimpleEncoder:
    # define initialisation parameters to set up all sections 
    def __init__(self,Apin:int,Bpin:int) -> None:
        self.Apin = Button(Apin, pull_up=True) # high = logic 1, low = logic 0
        self.Bpin = Button(Bpin, pull_up=True) 
        self.encoderCount = 0 # initialise encoder count to 0
        self.clockWise = False # facing in from outside
        # set up interrupts (rising and falling)
        self.Apin.when_pressed = self.encoderCallA 
        self.Bpin.when_pressed = self.encoderCallB
        self.Apin.when_released = self.encoderCall
        self.Bpin.when_released = self.encoderCall

    # interrupt callback functions
    def encoderCallA(self,channel):
        self.encoderCount+=1 # increment encoder count
        if (self.Apin.value and self.Bpin.value):
            self.clockWise = True

    def encoderCallB(self,channel):
        self.encoderCount+=1 # increment encoder count
        if (self.Apin.value and self.Bpin.value):
            self.clockWise = False

    def encoderCall(self,channel):
        self.encoderCount+=1

    #get the state of the encoder 
    def getValues(self)->tuple[int,bool]:
        return [self.encoderCount,self.clockWise]
    
    #function call to relase pins
    def end(self)->None:
        self.Apin.close()
        self.Bpin.close() 

# MOTOR OUTPUT PINS (DRIVING)

# Motor Left 
motor1a = 17
motor1b = 27

# Motor Right 
motor2a = 23
motor2b = 24

# MOTOR INPUT PINS (ENCODERS)

# Define the GPIO Pins to recieve the encoder pulses. 

# Motor Left 
motor1cha = 13
motor1chb = 19

# Motor Right 
motor2cha = 5
motor2chb = 6

# Useful data units: meters
wheelDiameter = 0.054 # diameter of the wheel
wheelBase = 0.22 # distance between the centre of both wheels 
wheelBaseCircumference = pi*wheelBase # circumference of the wheel 
distancePerPulse = wheelDiameter*pi/(75*48) # how far the robot can move per pulse of the encoders
pulsesPerRotation = 48*75

# Set up GPIO pins
GPIO.setmode(GPIO.BCM)

# Set up the output pins 
GPIO.setup(motor1a, GPIO.OUT) 
GPIO.setup(motor1b, GPIO.OUT)
GPIO.setup(motor2a, GPIO.OUT)
GPIO.setup(motor2b, GPIO.OUT)

# Set up the PWM pins
pwm1a = GPIO.PWM(motor1a,1000)
pwm1b = GPIO.PWM(motor1b,1000)
pwm2a = GPIO.PWM(motor2a,1000)
pwm2b = GPIO.PWM(motor2b,1000)

def fowards(duty_cycle:float)->list[GPIO.PWM,GPIO.PWM]:
   
    # input: duty cycle between 0 - 100
    # output: return the active pins

    # drive the motor forwards 
    pwm1a.start(0)
    pwm1b.start(duty_cycle)
    pwm2a.start(0)
    pwm2b.start(duty_cycle)

    return [pwm1b,pwm2b] 

def turn(duty_cycle:float,clockWise:bool)->list[GPIO.PWM,GPIO.PWM]:

    # inputs: 
    # duty cycle between 0 - 100, 
    # clockwise (bool) let you choose if you want to turn clockwise or anticlockwise 

    # output: return the active pins

    if clockWise:
        pwm1a.start(0)
        pwm1b.start(duty_cycle)
        pwm2a.start(duty_cycle)
        pwm2b.start(0)
        return [pwm1b,pwm2a]
    else:
        pwm1a.start(duty_cycle)
        pwm1b.start(0)
        pwm2a.start(0)
        pwm2b.start(duty_cycle)
        return [pwm1a,pwm2b]


# Use this test to verify the direction for the encoder pins
def directionTest()->None:
    EncoderL = SimpleEncoder(motor1cha,motor1chb) # define left motor as a class
    EncoderR = SimpleEncoder(motor2cha,motor2chb) # define right motor as a class
    fowards(50)
    try:
        time.sleep(2)
        print("True is clockwise, false is anticlockwise")
        [count, direction] =EncoderL.getValues()
        print(f"Left: {direction}\n")
        [count, direction] =EncoderR.getValues()
        print(f"Right: {direction}\n")
        pwm1a.stop()
        pwm1b.stop()
        pwm2a.stop()
        pwm2b.stop()
        GPIO.cleanup()
    except KeyboardInterrupt:
        # STOP and RELEASE all pins 
        pwm1a.stop()
        pwm1b.stop()
        pwm2a.stop()
        pwm2b.stop()
        GPIO.cleanup()
        EncoderL.end()
        EncoderR.end()

def pwmCalibration(speed:float): # PWM Calibration code 

    # Inputs: speed to move at

    EncoderL = SimpleEncoder(motor1cha,motor1chb) # instantiate the left encoder 

    try:
        fowards(speed) # move forward at desired speed and print the number of counts
        time.sleep(2)
        print(EncoderL.encoderCount)
        pwm1a.stop()
        pwm1b.stop()
        pwm2a.stop()
        pwm2b.stop()
        GPIO.cleanup()
    except KeyboardInterrupt:
        # STOP and RELEASE all GPIO pins
        pwm1a.stop()
        pwm1b.stop()
        pwm2a.stop()
        pwm2b.stop()
        GPIO.cleanup()
        EncoderL.end()

def doughnuts(angle:float)->None:
    EncoderL = SimpleEncoder(motor1cha,motor1chb) # Initalise Motor L 
    EncoderR = SimpleEncoder(motor2cha,motor2chb) # Initialise Motor R 
    distance = angle*wheelBaseCircumference/360 # get the distance that you need to travel to reach that angle  
    pulses = distance/distancePerPulse # calculate the number of pulses that are required to complete the rotation
    turn(50,True) # call turn function, specify speed and whether you want to travel clockwise or anticlockwise 
    try:
        # while your encorder pulses are less than the desired pulses calcaulated for the turn, keep moving
        while (EncoderL.encoderCount<pulses): 
            time.sleep(0.001) 
        # once turn complete, release all resources
        pwm1a.stop()
        pwm1b.stop()
        pwm2a.stop()
        pwm2b.stop()
        GPIO.cleanup()
    except KeyboardInterrupt:
         # STOP and RELEASE all GPIO pins
        pwm1a.stop()
        pwm1b.stop()
        pwm2a.stop()
        pwm2b.stop()
        GPIO.cleanup()
        EncoderL.end()
        EncoderR.end()

##################################controller code 
def pwmControl(pwmDesired:float, pwmMessured:float, Kp:float,Ki:float,e_sum:float,pin:GPIO.PWM)->float:
    # Inputs: 
    # pwmDesired: desired speed expressed as a PWM duty cycle
    # pwmMeasured: what the measured PWM of the motor actually is 
    # Kp: proptional constant 
    # Ki: integral constant 
    # e_sum: accumulation of errors 

    # Outputs 
    # e_sum = accumulation of errors 


    dutyCycle = min(max(0,Kp*(pwmDesired-pwmMessured)+Ki*e_sum),100) # calcualte the duty cycle to minimise error 
    e_sum += (pwmDesired-pwmMessured) # calculate the new accumualted error 
    pin.start(dutyCycle) # drive one motor at the new calculated speed 
    return e_sum


def gotTo(X:float,Y:float):
    # Function: takes in coordinates (X,Y) and moves to those co-ordinates 

    # Inputs: 
    # X: x coordinate (forwards)
    # Y: y coordinate (left)
    # this is the coordinate system we have defined 

    # calculate important information
    Kp =1
    Ki =0
    angle = atan2(Y,X)*180/pi
    print(wheelBaseCircumference*pi)

    distance = wheelBaseCircumference*abs(angle)/360 # get the distance that needs to be travelled to 
    # achieve required turn
    
    print(distance)
    #by getting the circumference and then multiplying by the angle/360

    numPulses = distance/distancePerPulse # get the number of pulses required to achieve the turn 
    EncoderL = SimpleEncoder(motor1cha,motor1chb) # set up Left Motor
    EncoderR = SimpleEncoder(motor2cha,motor2chb) # set up right Motor 
    speed =30 # define the speed at which to travel

    # set the encoder count to 0
    oldEncoderCountL = 0
    oldEncoderCountR = 0 
    errorRight = 0 
    errorLeft =0
    leftPin = None
    rightPin = None 
    try: 
        # rotate
        if (angle >-1 and angle <1): # no rotation required 
            time.sleep(0.01)
        elif (angle>0):
            [leftPin,rightPin]= turn(speed,False)# rotate CCW
        else: 
            [leftPin,rightPin]=turn(speed,True)# rotatte CW 
        while (EncoderL.encoderCount <numPulses):
            # newCount = EncoderR.encoderCount-oldEncoderCountR
            # oldEncoderCountR = EncoderR.encoderCount
            # errorRight= pwmControl(speed,newCount,Kp,Ki,errorRight,rightPin)
            # newCount = EncoderL.encoderCount-oldEncoderCountL
            # oldEncoderCountL = EncoderL.encoderCount
            # errorLeft= pwmControl(speed,newCount,Kp,Ki,errorLeft,leftPin)
            time.sleep(0.02)
        # stop rotating 
        pwm1a.stop()
        pwm1b.stop()
        pwm2a.stop()
        pwm2b.stop()
        
        # Now that the robot have reached its desired angle, we want to drive it forward a certain distance 
        distance = sqrt(X**2+Y**2) # calculate distance to drive forward 
        encoderOldCount = EncoderL.encoderCount # update encoder count 
        numPulses = (distance/distancePerPulse)+encoderOldCount # get the new final target pulses
        fowards(speed) # drive forwards 
        while (EncoderL.encoderCount <numPulses):# keep going fowards until you reach the desired number of pulses 
            # newCount = EncoderR.encoderCount-oldEncoderCountR
            # oldEncoderCountR = EncoderR.encoderCount
            # errorRight= pwmControl(speed,newCount,Kp,Ki,errorRight,rightPin)
            # newCount = EncoderL.encoderCount-oldEncoderCountL
            # oldEncoderCountL = EncoderL.encoderCount
            # errorLeft= pwmControl(speed,newCount,Kp,Ki,errorLeft,leftPin)
            time.sleep(0.02)
        pwm1a.stop()
        pwm1b.stop()
        pwm2a.stop()
        pwm2b.stop()
        GPIO.cleanup()
        
    except KeyboardInterrupt:
         # STOP and RELEASE all GPIO pins
        pwm1a.stop()
        pwm1b.stop()
        pwm2a.stop()
        pwm2b.stop()
        GPIO.cleanup()
        EncoderL.end()
        EncoderR.end()


def gotToAndReturn(X:float,Y:float):
    # Function: takes in coordinates (X,Y) and moves to those co-ordinates and then back home 
    # keep track of location relative to starting position

    # Inputs: 
    # X: x coordinate (forwards) meters
    # Y: y coordinate (left) meters
    # this is the coordinate system we have defined 

    # calculate important information
    angle = atan2(Y,X)*180/pi # angle to target point
    distance = wheelBaseCircumference*abs(angle)/360 # get the distance that needs to be travelled to 
    
    print(distance)
    #by getting the circumference and then multiplying by the angle/360

    # achieve required turn
    numPulses = distance/distancePerPulse # get the number of pulses required to achieve the turn 
    EncoderL = SimpleEncoder(motor1cha,motor1chb) # set up Left Motor
    EncoderR = SimpleEncoder(motor2cha,motor2chb) # set up right Motor
    speed =30 # define the speed at which to travel

    # set the encoder count to 0
    oldEncoderCountL = 0
    oldEncoderCountR = 0 

    leftPin = None
    rightPin = None 

    # define variables for robot position
    dt = 0.1 
    x_old = 0
    y_old = 0
    phi_old = 0 

    try: 
        # rotate
        if (angle >-1 and angle <1): # no rotation required 
            time.sleep(0.01)
        elif (angle>0):
            [leftPin,rightPin]= turn(speed,False)# rotate CCW
        else: 
            [leftPin,rightPin]=turn(speed,True)# rotatte CW 
        while (EncoderL.encoderCount <numPulses):
            x_old, y_old, phi_old = robot_position(EncoderL.encoderCount, EncoderR.encoderCount, dt, x_old, y_old, phi_old)
            time.sleep(dt)
        # stop rotating 
        pwm1a.stop()
        pwm1b.stop()
        pwm2a.stop()
        pwm2b.stop()
        
        # Now that the robot have reached its desired angle, we want to drive it forward a certain distance 
        distance = sqrt(X**2+Y**2) # calculate distance to drive forward 
        encoderOldCount = EncoderL.encoderCount # update encoder count 
        numPulses = (distance/distancePerPulse)+encoderOldCount # get the new final target pulses
        fowards(speed) # drive forwards 
        while (EncoderL.encoderCount <numPulses):# keep going fowards until you reach the desired number of pulses 
            x_old, y_old, phi_old = robot_position(EncoderL.encoderCount, EncoderR.encoderCount, dt, x_old, y_old, phi_old)
            time.sleep(dt)
        pwm1a.stop()
        pwm1b.stop()
        pwm2a.stop()
        pwm2b.stop()

        ########################## go home 
        # next based on its X, Y and rot, it should go back home 
        #calcualte rotation number of pulses
        #given X and Y, get rotation 
        oldEncoderCountL = EncoderL.encoderCount
        oldEncoderCountR = EncoderR.encoderCount
        angle = atan2(-y_old,-x_old)
        distance = wheelBaseCircumference*abs(angle)/360
        numPulses = (distance/distancePerPulse) + oldEncoderCountL
        if (angle >-1 and angle <1): # no rotation required 
            time.sleep(0.01)
        elif (angle>0):
            [leftPin,rightPin]= turn(speed,ANTICLOCKWISE)# rotate CCW
        else: 
            [leftPin,rightPin]=turn(speed,CLOCKWISE)# rotatte CW 
        while (EncoderL.encoderCount <numPulses):
            x_old, y_old, phi_old = robot_position(EncoderL.encoderCount, EncoderR.encoderCount, dt, x_old, y_old, phi_old)
            time.sleep(dt)
        # stop rotating 
        pwm1a.stop()
        pwm1b.stop()
        pwm2a.stop()
        pwm2b.stop()

        #calculate distance number of pulses 
        oldEncoderCountL = EncoderL.encoderCount
        oldEncoderCountR = EncoderR.encoderCount
        distance = sqrt(x_old**2+y_old**2)
        numPulses = (distance/distancePerPulse)+oldEncoderCountL
        fowards(speed)
        while (EncoderL.encoderCount <numPulses):# keep going fowards until you reach the desired number of pulses 
            x_old, y_old, phi_old = robot_position(EncoderL.encoderCount, EncoderR.encoderCount, dt, x_old, y_old, phi_old)
            time.sleep(dt)

        #should be at home 
        pwm1a.stop()
        pwm1b.stop()
        pwm2a.stop()
        pwm2b.stop()
        GPIO.cleanup()


        
    except KeyboardInterrupt:
         # STOP and RELEASE all GPIO pins
        pwm1a.stop()
        pwm1b.stop()
        pwm2a.stop()
        pwm2b.stop()
        GPIO.cleanup()
        EncoderL.end()
        EncoderR.end()



 #################### LOCALISATION ############################

# code sourced from: https://github.com/felipenmartins/Mobile-Robot-Control/blob/main/odometry-based_localization.ipynb

# we start from a known position (e.g. x = 0, y = 0, phi = 0)
# by counting encoder pulses, we calculate angular speeds of each wheel 
# calculate linear and angular speeds
# calculate displacement 
# update x and y position each cycle


def wheel_speed(dt, EncoderCountL, EncoderCountR, EncoderOldCountL, EncoderOldCountR)->list[float]: 

    # calculate change in angular position of the wheels
    angleL = 2*pi*(EncoderCountL - EncoderOldCountL)/pulsesPerRotation #radians
    angleR = 2*pi*(EncoderCountR - EncoderOldCountR)/pulsesPerRotation

    # calculate angular speed
    wL = angleL/dt
    wR = angleR/dt 

    # Note that units are in radians per second

    return wL, wR, EncoderCountL, EncoderCountR 

def speed(wL, wR, R, D):

    # compute the robot's linear and angular speed
    
    u = R * (wR + wL)/2 # linear speed of the robot. Compute the robot's forward velocity
    w = R/D * (wR-wL) # rotational velocity (i.e. how fast the robot is rotating)

    # u has units of m/s
    # w had units of rad/s

    return u, w

def robot_positionOLD(u, w, x_old, y_old, phi_old, dt):
    
    # calculate change in rotational velocity
    dphi = w*dt 
    phi = phi_old + dphi # calculate new angle 

    # ensure that phi is always between -pi to +pi bc when we sart, angle is 0 --> angle range is b/w -pi to pi 
    if phi >= pi:
        phi -= 2*pi
    elif phi <= -pi:
        phi += 2*pi
    
    # calculate the change in x and y 
    dx = u * cos(phi) * dt 
    dy = u * sin(phi) * dt 

    # calculate the new x and y position 
    x = x_old + dx 
    y = y_old + dy 

    return x, y, phi, x_old, y_old, phi_old

def robot_position(encoderCurrent:list[int], encoderOld:list[int], dt: float, x_old:float, y_old:float, phi_old:float)->list[float]:

    # STEP 1: calculate change in angular position of the wheels
    angleL = 2*pi*(encoderCurrent[0] - encoderOld[0])/pulsesPerRotation # radians
    angleR = 2*pi*(encoderCurrent[1] - encoderOld[1])/pulsesPerRotation # radians

    # update EncoderCount for both L & R motor
    EncoderOldCountL = EncoderCountL
    EncoderOldCountR  = EncoderCountR

    # calculate angular speed
    wL = angleL/dt
    wR = angleR/dt 

    # Note that units are in radians per second

    # STEP 2: compute the robot's linear and angular speed

    # linear speed of the robot. Compute the robot's forward velocity
    u = wheelDiameter/2 * (wR + wL)/2 # m/s

    # rotational velocity (i.e. how fast the robot is rotating)
    w = (wheelDiameter/2)/wheelBase * (wR-wL) # rad/s

    # STEP 3: Update Position

    # calculate change in rotational velocity
    dphi = w*dt 
    phi = phi_old + dphi # calculate new angle 

    # ensure that phi is always between -pi to +pi bc when we sart, angle is 0 --> angle range is b/w -pi to pi 
    if phi >= pi:
        phi -= 2*pi
    elif phi <= -pi:
        phi += 2*pi
    
    # calculate the change in x and y 
    dx = u * cos(phi) * dt 
    dy = u * sin(phi) * dt 

    # calculate the new x and y position 
    x = x_old + dx 
    y = y_old + dy 

    return x, y, phi






# main function

# define startup up variables  

EncoderL = SimpleEncoder(motor1cha,motor1chb) # set up Left Motor
EncoderR = SimpleEncoder(motor2cha,motor2chb) # set up Right Motor 

EncoderOldCountL = 0 # initalise to zero
EncoderOldCountR = 0 # initalise to zero

EncoderCountL = EncoderL.encoderCount
EncoderCountR = EncoderR.encoderCount

dt = 0.1 # time step to calculate position

R = wheelDiameter/2 # radius of the wheels TO CONFIRM VALUES
D = wheelBase # distance between the wheels of the robot TO CONFIRM VALUES

# define robots initial position
x_old = 0 
y_old = 0 
phi_old = 0 

try:
    while(True):
        wL, wR,EncoderOldCountL,EncoderOldCountR = wheel_speed( dt, EncoderL.encoderCount, EncoderR.encoderCount, EncoderOldCountL, EncoderOldCountR)

        u, w = speed(wL, wR, R, D)

        x, y, phi, x_old, y_old, phi_old = robot_position(u, w, x_old, y_old, phi_old, dt)

        time.sleep(dt)
except KeyboardInterrupt:
        pwm1a.stop()
        pwm1b.stop()
        pwm2a.stop()
        pwm2b.stop()
        GPIO.cleanup()
        EncoderL.end()
        EncoderR.end()
